Blake-John/SchoolRobotMatch/ComputerVision/Modules/Aim/0.jpg

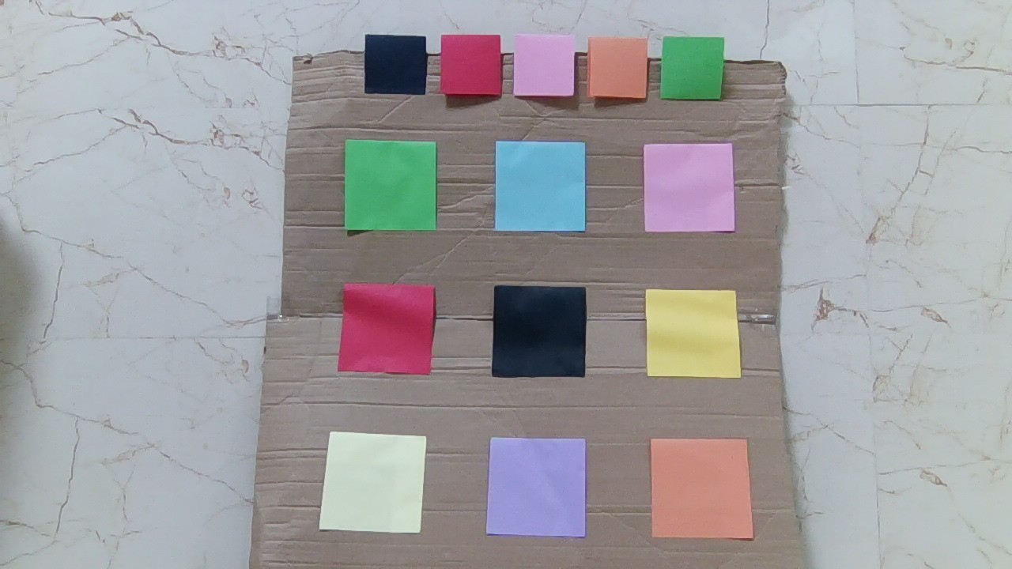
ComputerVision/Modules/Aim/0.jpg
