Blake-John/SchoolRobotMatch/ComputerVision/Modules/Aim/1.jpg

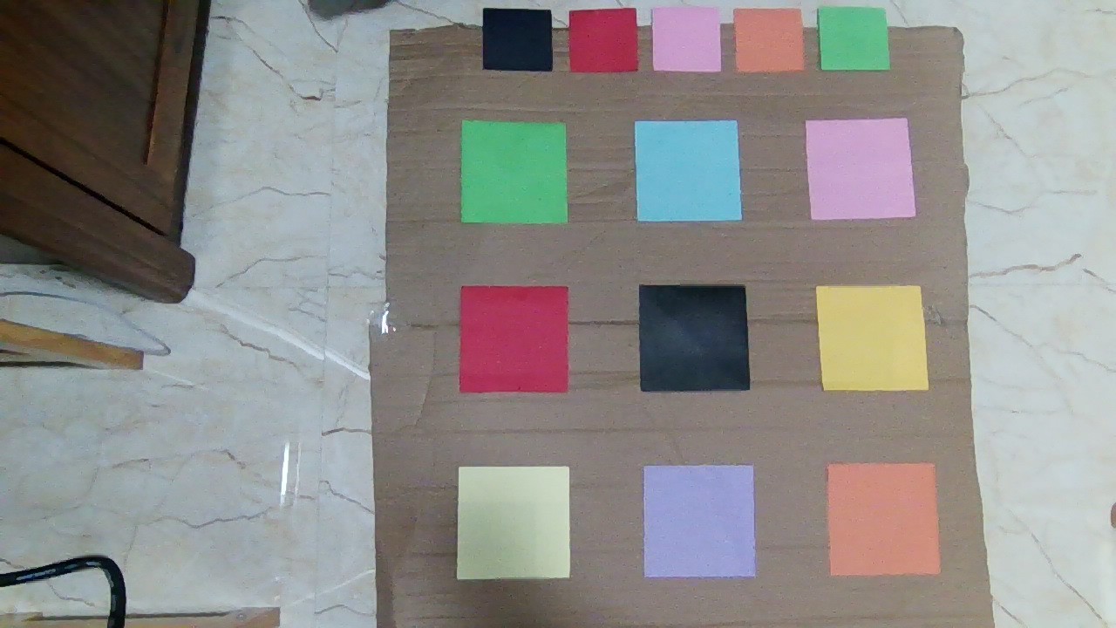
ComputerVision/Modules/Aim/1.jpg
