Blake-John/SchoolRobotMatch/ComputerVision/Modules/AutoAimming/imgs/1-2.png

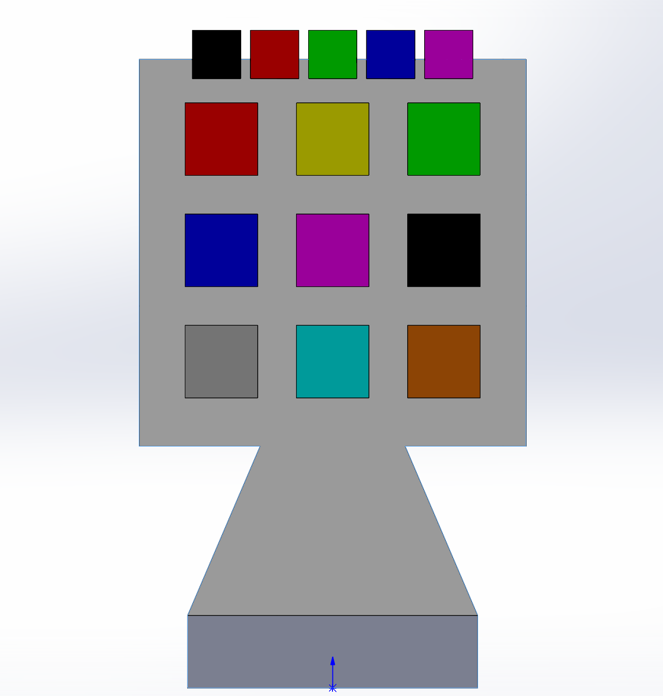
ComputerVision/Modules/AutoAimming/imgs/1-2.png
