Blake-John/SchoolRobotMatch/ComputerVision/Modules/ColorPicker/target.jpg

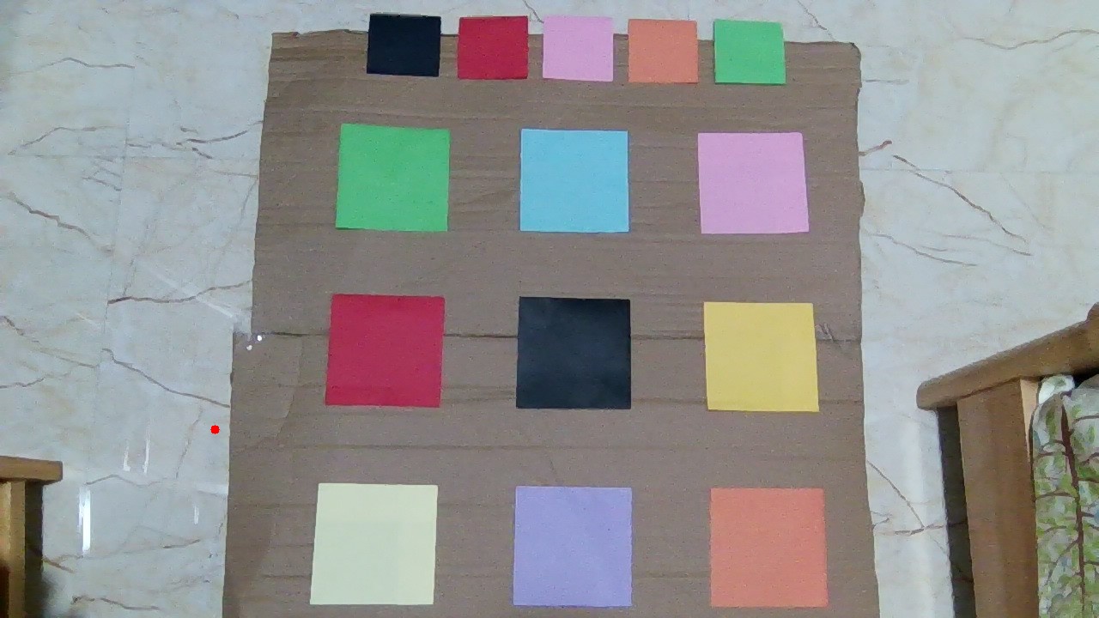
ComputerVision/Modules/ColorPicker/target.jpg
