Blake-John/SchoolRobotMatch/ComputerVision/Modules/GetAngle/4.jpg

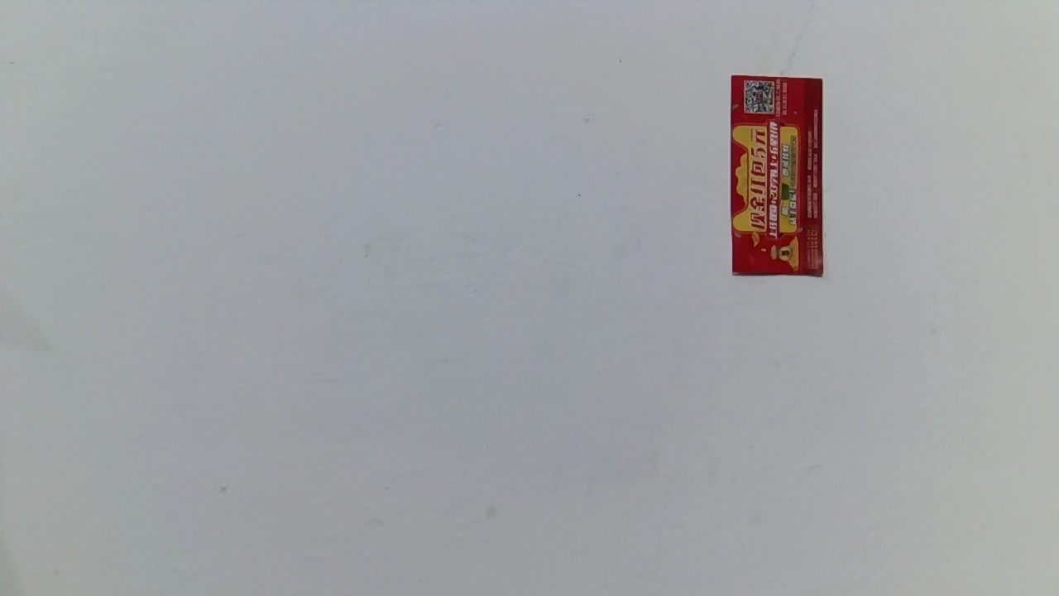
ComputerVision/Modules/GetAngle/4.jpg
