Blake-John/SchoolRobotMatch/ComputerVision/Modules/GetDistance/1.jpg

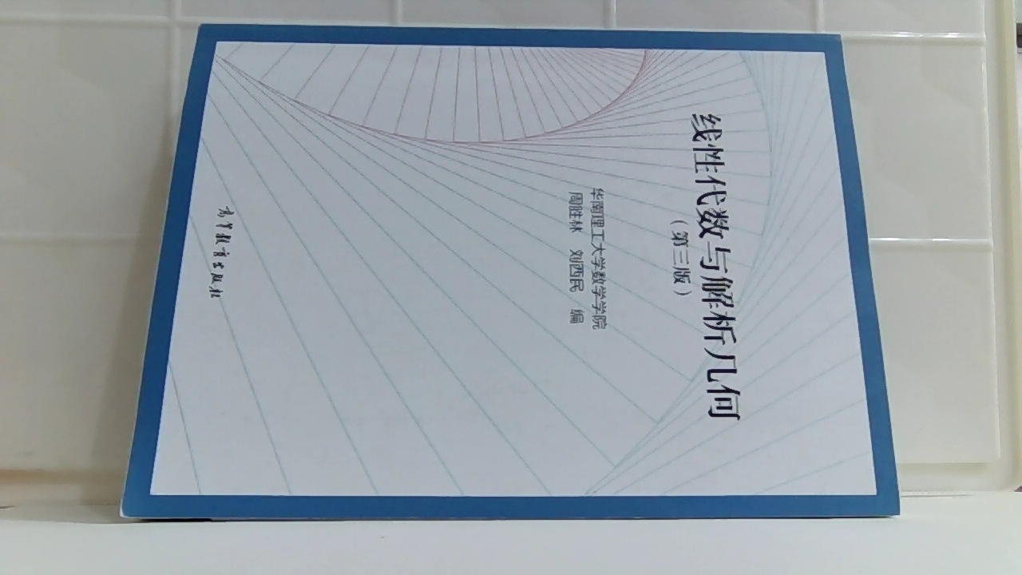
ComputerVision/Modules/GetDistance/1.jpg
