Blake-John/SchoolRobotMatch/ComputerVision/Modules/GetDistance/2.jpg

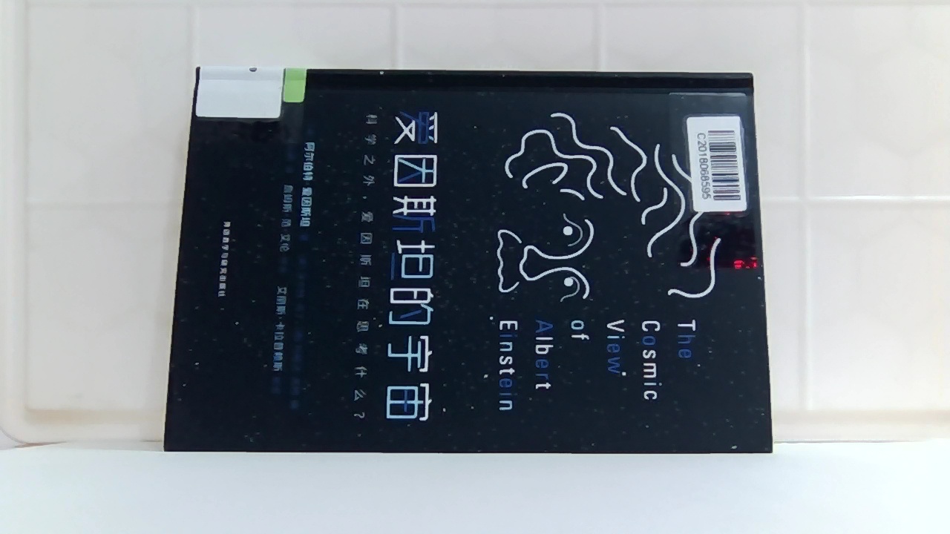
ComputerVision/Modules/GetDistance/2.jpg
