Blake-John/SchoolRobotMatch/ComputerVision/Modules/GetDistance/3.jpg

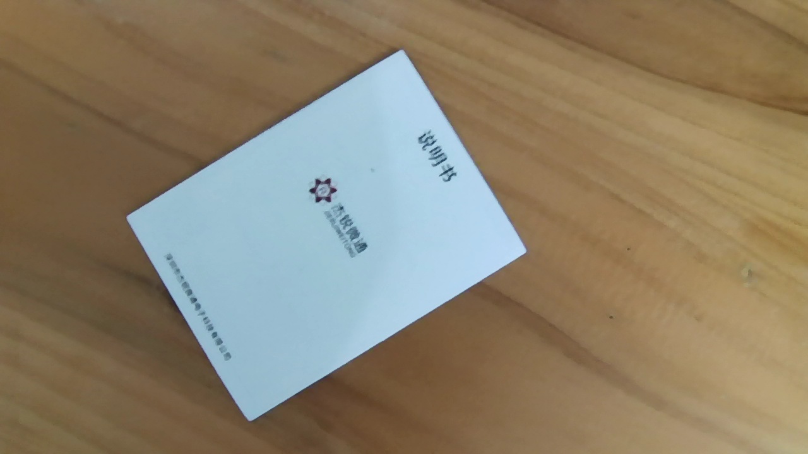
ComputerVision/Modules/GetDistance/3.jpg
