Blake-John/SchoolRobotMatch/ComputerVision/Modules/imgs/106.jpg

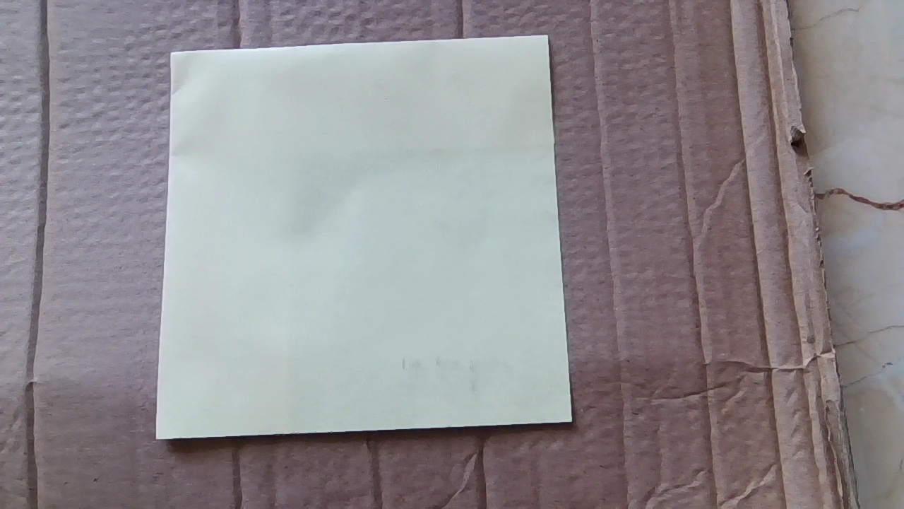
ComputerVision/Modules/imgs/106.jpg
