Blake-John/SchoolRobotMatch/ComputerVision/Modules/imgs/108.jpg

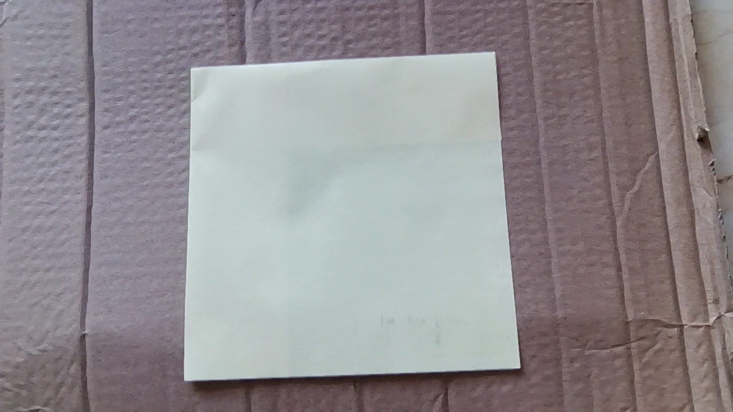
ComputerVision/Modules/imgs/108.jpg
