Blake-John/SchoolRobotMatch/ComputerVision/Modules/imgs/109.jpg

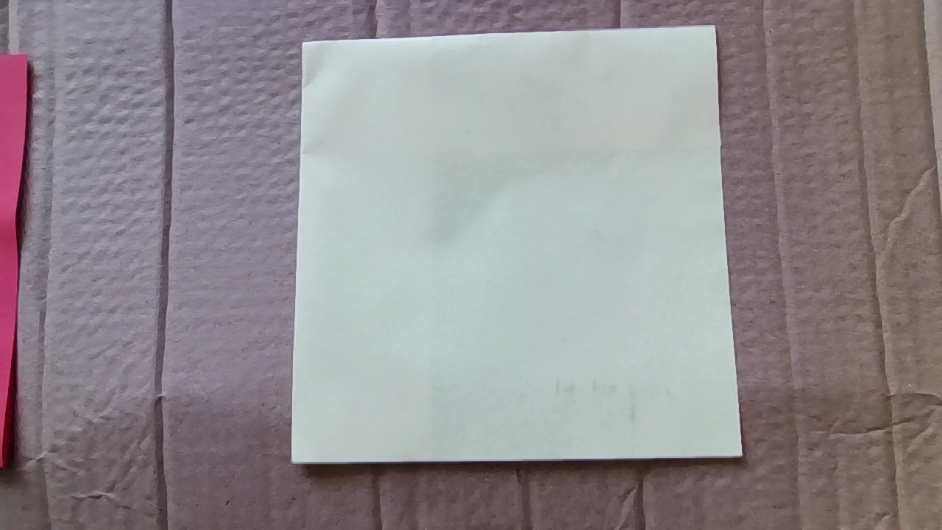
ComputerVision/Modules/imgs/109.jpg
