Blake-John/SchoolRobotMatch/ComputerVision/Modules/imgs/110.jpg

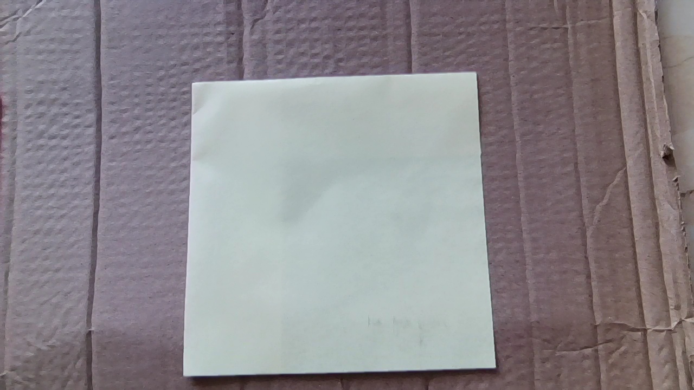
ComputerVision/Modules/imgs/110.jpg
