Blake-John/SchoolRobotMatch/ComputerVision/Modules/imgs/111.jpg

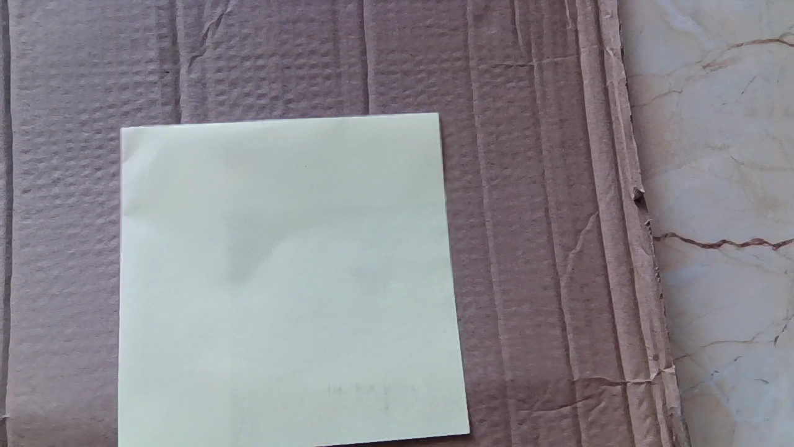
ComputerVision/Modules/imgs/111.jpg
