Blake-John/SchoolRobotMatch/ComputerVision/Modules/imgs/113.jpg

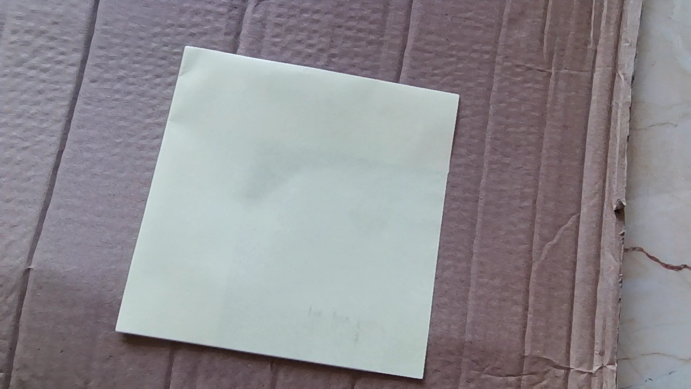
ComputerVision/Modules/imgs/113.jpg
