Blake-John/SchoolRobotMatch/ComputerVision/Modules/imgs/114.jpg

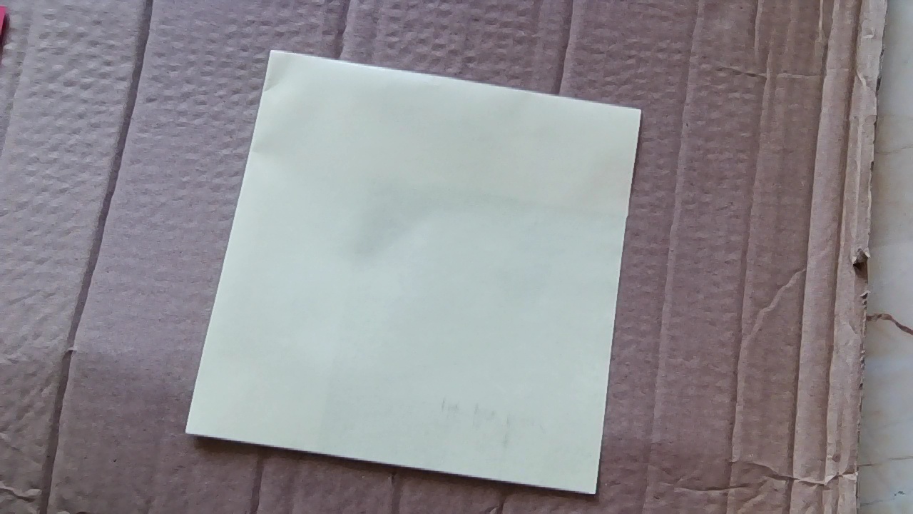
ComputerVision/Modules/imgs/114.jpg
