Blake-John/SchoolRobotMatch/ComputerVision/Modules/imgs/115.jpg

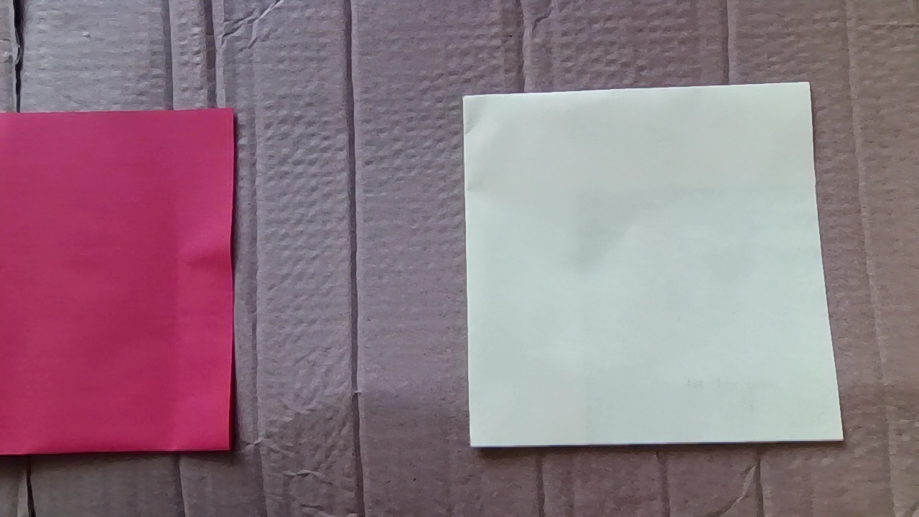
ComputerVision/Modules/imgs/115.jpg
