Blake-John/SchoolRobotMatch/ComputerVision/Modules/imgs/116.jpg

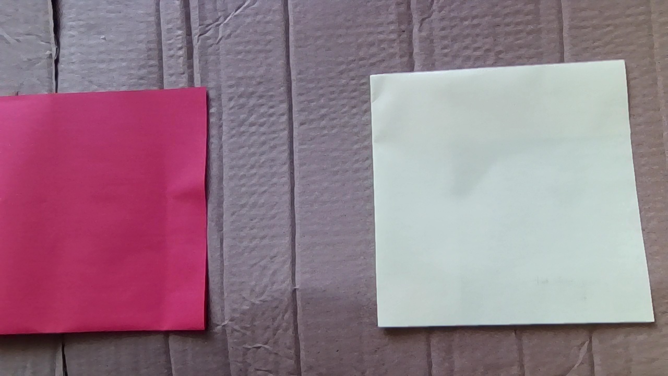
ComputerVision/Modules/imgs/116.jpg
