Blake-John/SchoolRobotMatch/ComputerVision/Modules/imgs/117.jpg

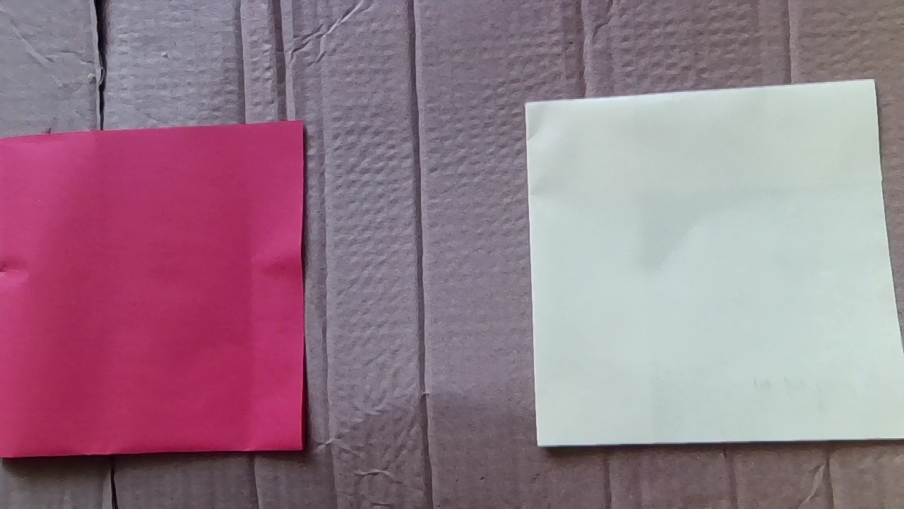
ComputerVision/Modules/imgs/117.jpg
