Blake-John/SchoolRobotMatch/ComputerVision/Modules/imgs/118.jpg

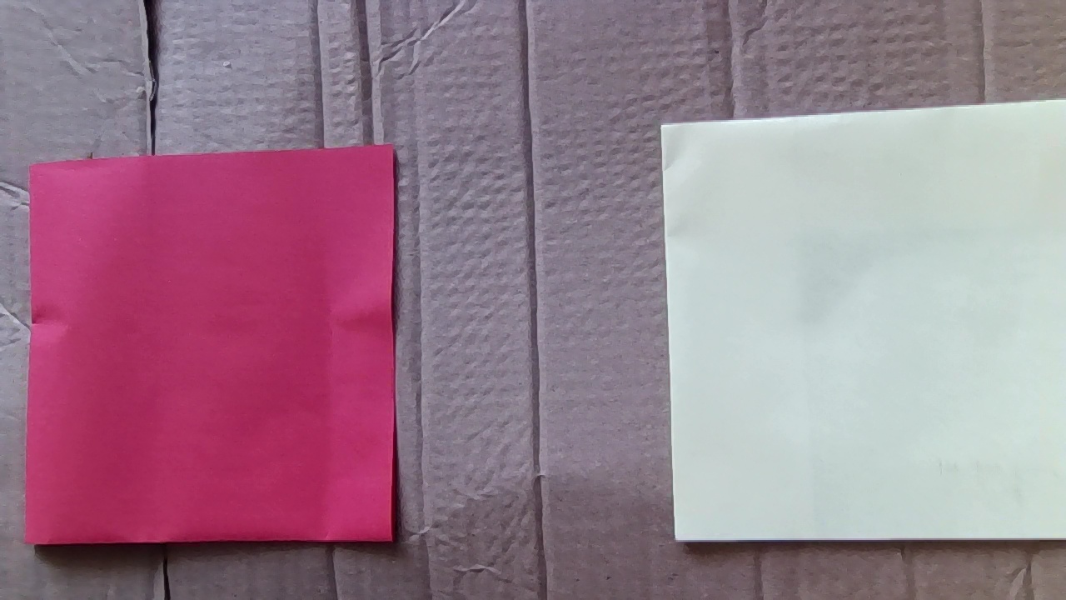
ComputerVision/Modules/imgs/118.jpg
