Blake-John/SchoolRobotMatch/ComputerVision/Modules/imgs/119.jpg

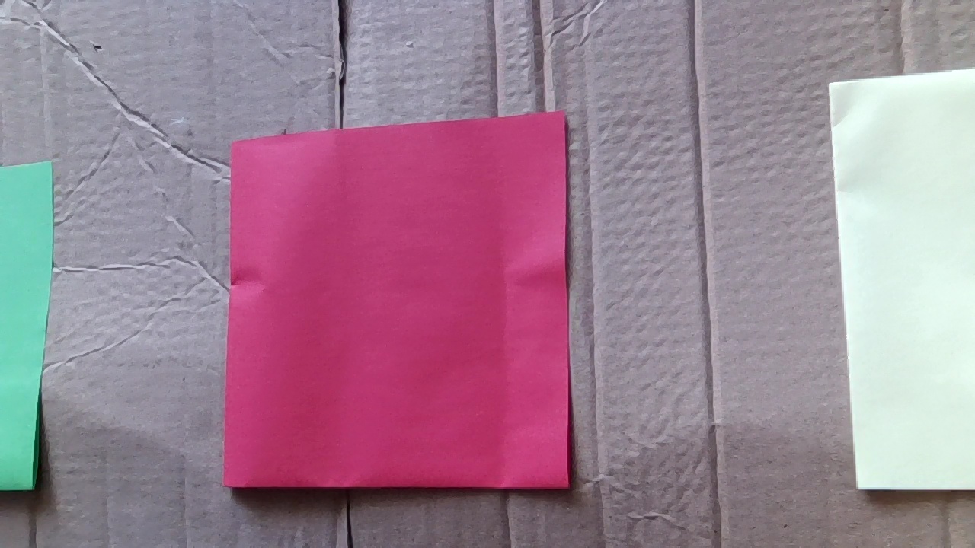
ComputerVision/Modules/imgs/119.jpg
