Blake-John/SchoolRobotMatch/ComputerVision/Modules/imgs/120.jpg

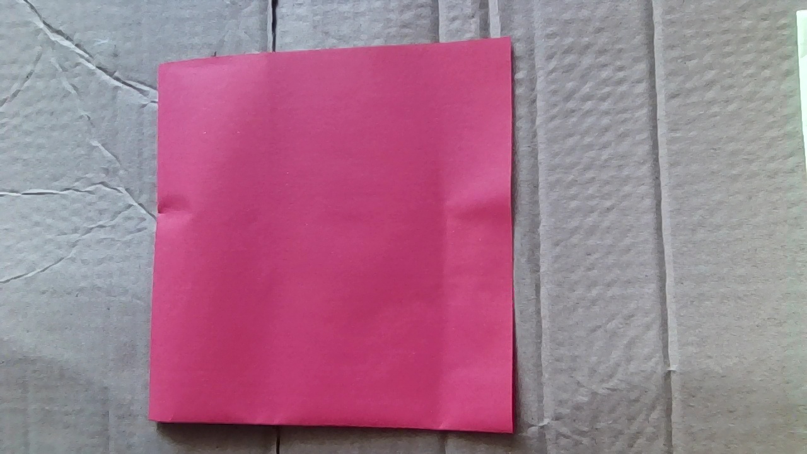
ComputerVision/Modules/imgs/120.jpg
