Blake-John/SchoolRobotMatch/ComputerVision/Modules/imgs/121.jpg

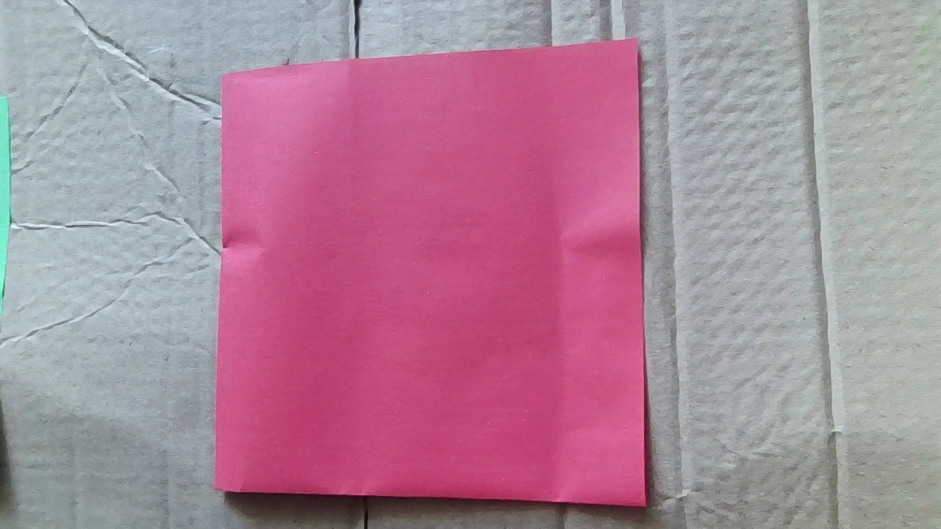
ComputerVision/Modules/imgs/121.jpg
