Blake-John/SchoolRobotMatch/ComputerVision/Modules/imgs/122.jpg

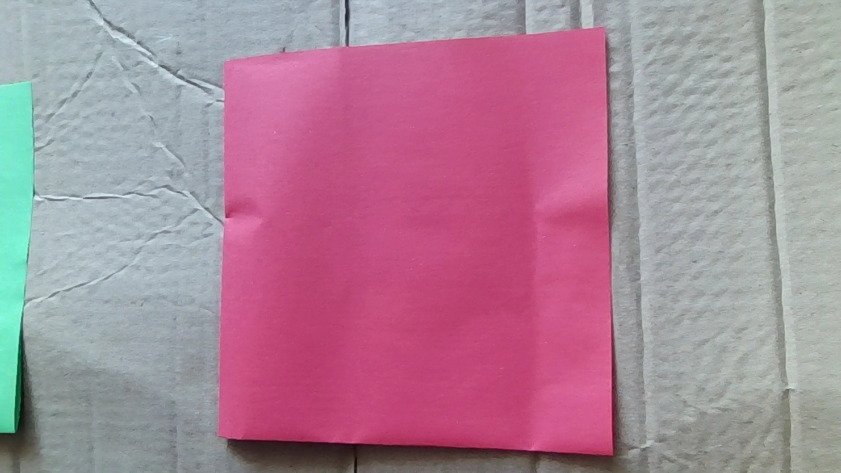
ComputerVision/Modules/imgs/122.jpg
