Blake-John/SchoolRobotMatch/ComputerVision/Modules/imgs/123.jpg

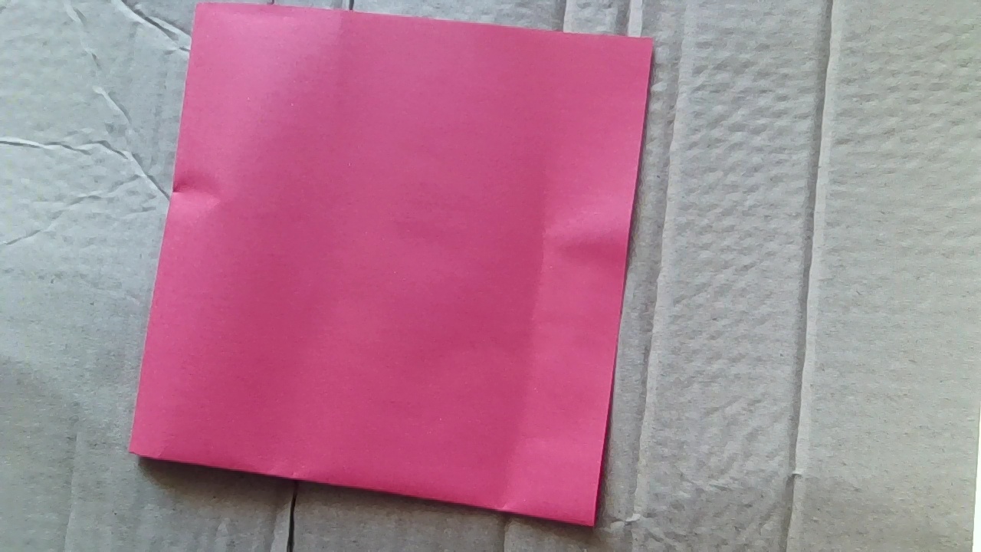
ComputerVision/Modules/imgs/123.jpg
