Blake-John/SchoolRobotMatch/ComputerVision/Modules/imgs/124.jpg

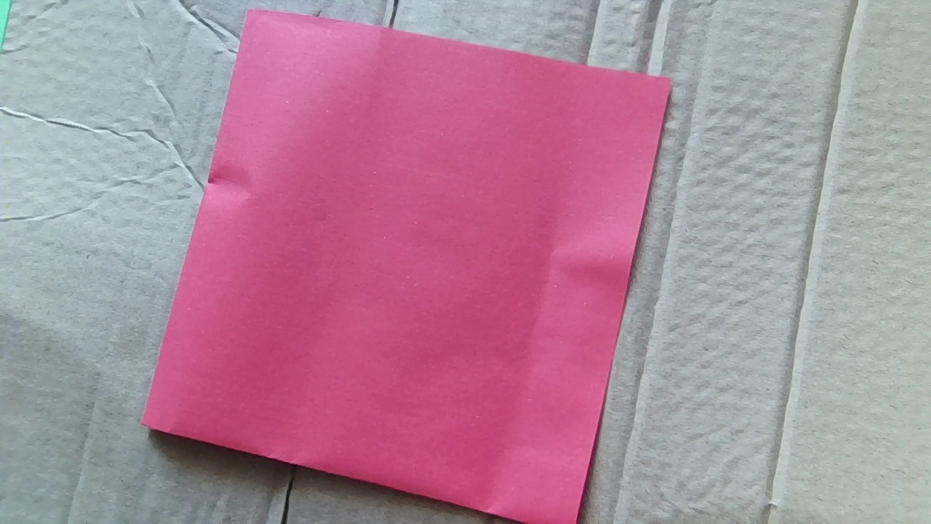
ComputerVision/Modules/imgs/124.jpg
