Blake-John/SchoolRobotMatch/ComputerVision/Modules/imgs/125.jpg

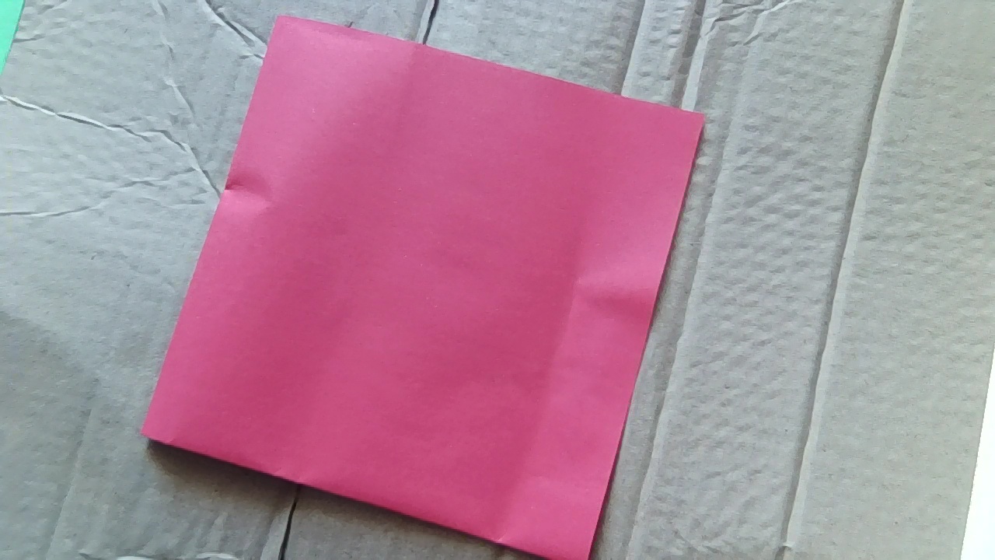
ComputerVision/Modules/imgs/125.jpg
