Blake-John/SchoolRobotMatch/ComputerVision/Modules/imgs/126.jpg

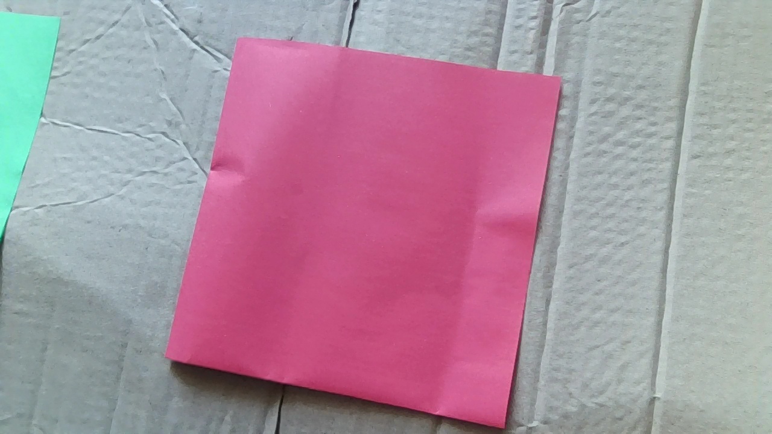
ComputerVision/Modules/imgs/126.jpg
