Blake-John/SchoolRobotMatch/ComputerVision/Modules/imgs/128.jpg

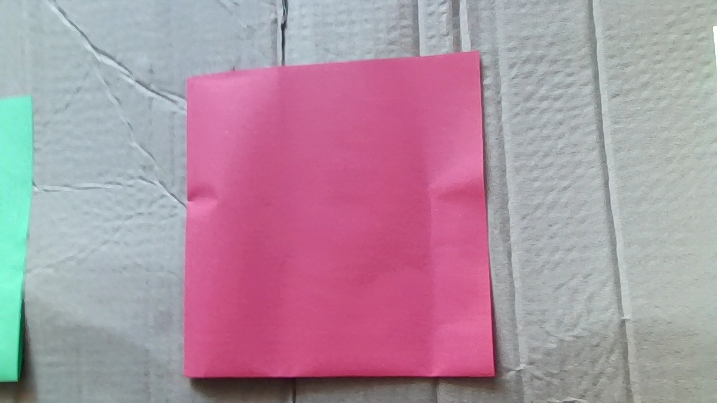
ComputerVision/Modules/imgs/128.jpg
