Blake-John/SchoolRobotMatch/ComputerVision/Modules/imgs/129.jpg

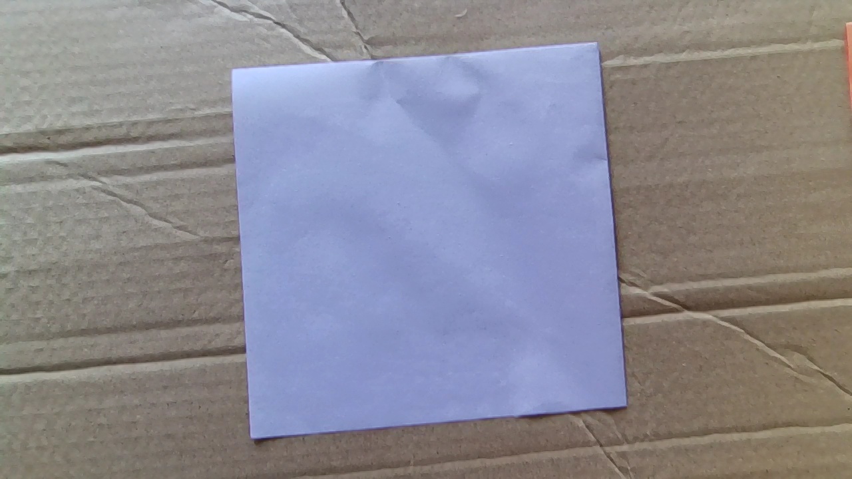
ComputerVision/Modules/imgs/129.jpg
