Blake-John/SchoolRobotMatch/ComputerVision/Modules/imgs/130.jpg

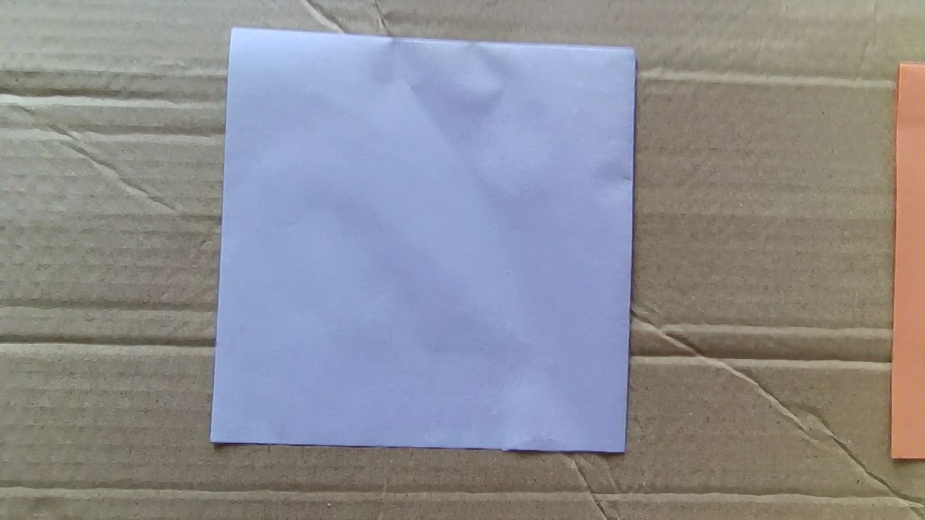
ComputerVision/Modules/imgs/130.jpg
