Blake-John/SchoolRobotMatch/ComputerVision/Modules/imgs/131.jpg

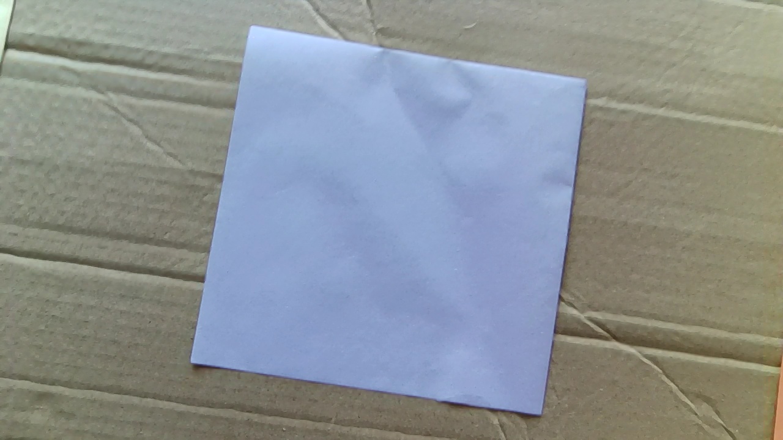
ComputerVision/Modules/imgs/131.jpg
