Blake-John/SchoolRobotMatch/ComputerVision/Modules/imgs/132.jpg

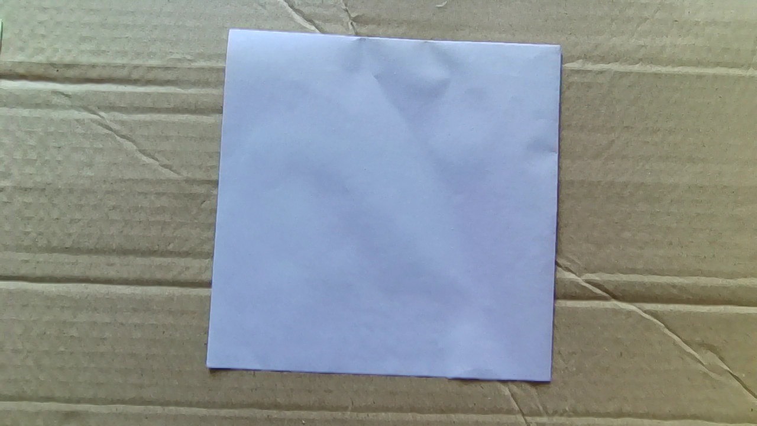
ComputerVision/Modules/imgs/132.jpg
