Blake-John/SchoolRobotMatch/ComputerVision/Modules/imgs/133.jpg

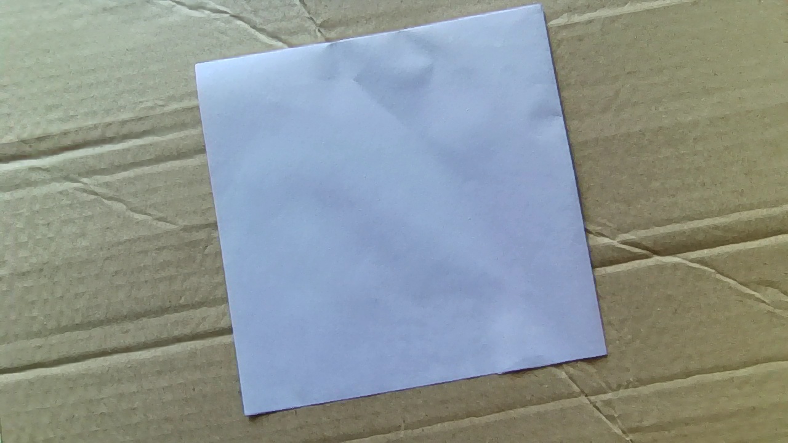
ComputerVision/Modules/imgs/133.jpg
