Blake-John/SchoolRobotMatch/ComputerVision/Modules/imgs/134.jpg

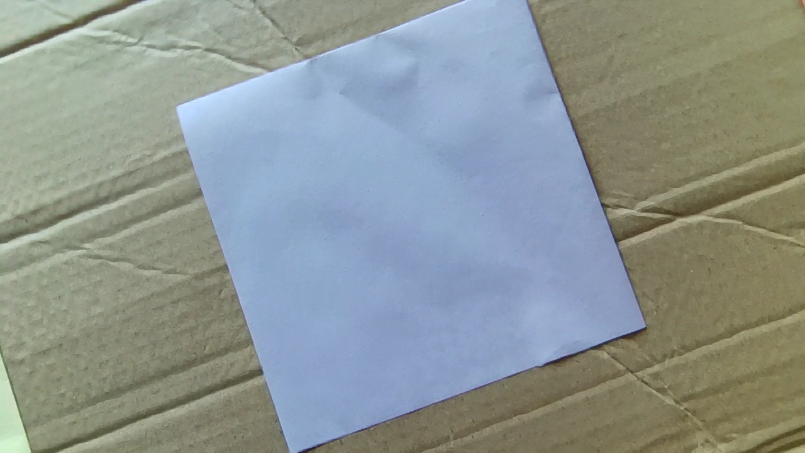
ComputerVision/Modules/imgs/134.jpg
