Blake-John/SchoolRobotMatch/ComputerVision/Modules/imgs/135.jpg

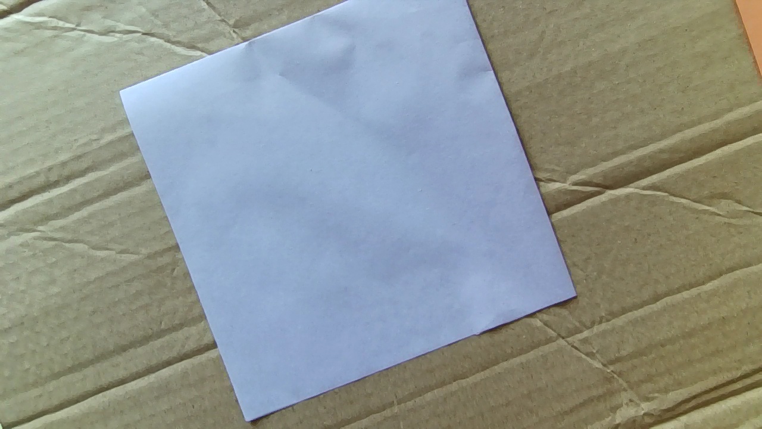
ComputerVision/Modules/imgs/135.jpg
