Blake-John/SchoolRobotMatch/ComputerVision/Modules/imgs/136.jpg

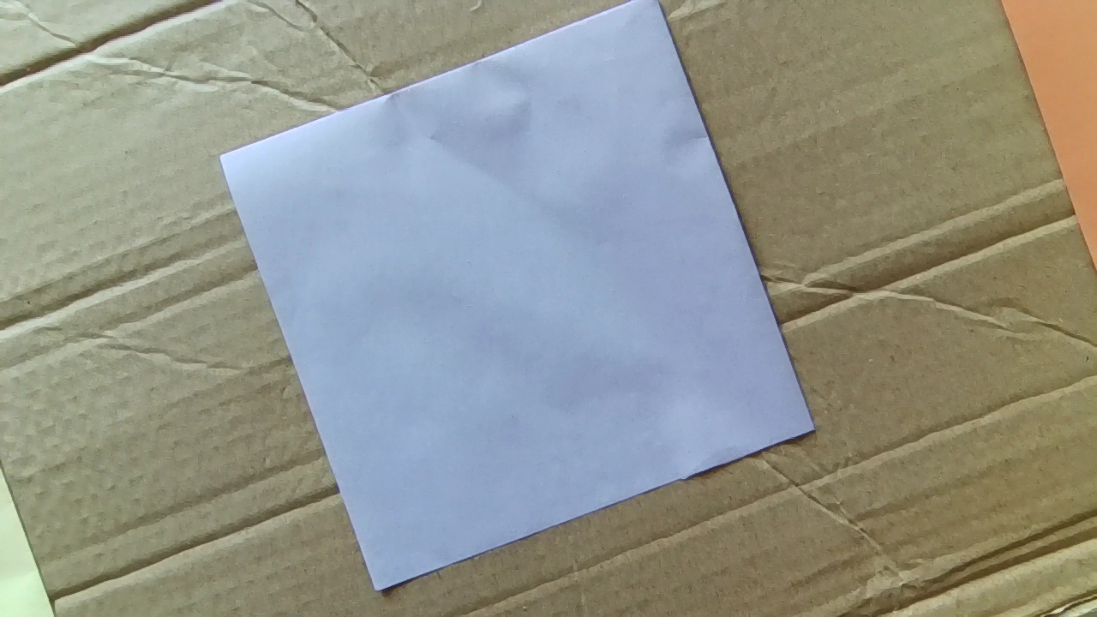
ComputerVision/Modules/imgs/136.jpg
