Blake-John/SchoolRobotMatch/ComputerVision/Modules/imgs/137.jpg

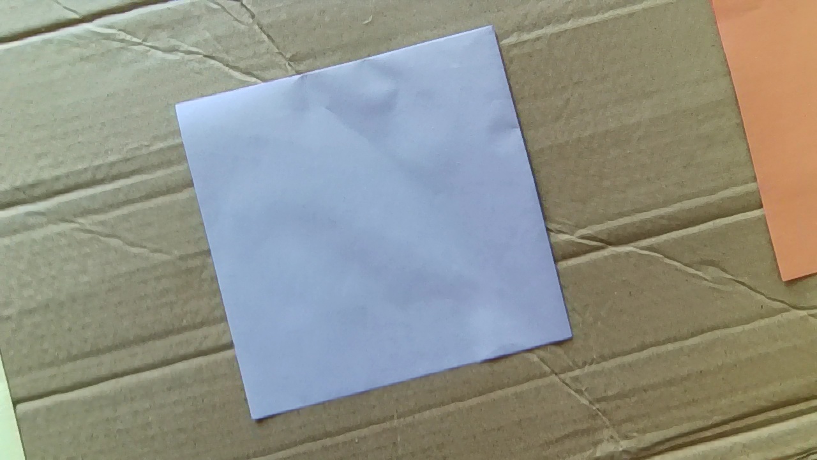
ComputerVision/Modules/imgs/137.jpg
