Blake-John/SchoolRobotMatch/ComputerVision/Modules/imgs/138.jpg

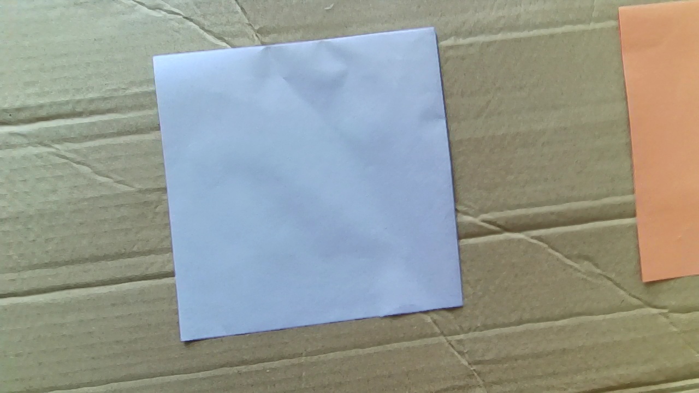
ComputerVision/Modules/imgs/138.jpg
