Blake-John/SchoolRobotMatch/ComputerVision/Modules/imgs/139.jpg

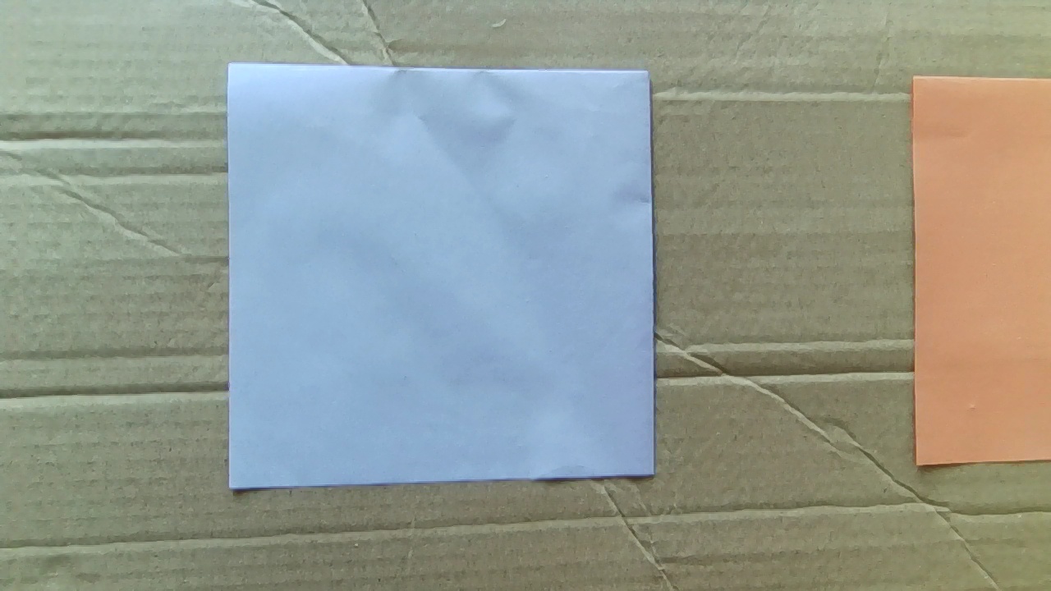
ComputerVision/Modules/imgs/139.jpg
