Blake-John/SchoolRobotMatch/ComputerVision/Modules/imgs/140.jpg

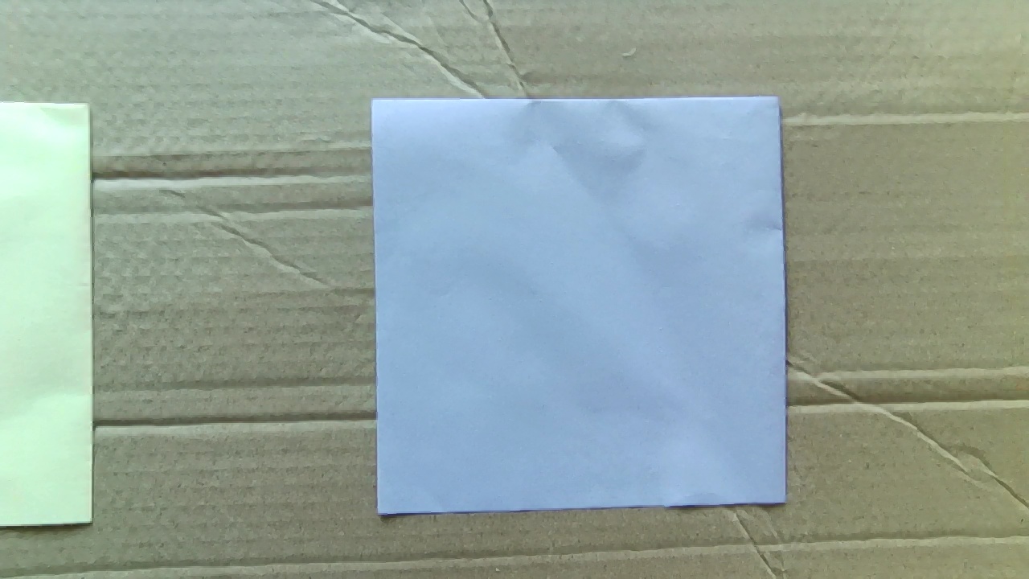
ComputerVision/Modules/imgs/140.jpg
