Blake-John/SchoolRobotMatch/ComputerVision/Modules/imgs/141.jpg

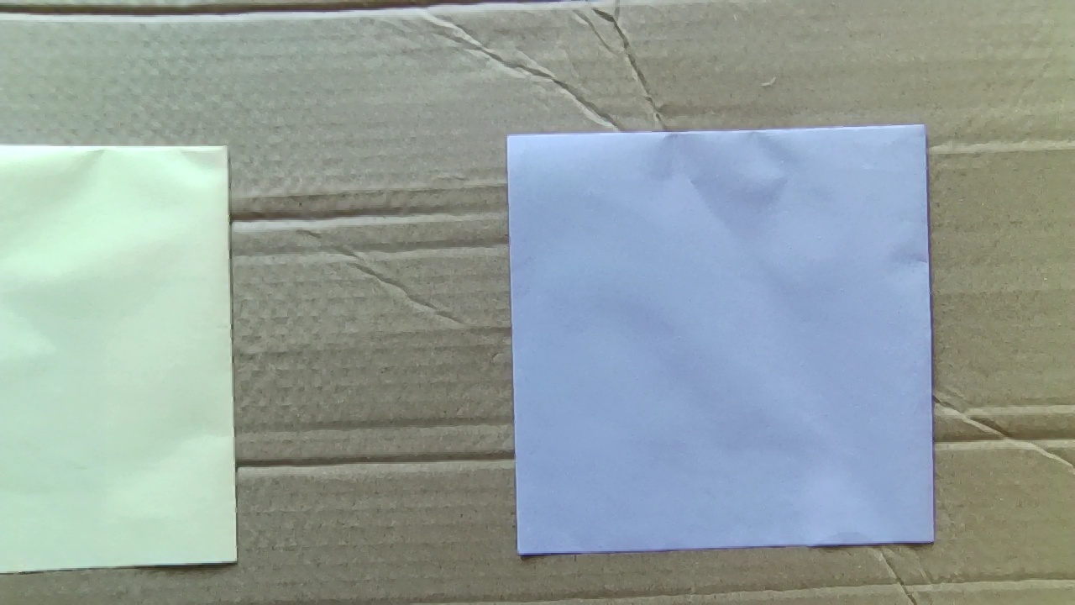
ComputerVision/Modules/imgs/141.jpg
