Blake-John/SchoolRobotMatch/ComputerVision/Modules/imgs/142.jpg

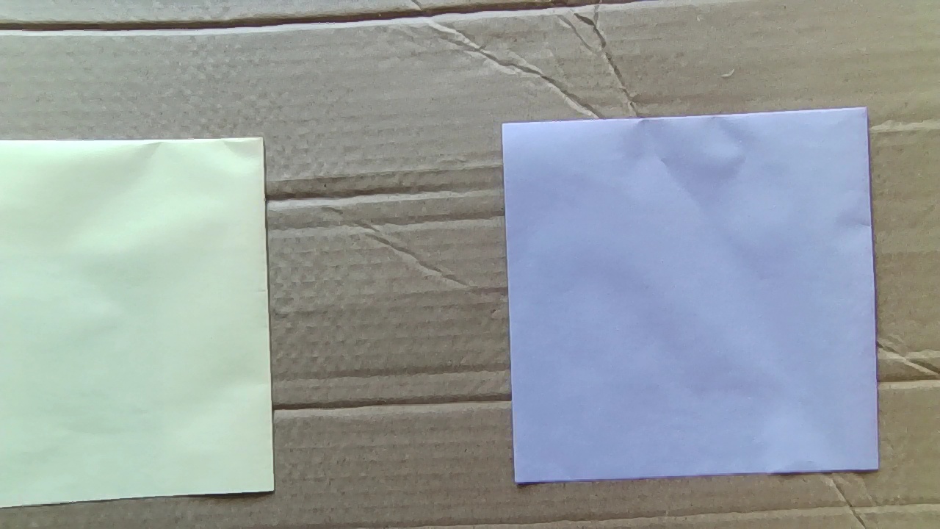
ComputerVision/Modules/imgs/142.jpg
