Blake-John/SchoolRobotMatch/ComputerVision/Modules/imgs/143.jpg

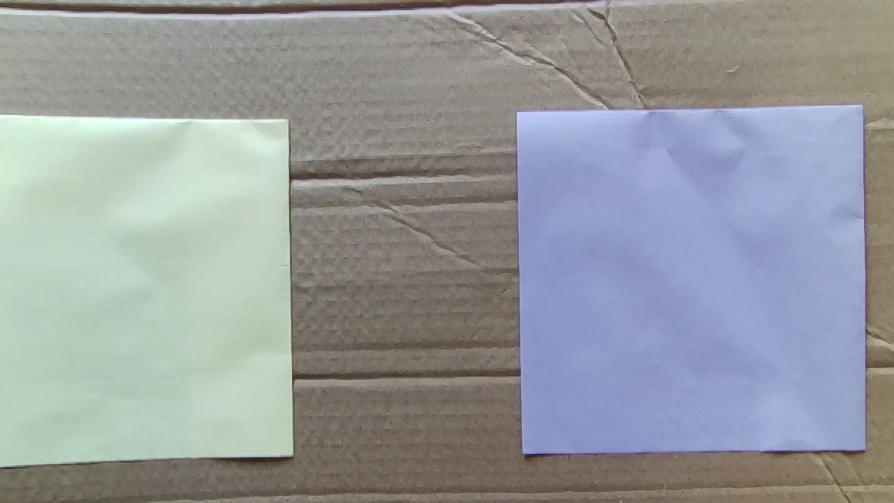
ComputerVision/Modules/imgs/143.jpg
