Blake-John/SchoolRobotMatch/ComputerVision/Modules/imgs/144.jpg

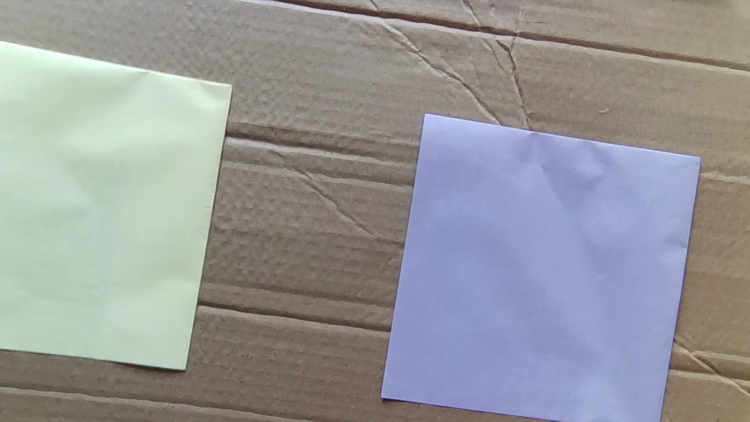
ComputerVision/Modules/imgs/144.jpg
