Blake-John/SchoolRobotMatch/ComputerVision/Modules/imgs/145.jpg

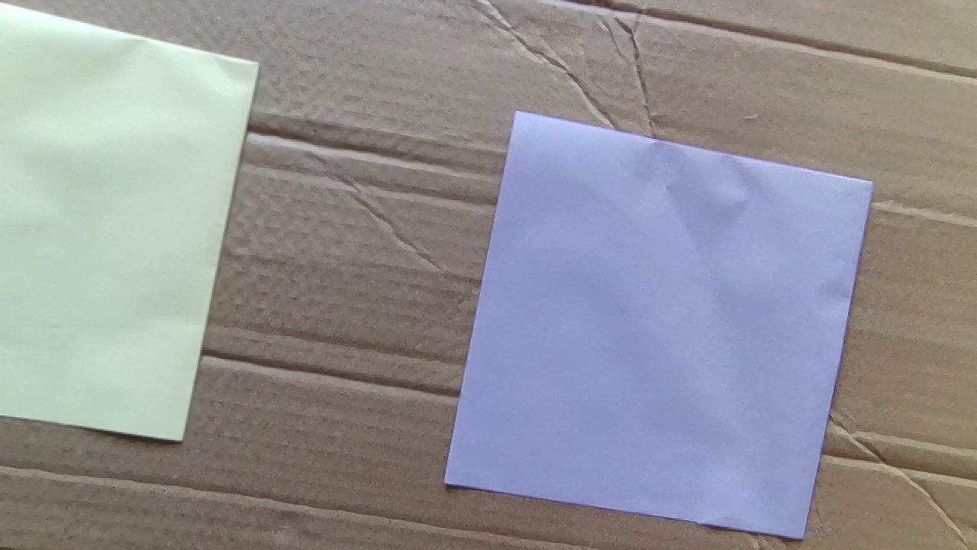
ComputerVision/Modules/imgs/145.jpg
