Blake-John/SchoolRobotMatch/ComputerVision/Modules/imgs/146.jpg

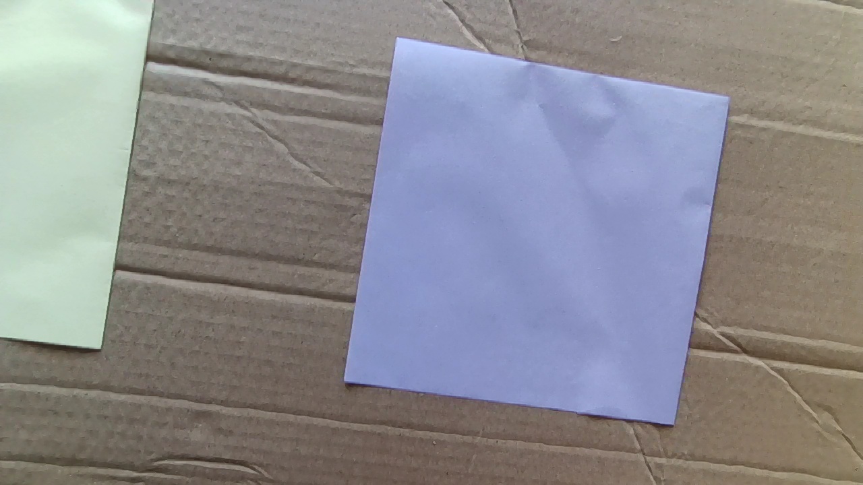
ComputerVision/Modules/imgs/146.jpg
