Blake-John/SchoolRobotMatch/ComputerVision/Modules/imgs/147.jpg

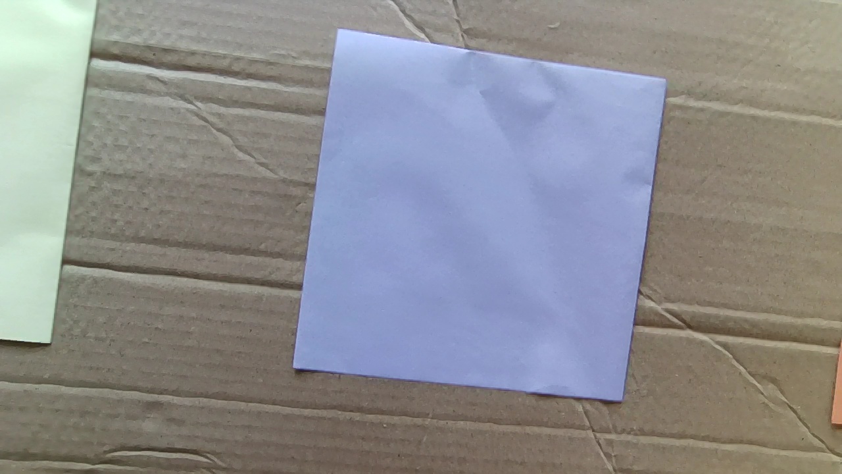
ComputerVision/Modules/imgs/147.jpg
