Blake-John/SchoolRobotMatch/ComputerVision/Modules/imgs/148.jpg

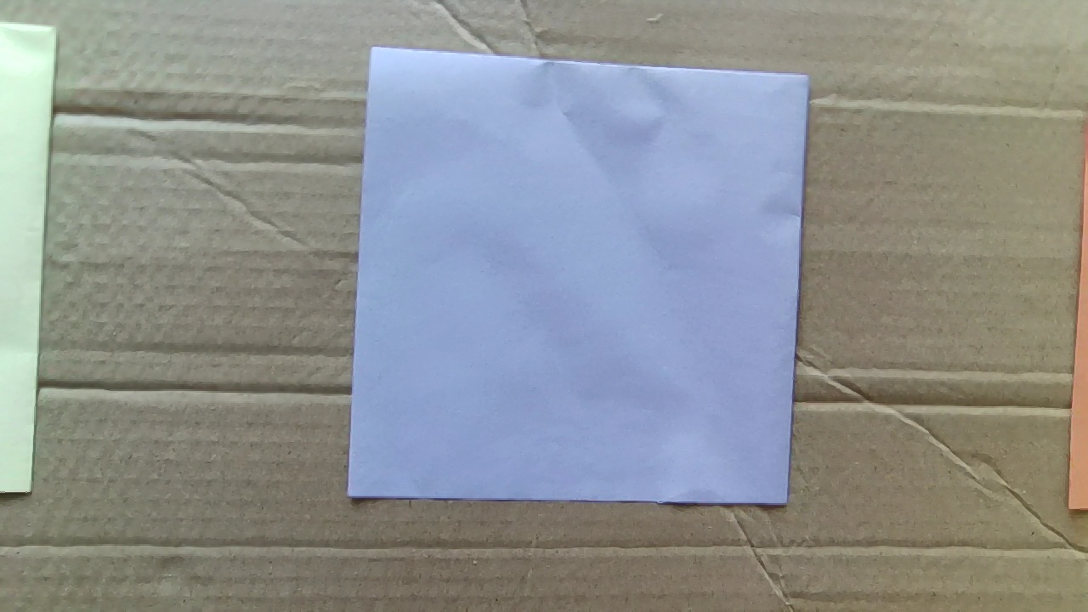
ComputerVision/Modules/imgs/148.jpg
