Blake-John/SchoolRobotMatch/ComputerVision/Modules/imgs/149.jpg

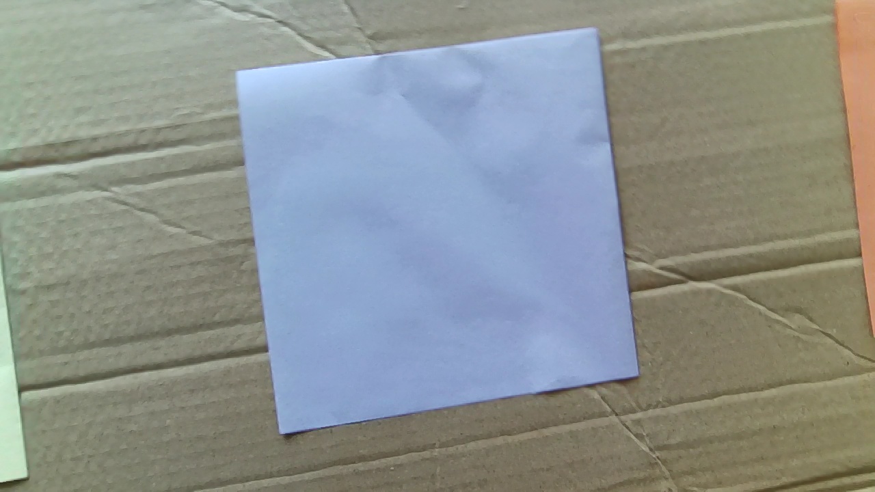
ComputerVision/Modules/imgs/149.jpg
