Blake-John/SchoolRobotMatch/ComputerVision/Modules/imgs/150.jpg

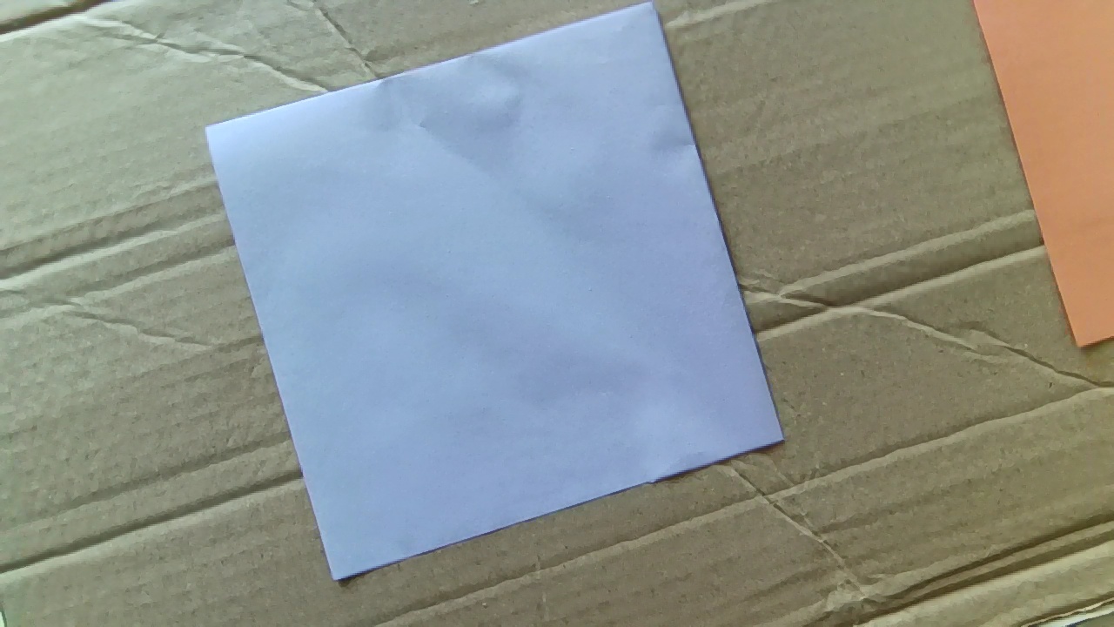
ComputerVision/Modules/imgs/150.jpg
