Blake-John/SchoolRobotMatch/ComputerVision/Modules/imgs/151.jpg

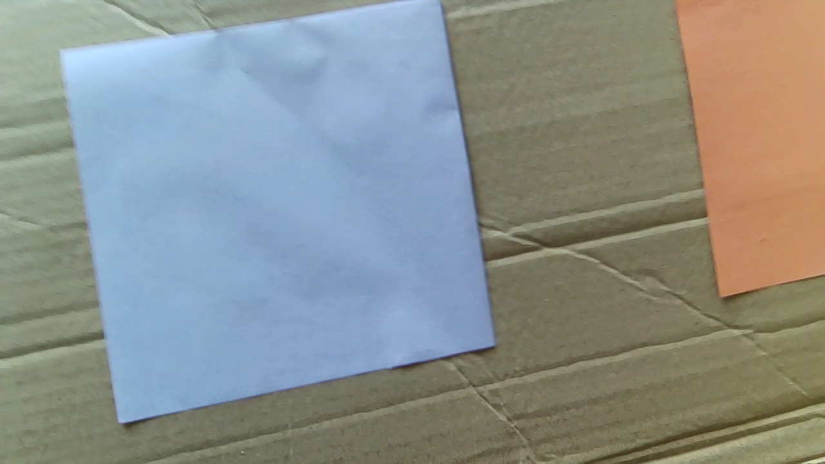
ComputerVision/Modules/imgs/151.jpg
