Blake-John/SchoolRobotMatch/ComputerVision/Modules/imgs/152.jpg

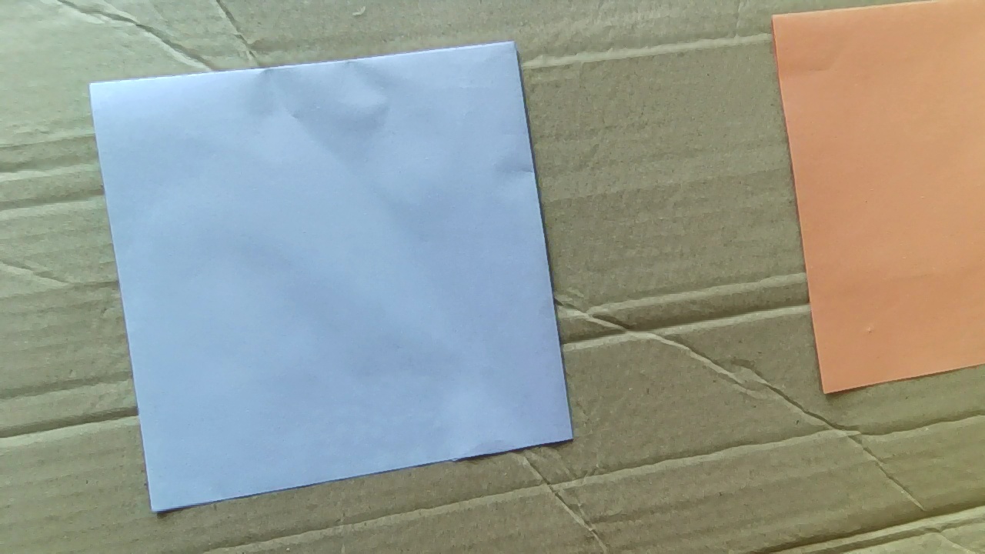
ComputerVision/Modules/imgs/152.jpg
