Blake-John/SchoolRobotMatch/ComputerVision/Modules/imgs/153.jpg

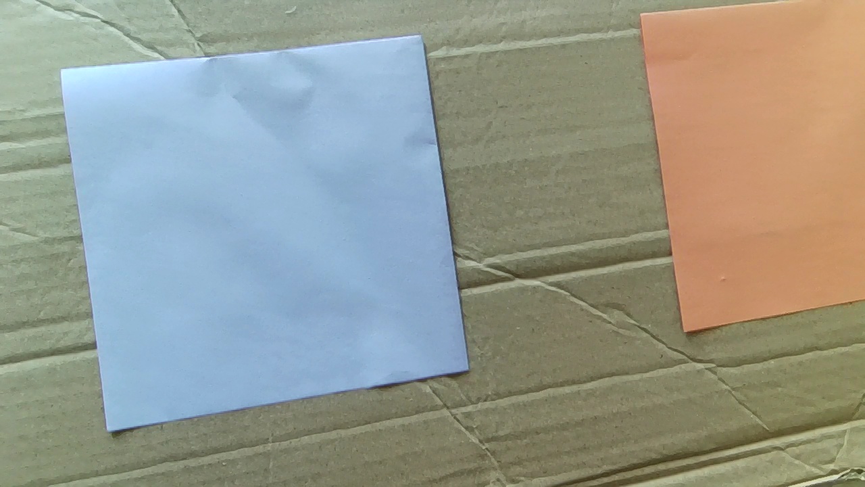
ComputerVision/Modules/imgs/153.jpg
