Blake-John/SchoolRobotMatch/ComputerVision/Modules/imgs/154.jpg

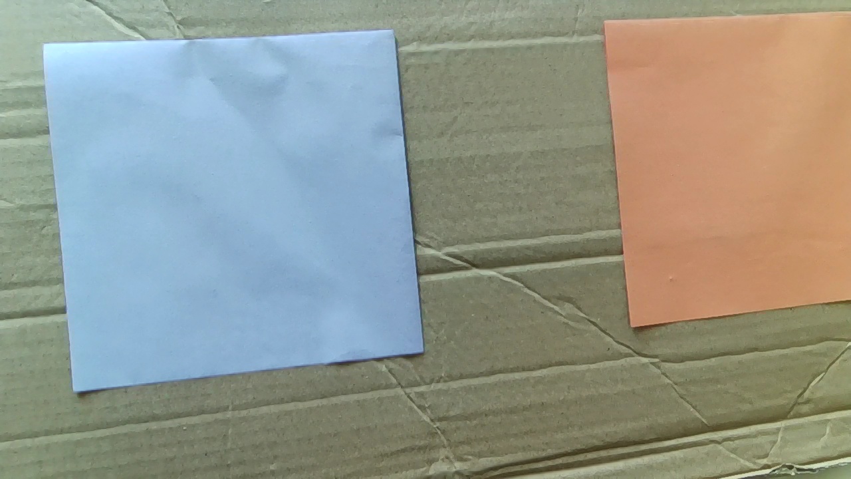
ComputerVision/Modules/imgs/154.jpg
