Blake-John/SchoolRobotMatch/ComputerVision/Modules/imgs/155.jpg

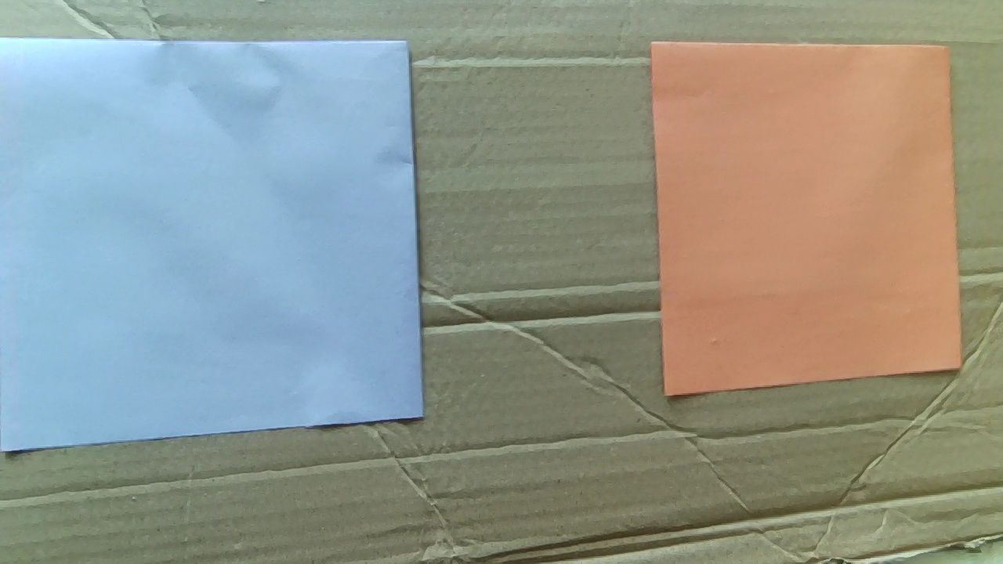
ComputerVision/Modules/imgs/155.jpg
