Blake-John/SchoolRobotMatch/ComputerVision/Modules/imgs/156.jpg

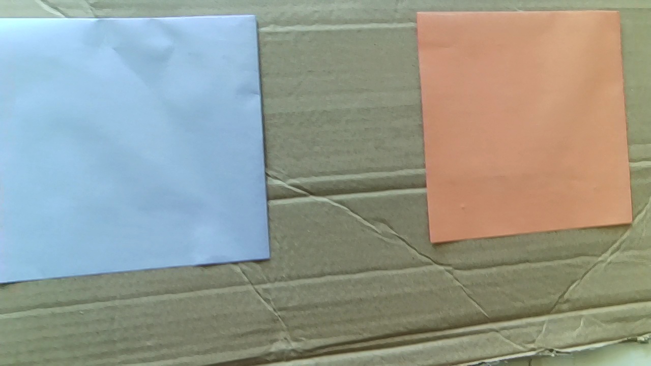
ComputerVision/Modules/imgs/156.jpg
