Blake-John/SchoolRobotMatch/ComputerVision/Modules/imgs/157.jpg

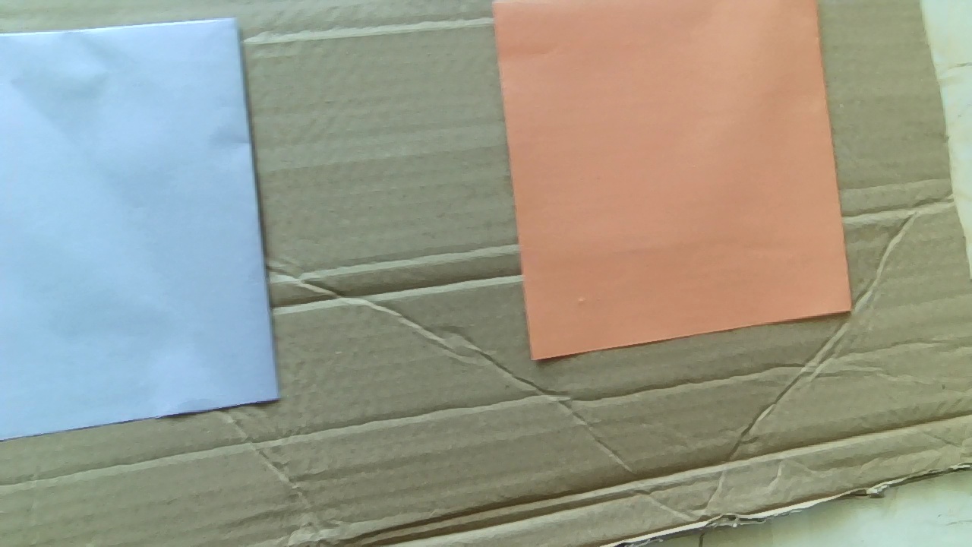
ComputerVision/Modules/imgs/157.jpg
