Blake-John/SchoolRobotMatch/ComputerVision/Modules/imgs/158.jpg

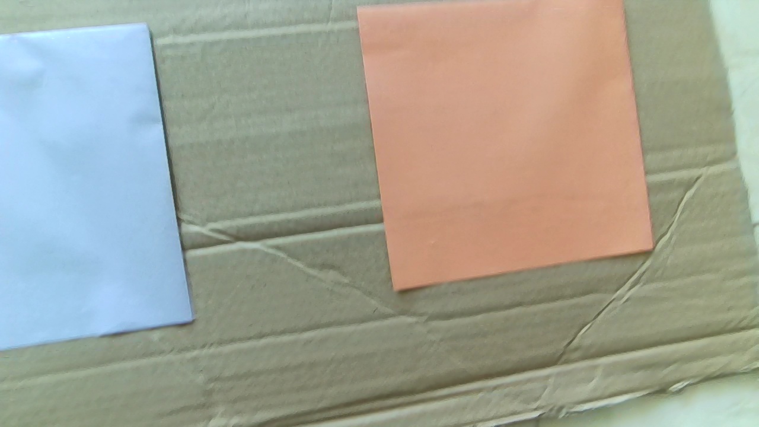
ComputerVision/Modules/imgs/158.jpg
