Blake-John/SchoolRobotMatch/ComputerVision/Modules/imgs/159.jpg

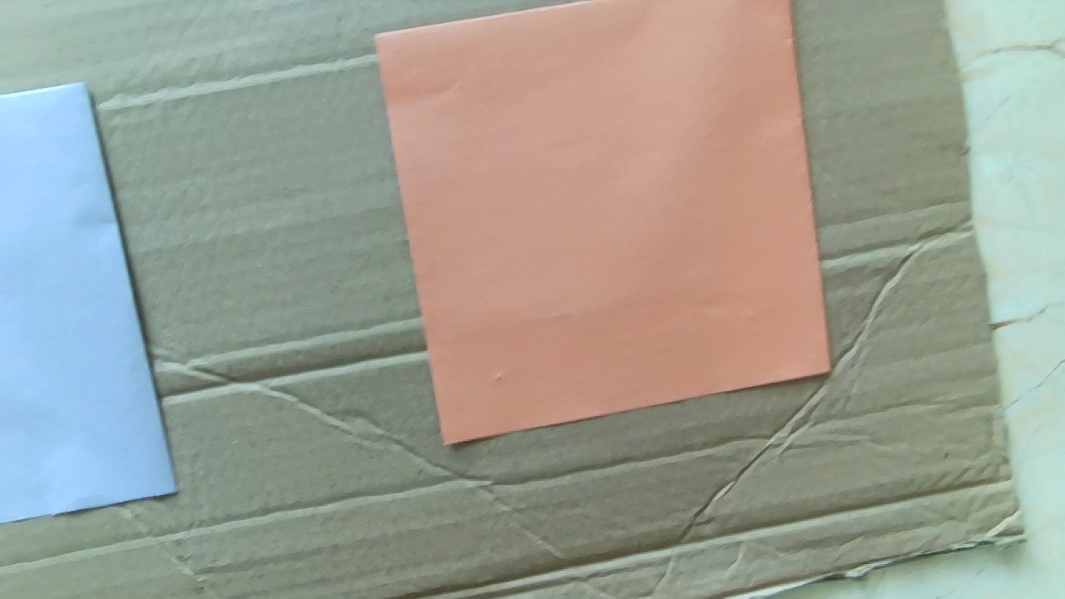
ComputerVision/Modules/imgs/159.jpg
