Blake-John/SchoolRobotMatch/ComputerVision/Modules/imgs/160.jpg

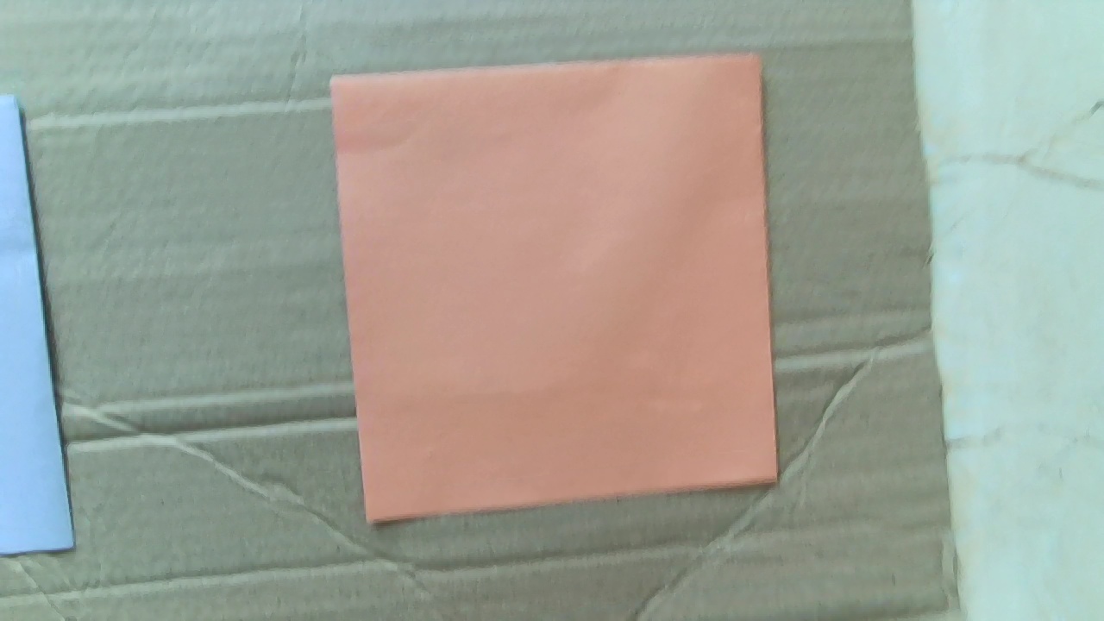
ComputerVision/Modules/imgs/160.jpg
