Blake-John/SchoolRobotMatch/ComputerVision/Modules/imgs/161.jpg

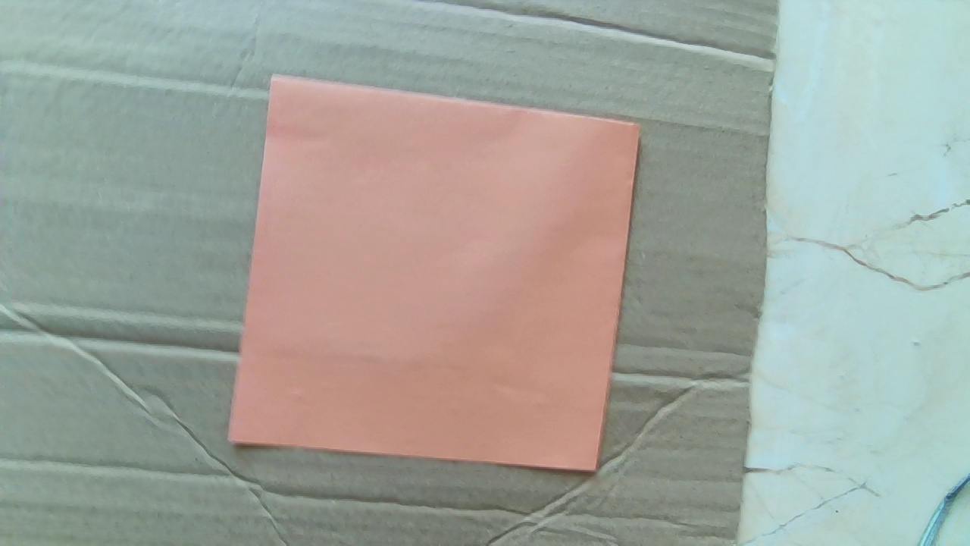
ComputerVision/Modules/imgs/161.jpg
