Blake-John/SchoolRobotMatch/ComputerVision/Modules/imgs/162.jpg

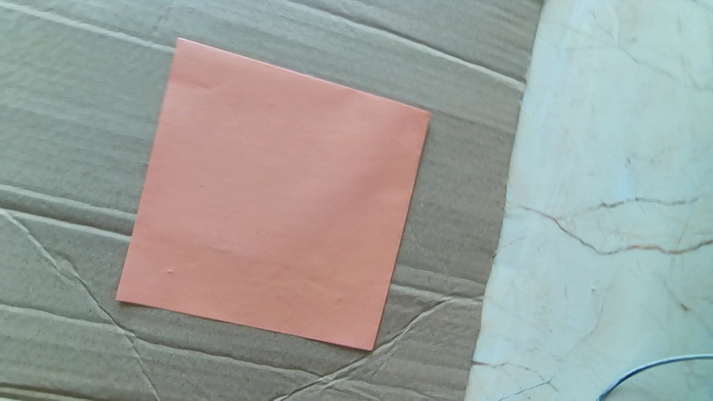
ComputerVision/Modules/imgs/162.jpg
