Blake-John/SchoolRobotMatch/ComputerVision/Modules/imgs/163.jpg

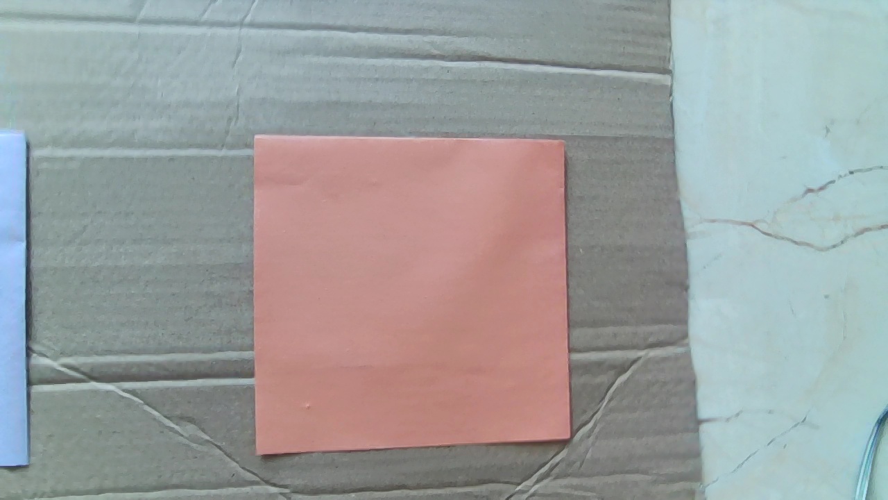
ComputerVision/Modules/imgs/163.jpg
