Blake-John/SchoolRobotMatch/ComputerVision/Modules/imgs/164.jpg

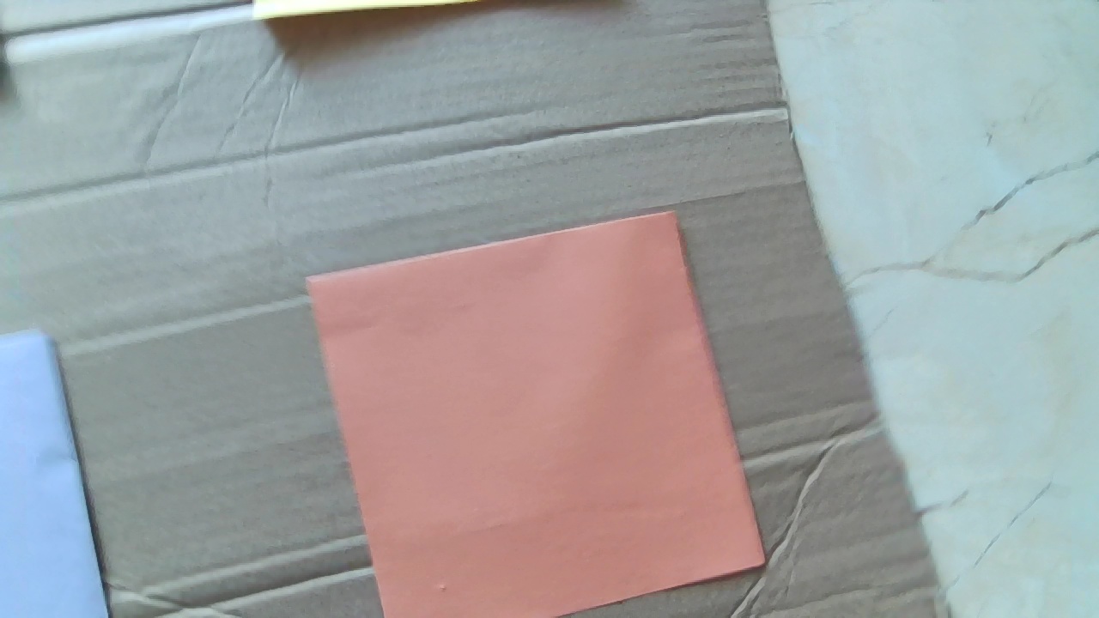
ComputerVision/Modules/imgs/164.jpg
