Blake-John/SchoolRobotMatch/ComputerVision/Modules/imgs/165.jpg

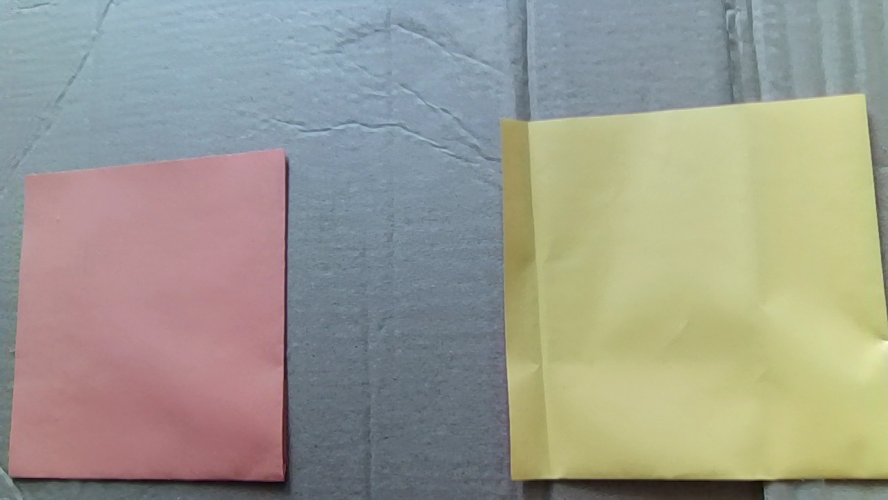
ComputerVision/Modules/imgs/165.jpg
