Blake-John/SchoolRobotMatch/ComputerVision/Modules/imgs/166.jpg

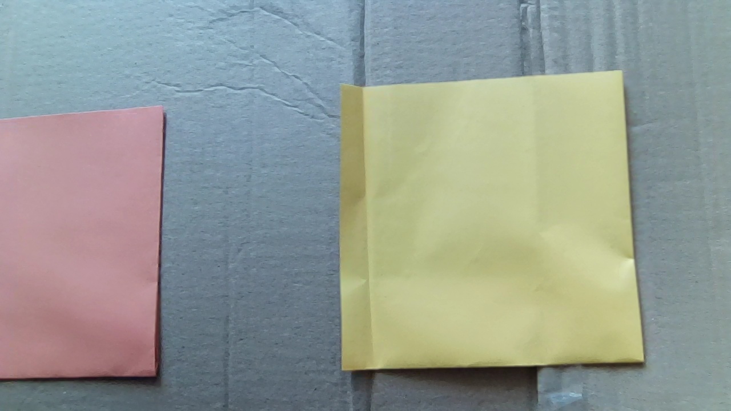
ComputerVision/Modules/imgs/166.jpg
