Blake-John/SchoolRobotMatch/ComputerVision/Modules/imgs/167.jpg

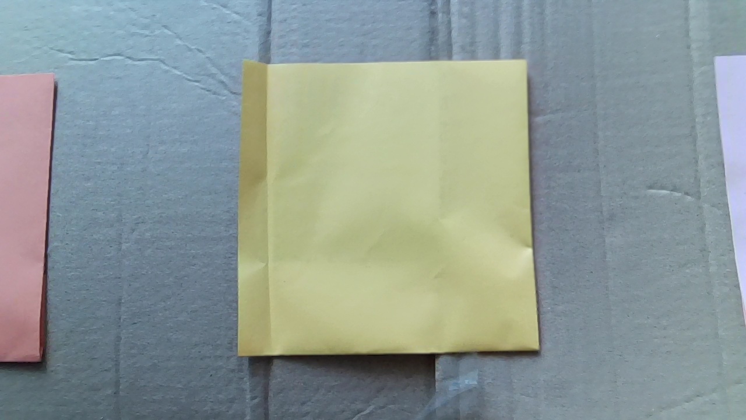
ComputerVision/Modules/imgs/167.jpg
