Blake-John/SchoolRobotMatch/ComputerVision/Modules/imgs/168.jpg

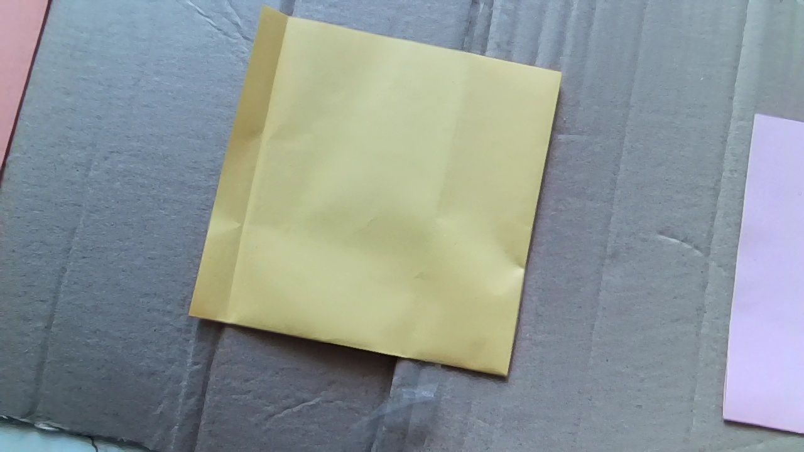
ComputerVision/Modules/imgs/168.jpg
