Blake-John/SchoolRobotMatch/ComputerVision/Modules/imgs/169.jpg

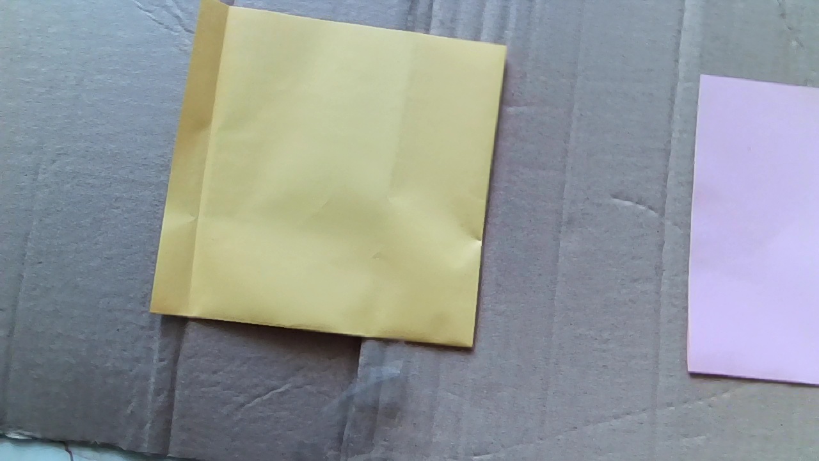
ComputerVision/Modules/imgs/169.jpg
