Blake-John/SchoolRobotMatch/ComputerVision/Modules/imgs/170.jpg

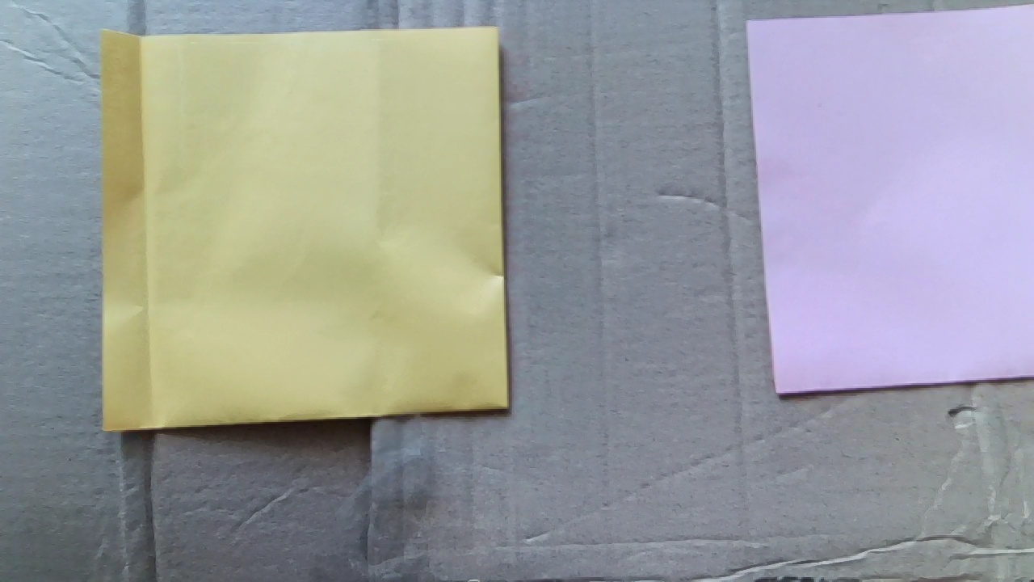
ComputerVision/Modules/imgs/170.jpg
