Blake-John/SchoolRobotMatch/ComputerVision/Modules/imgs/171.jpg

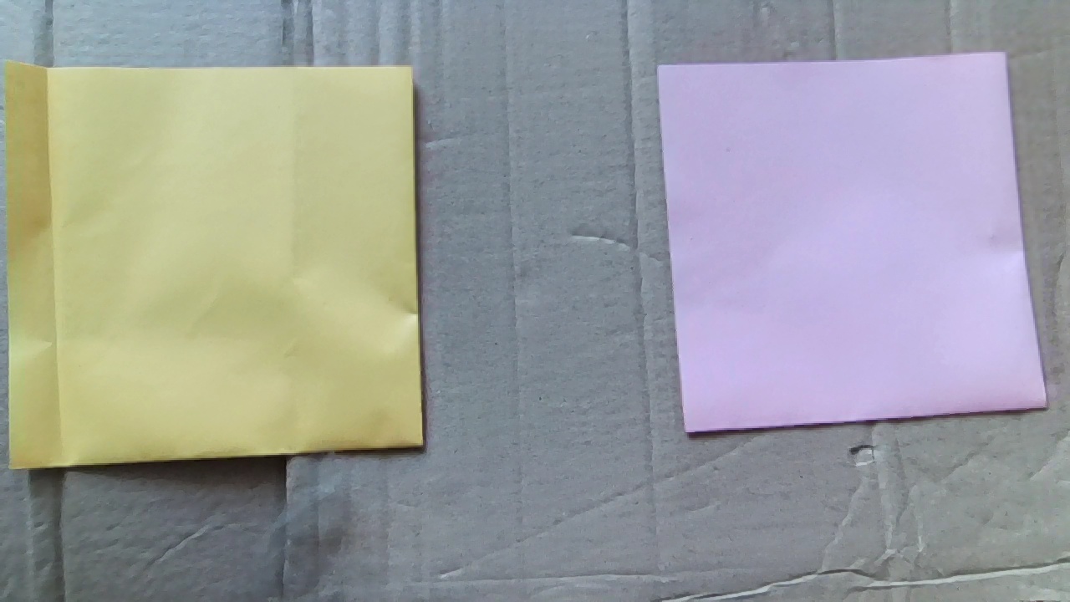
ComputerVision/Modules/imgs/171.jpg
