Blake-John/SchoolRobotMatch/ComputerVision/Modules/imgs/172.jpg

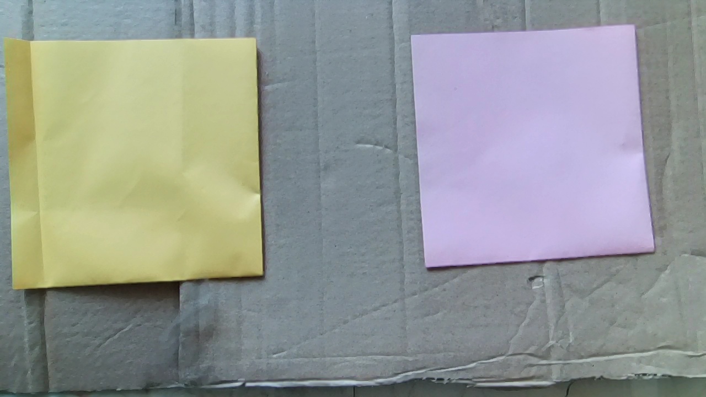
ComputerVision/Modules/imgs/172.jpg
