Blake-John/SchoolRobotMatch/ComputerVision/Modules/imgs/173.jpg

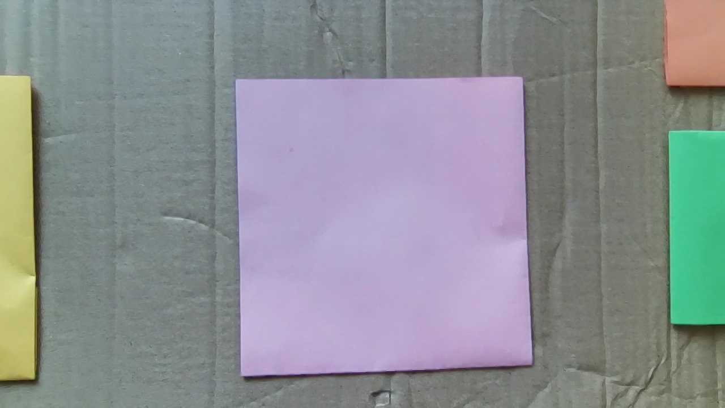
ComputerVision/Modules/imgs/173.jpg
