Blake-John/SchoolRobotMatch/ComputerVision/Modules/imgs/174.jpg

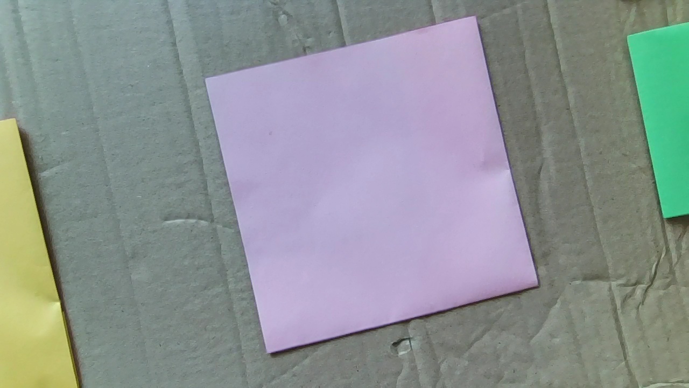
ComputerVision/Modules/imgs/174.jpg
