Blake-John/SchoolRobotMatch/ComputerVision/Modules/imgs/175.jpg

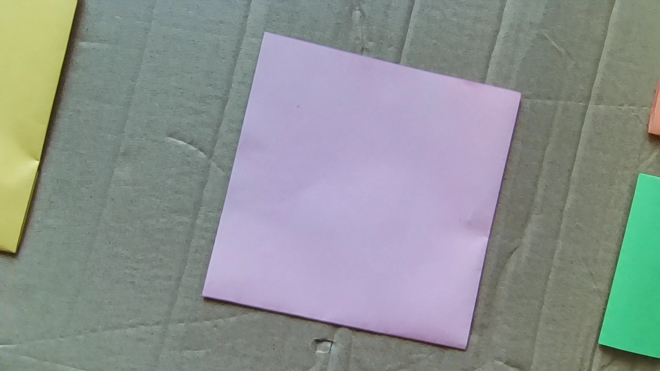
ComputerVision/Modules/imgs/175.jpg
