Blake-John/SchoolRobotMatch/ComputerVision/Modules/imgs/176.jpg

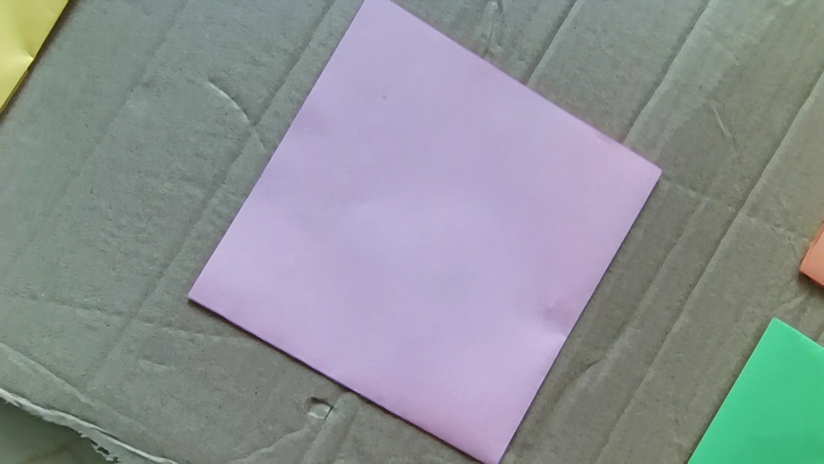
ComputerVision/Modules/imgs/176.jpg
