Blake-John/SchoolRobotMatch/ComputerVision/Modules/imgs/177.jpg

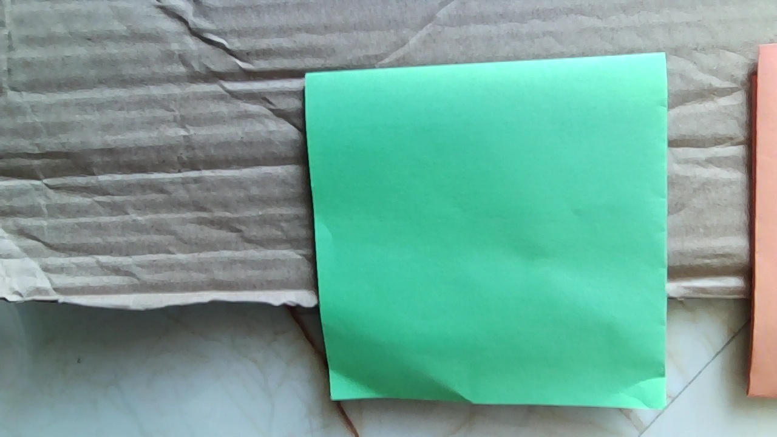
ComputerVision/Modules/imgs/177.jpg
