Blake-John/SchoolRobotMatch/ComputerVision/Modules/imgs/178.jpg

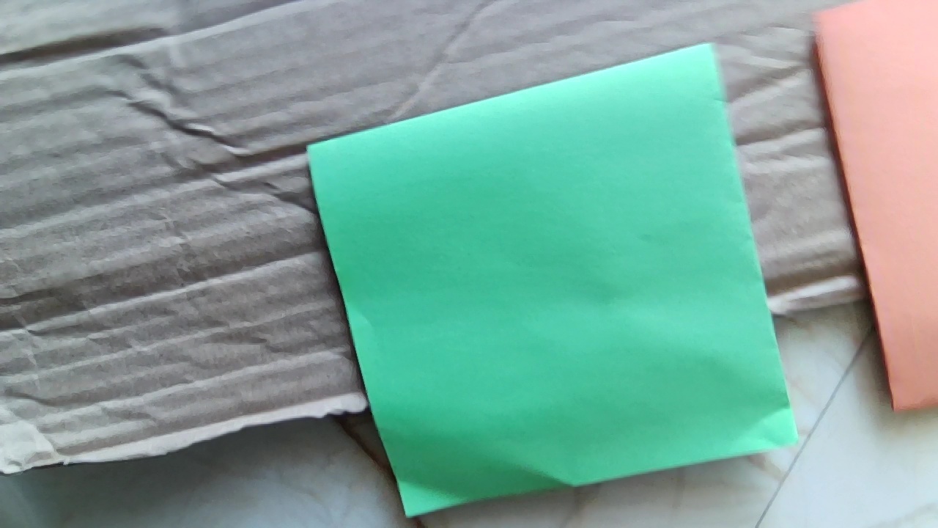
ComputerVision/Modules/imgs/178.jpg
