Blake-John/SchoolRobotMatch/ComputerVision/Modules/imgs/179.jpg

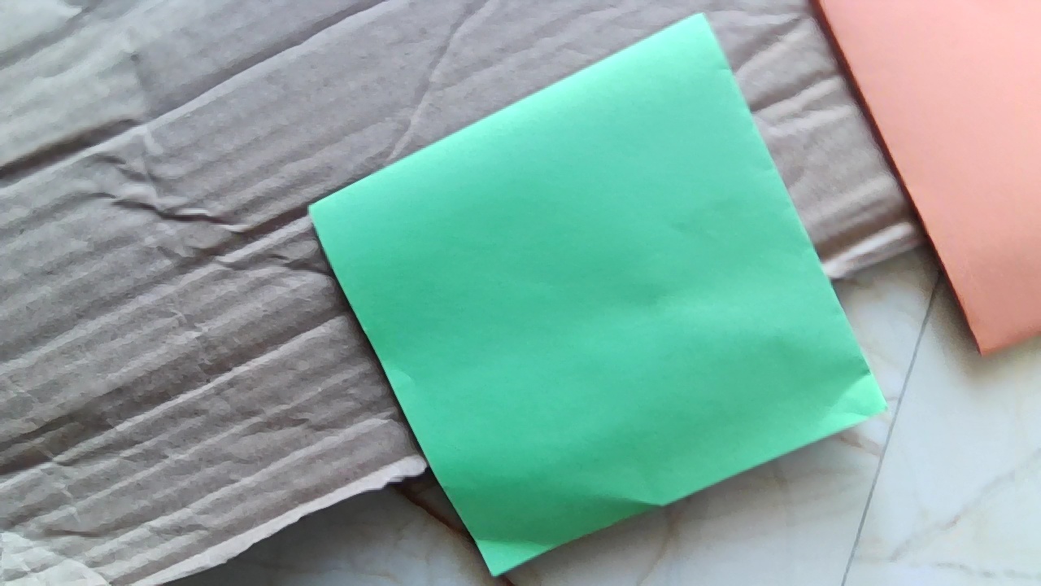
ComputerVision/Modules/imgs/179.jpg
