Blake-John/SchoolRobotMatch/ComputerVision/Modules/imgs/180.jpg

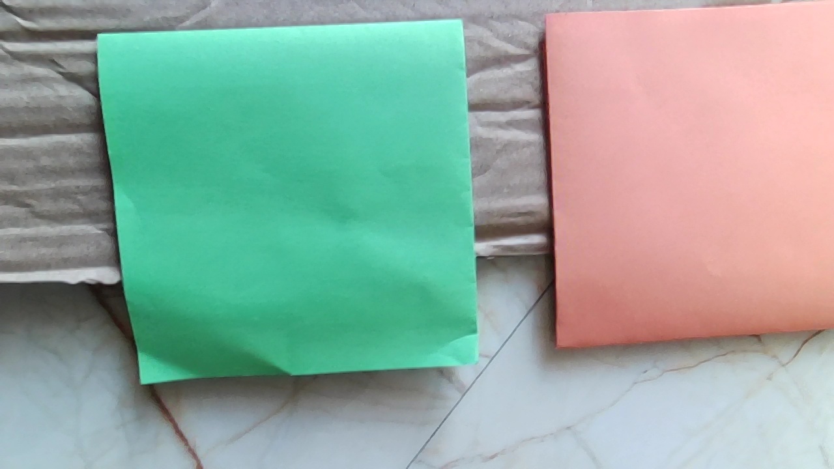
ComputerVision/Modules/imgs/180.jpg
