Blake-John/SchoolRobotMatch/ComputerVision/Modules/imgs/181.jpg

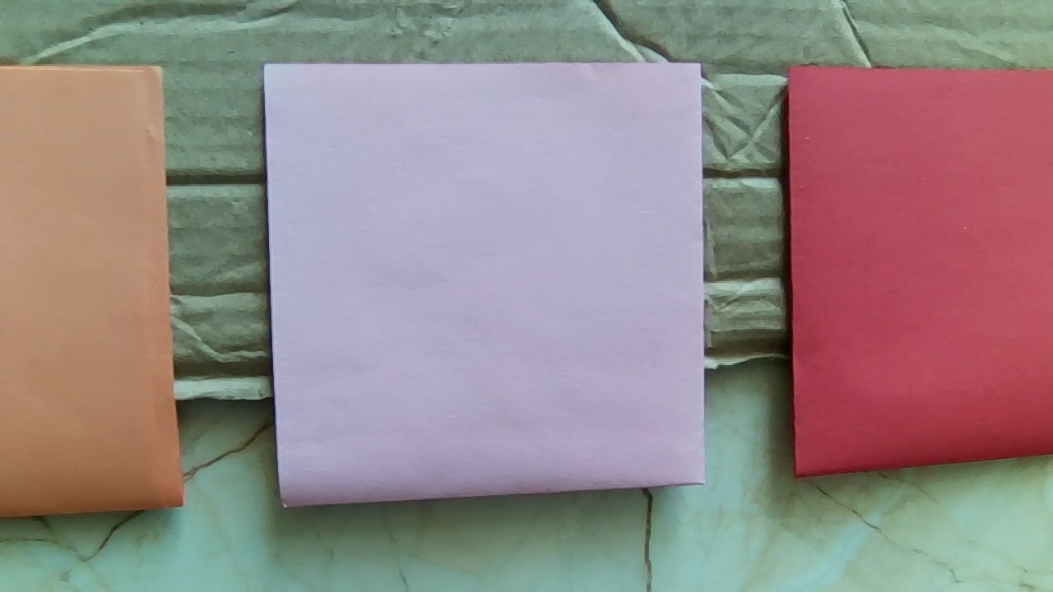
ComputerVision/Modules/imgs/181.jpg
