Blake-John/SchoolRobotMatch/ComputerVision/Modules/imgs/182.jpg

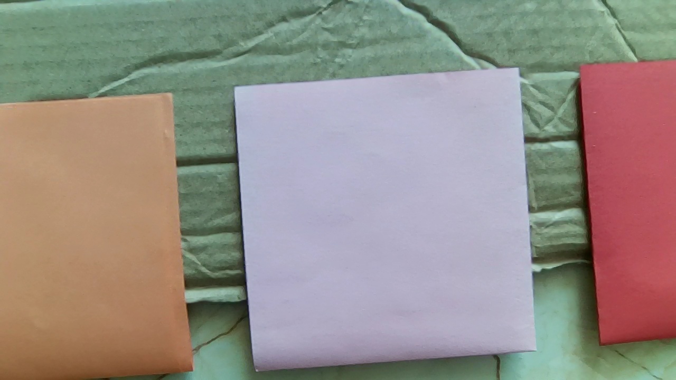
ComputerVision/Modules/imgs/182.jpg
