Blake-John/SchoolRobotMatch/ComputerVision/Modules/imgs/183.jpg

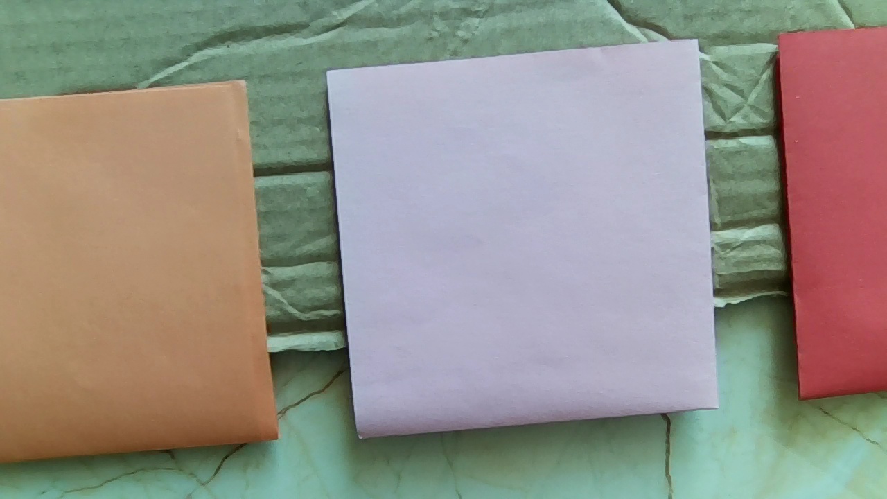
ComputerVision/Modules/imgs/183.jpg
