Blake-John/SchoolRobotMatch/ComputerVision/Modules/imgs/184.jpg

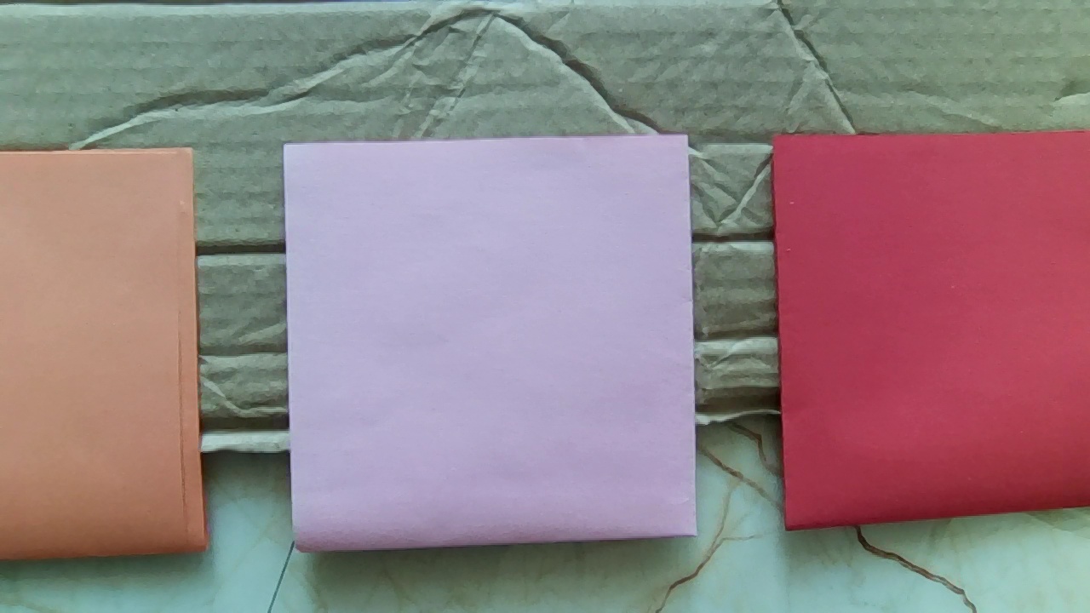
ComputerVision/Modules/imgs/184.jpg
