Blake-John/SchoolRobotMatch/ComputerVision/Modules/imgs/185.jpg

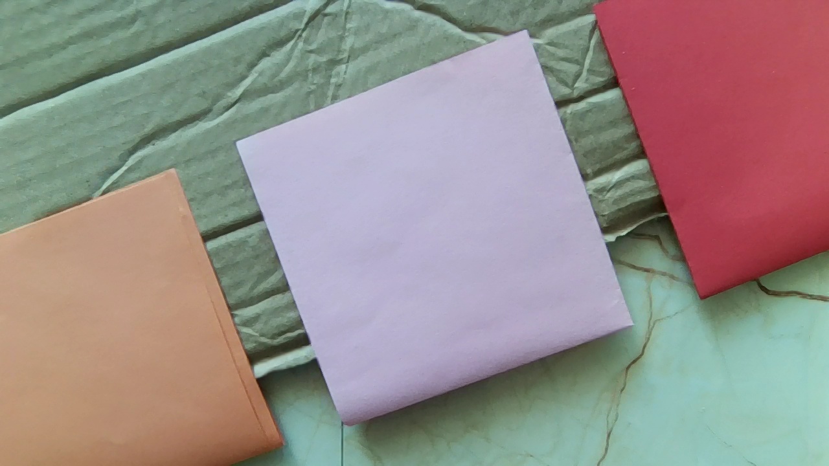
ComputerVision/Modules/imgs/185.jpg
