Blake-John/SchoolRobotMatch/ComputerVision/Modules/imgs/186.jpg

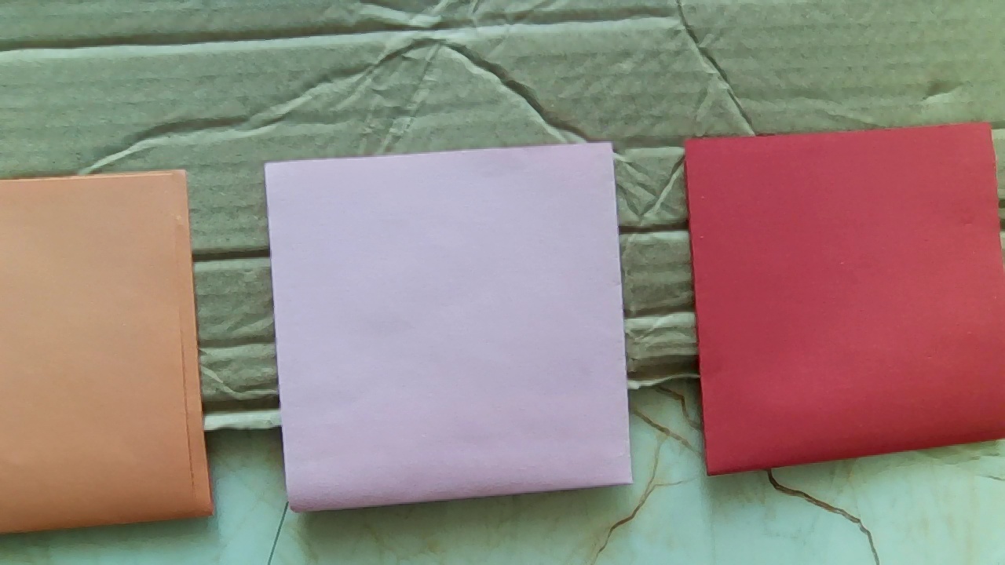
ComputerVision/Modules/imgs/186.jpg
