Blake-John/SchoolRobotMatch/ComputerVision/Modules/imgs/187.jpg

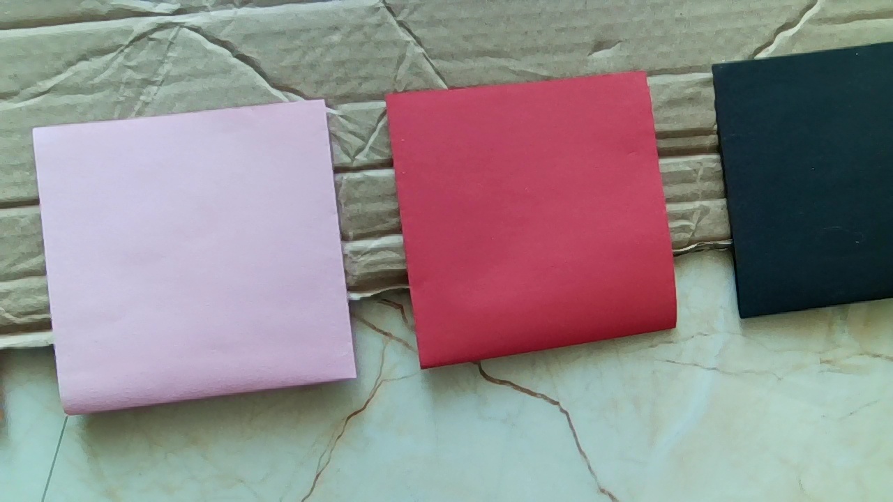
ComputerVision/Modules/imgs/187.jpg
