Blake-John/SchoolRobotMatch/ComputerVision/Modules/imgs/188.jpg

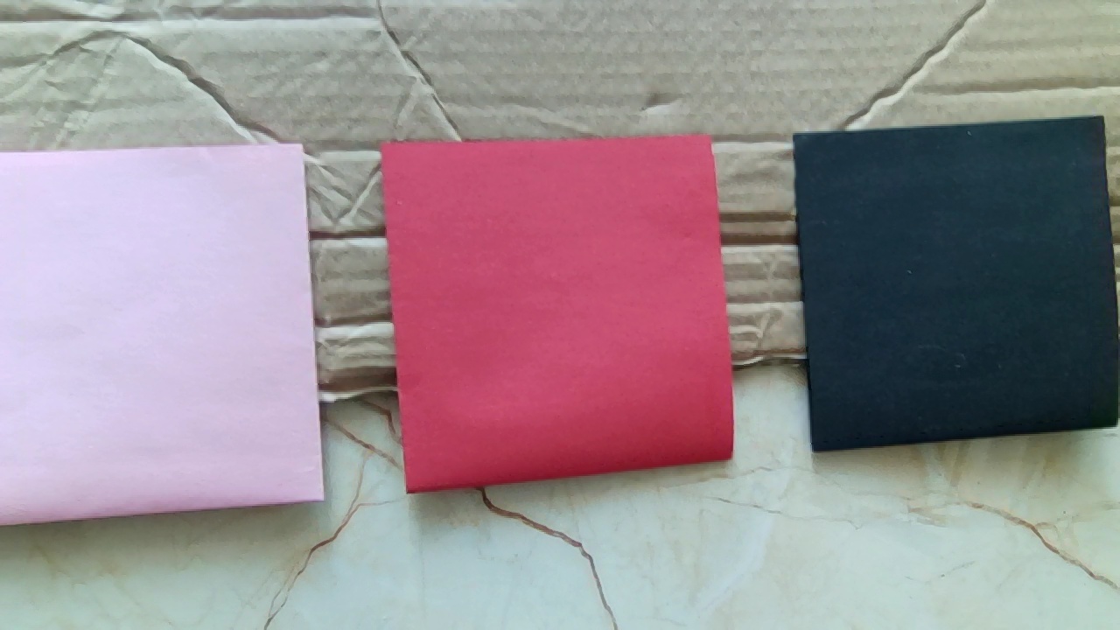
ComputerVision/Modules/imgs/188.jpg
