Blake-John/SchoolRobotMatch/ComputerVision/Modules/imgs/189.jpg

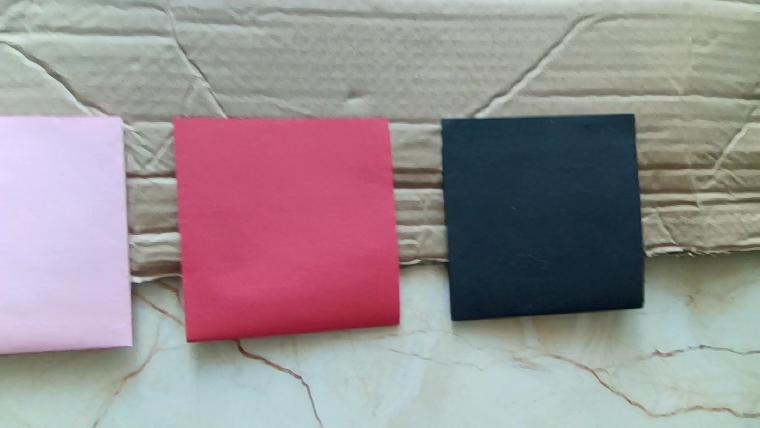
ComputerVision/Modules/imgs/189.jpg
