Blake-John/SchoolRobotMatch/ComputerVision/Modules/imgs/190.jpg

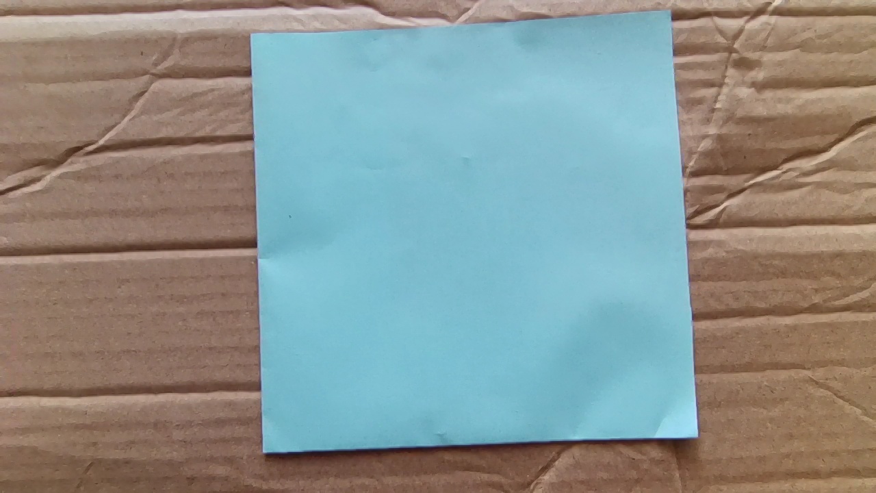
ComputerVision/Modules/imgs/190.jpg
