Blake-John/SchoolRobotMatch/ComputerVision/Modules/imgs/191.jpg

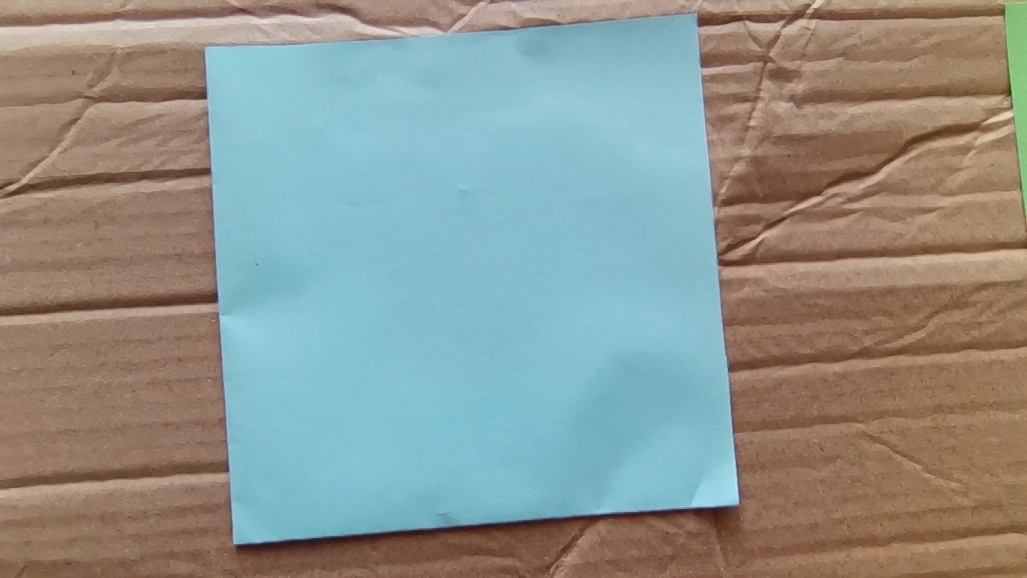
ComputerVision/Modules/imgs/191.jpg
