Blake-John/SchoolRobotMatch/ComputerVision/Modules/imgs/192.jpg

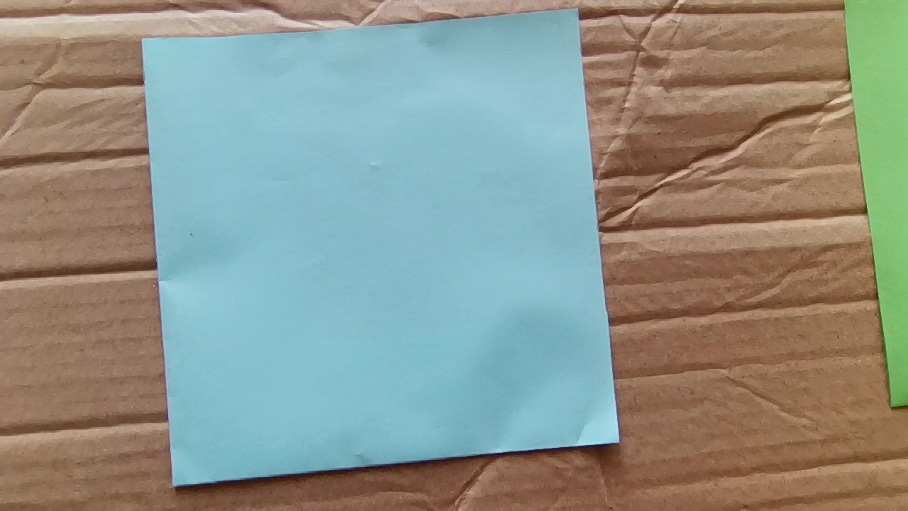
ComputerVision/Modules/imgs/192.jpg
