Blake-John/SchoolRobotMatch/ComputerVision/Modules/imgs/193.jpg

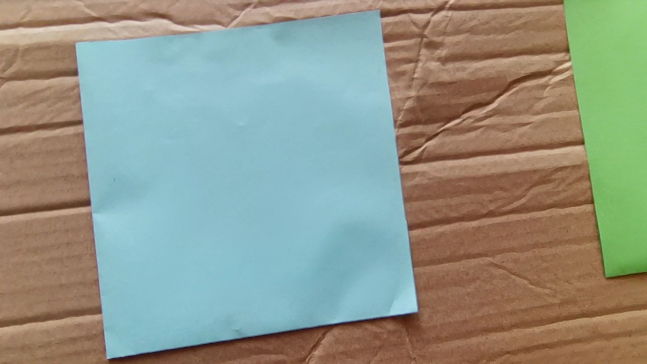
ComputerVision/Modules/imgs/193.jpg
