Blake-John/SchoolRobotMatch/ComputerVision/Modules/imgs/194.jpg

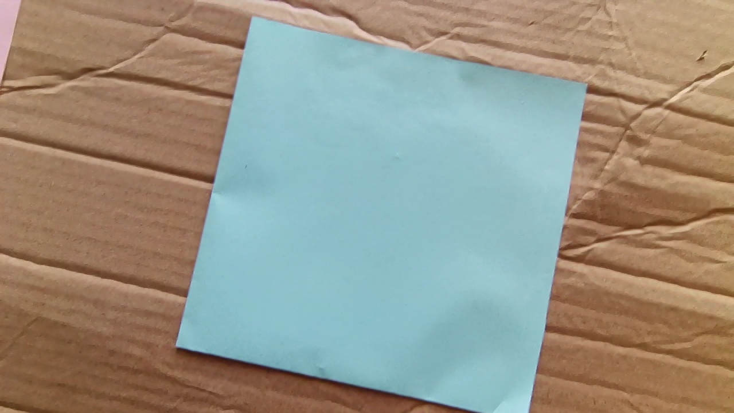
ComputerVision/Modules/imgs/194.jpg
