Blake-John/SchoolRobotMatch/ComputerVision/Modules/imgs/195.jpg

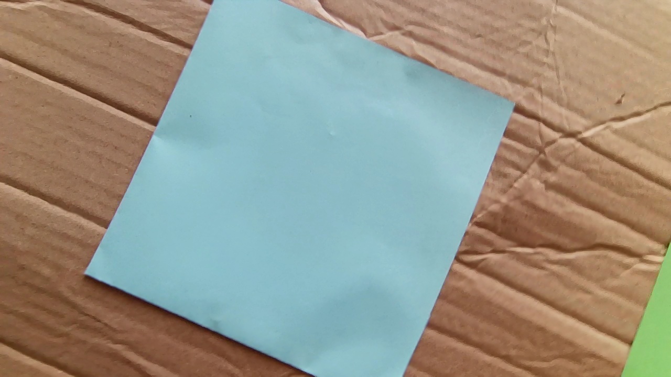
ComputerVision/Modules/imgs/195.jpg
