Blake-John/SchoolRobotMatch/ComputerVision/Modules/imgs/196.jpg

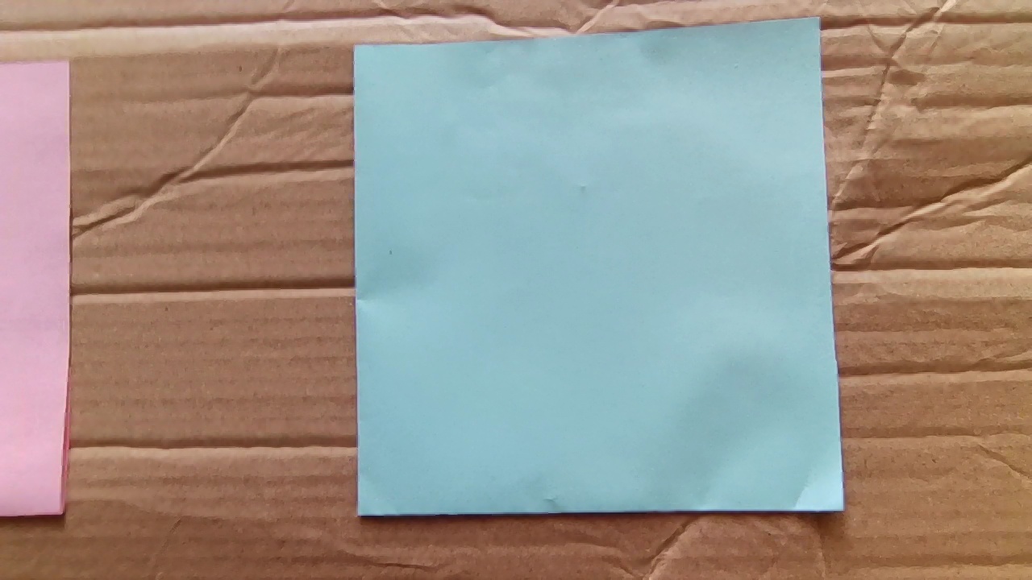
ComputerVision/Modules/imgs/196.jpg
