Blake-John/SchoolRobotMatch/ComputerVision/Modules/imgs/197.jpg

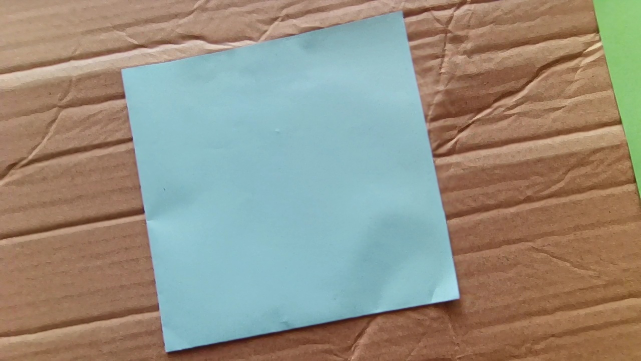
ComputerVision/Modules/imgs/197.jpg
