Blake-John/SchoolRobotMatch/ComputerVision/Modules/imgs/198.jpg

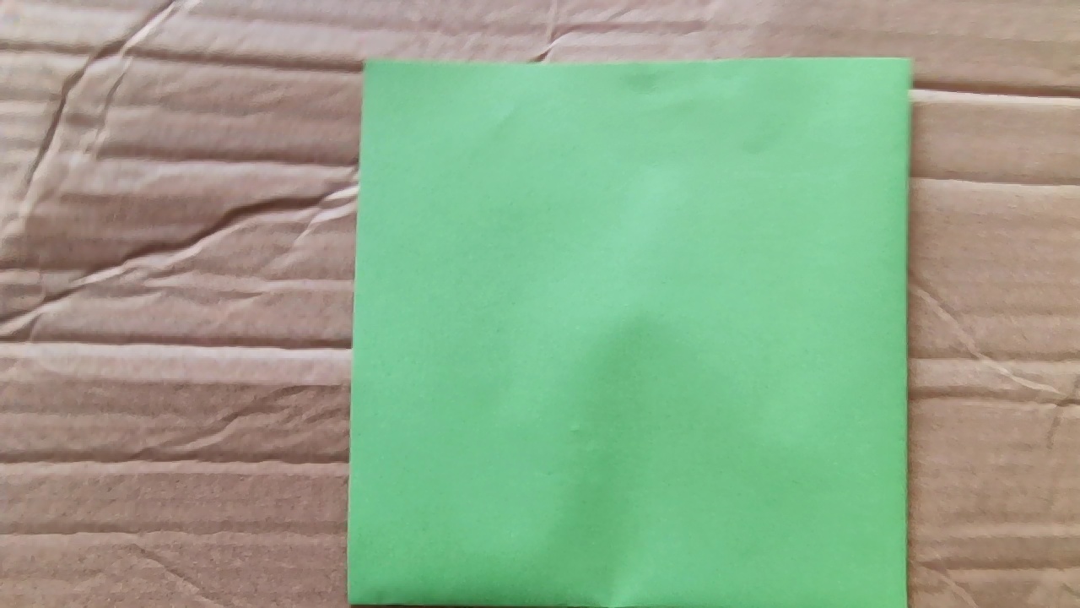
ComputerVision/Modules/imgs/198.jpg
