Blake-John/SchoolRobotMatch/ComputerVision/Modules/imgs/199.jpg

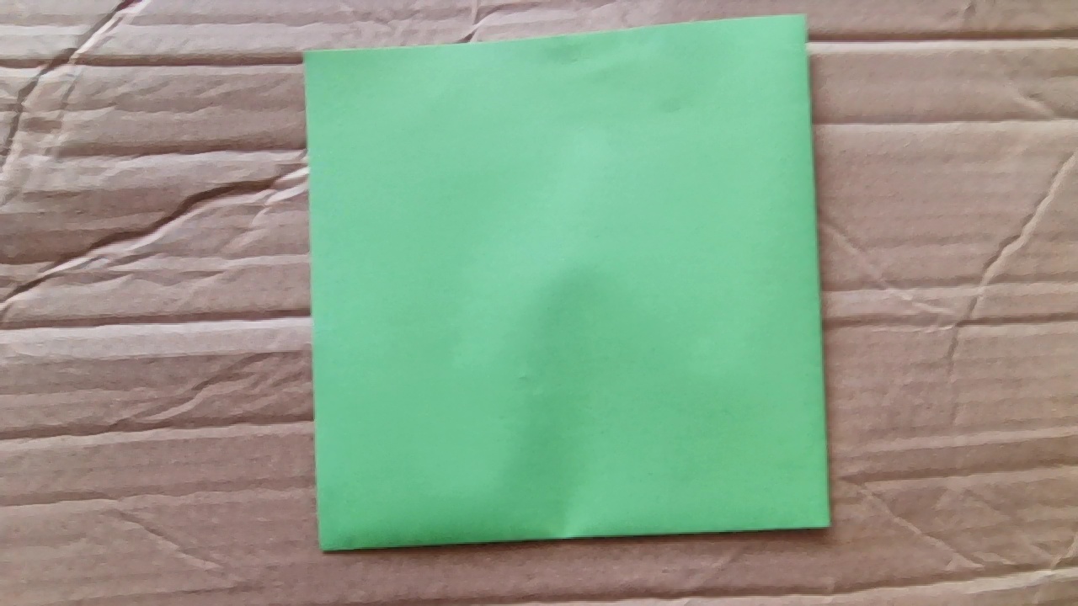
ComputerVision/Modules/imgs/199.jpg
