Blake-John/SchoolRobotMatch/ComputerVision/Modules/imgs/200.jpg

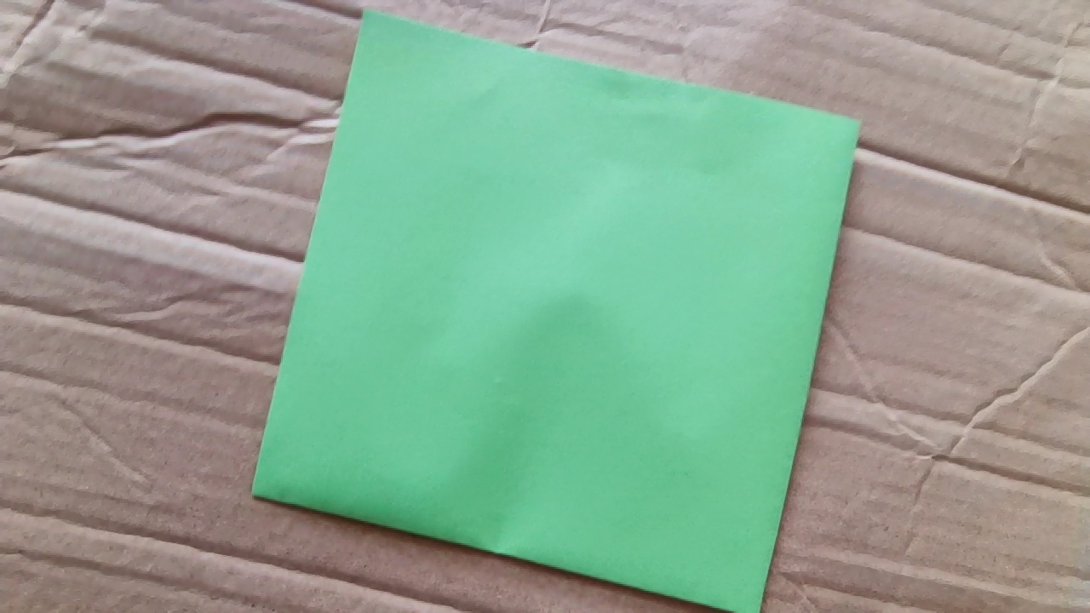
ComputerVision/Modules/imgs/200.jpg
