Blake-John/SchoolRobotMatch/ComputerVision/Modules/imgs/201.jpg

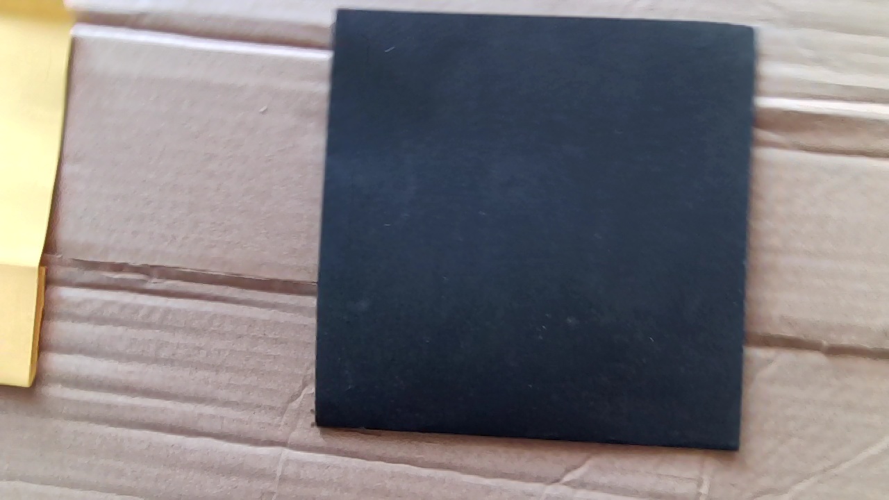
ComputerVision/Modules/imgs/201.jpg
