Blake-John/SchoolRobotMatch/ComputerVision/Modules/imgs/202.jpg

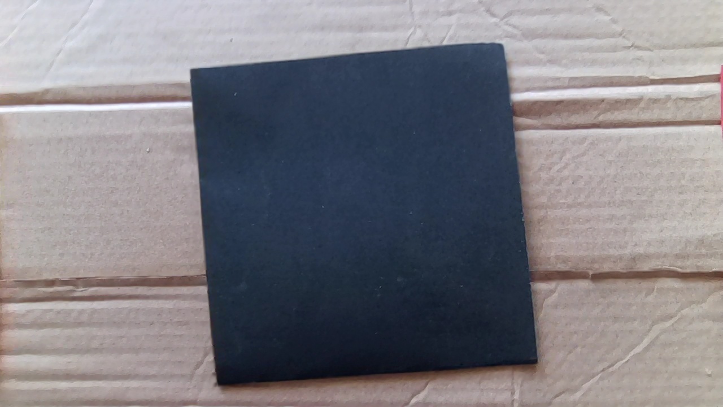
ComputerVision/Modules/imgs/202.jpg
