Blake-John/SchoolRobotMatch/ComputerVision/Modules/imgs/203.jpg

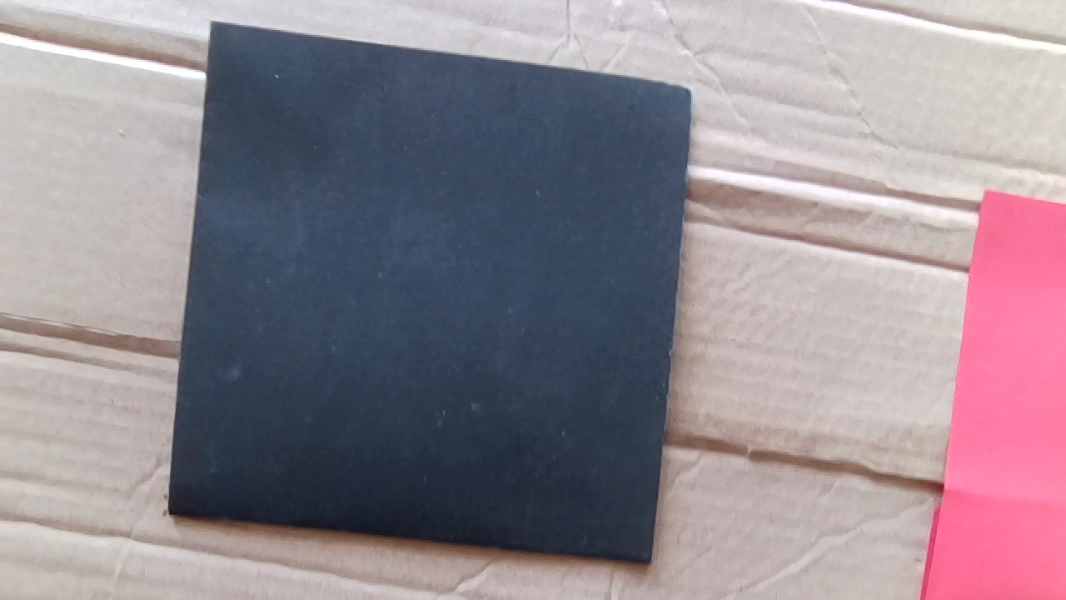
ComputerVision/Modules/imgs/203.jpg
