Blake-John/SchoolRobotMatch/ComputerVision/Modules/imgs/204.jpg

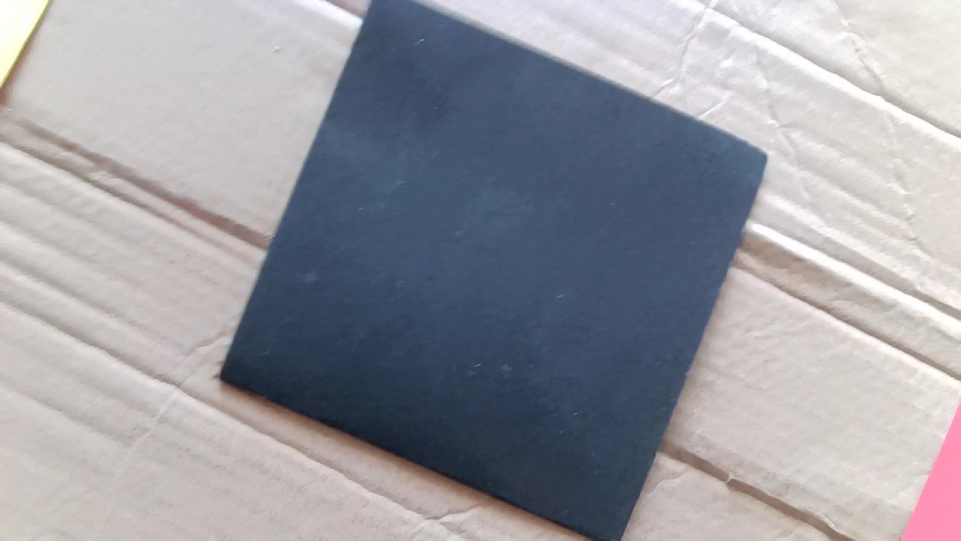
ComputerVision/Modules/imgs/204.jpg
