Blake-John/SchoolRobotMatch/ComputerVision/Modules/imgs/205.jpg

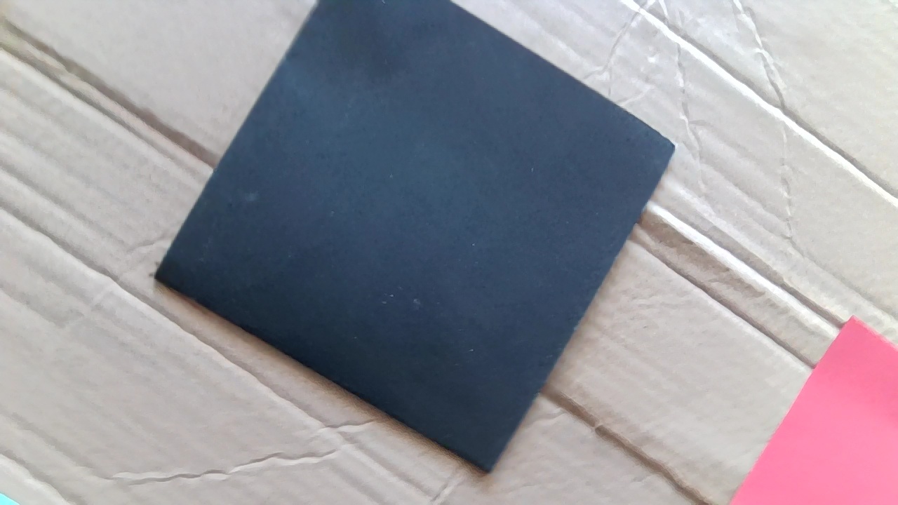
ComputerVision/Modules/imgs/205.jpg
