Blake-John/SchoolRobotMatch/ComputerVision/Modules/imgs/206.jpg

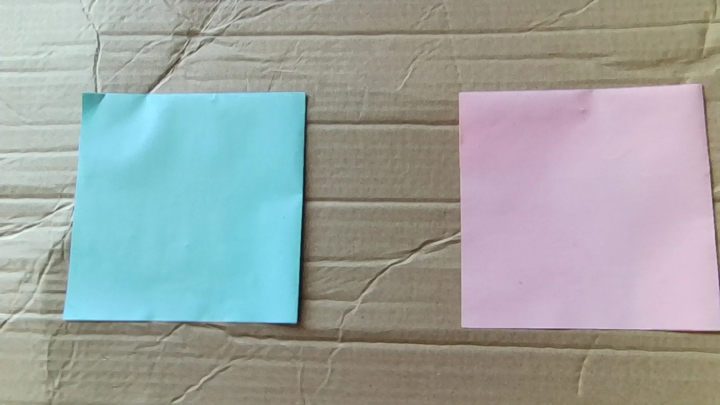
ComputerVision/Modules/imgs/206.jpg
