Blake-John/SchoolRobotMatch/ComputerVision/Modules/imgs/207.jpg

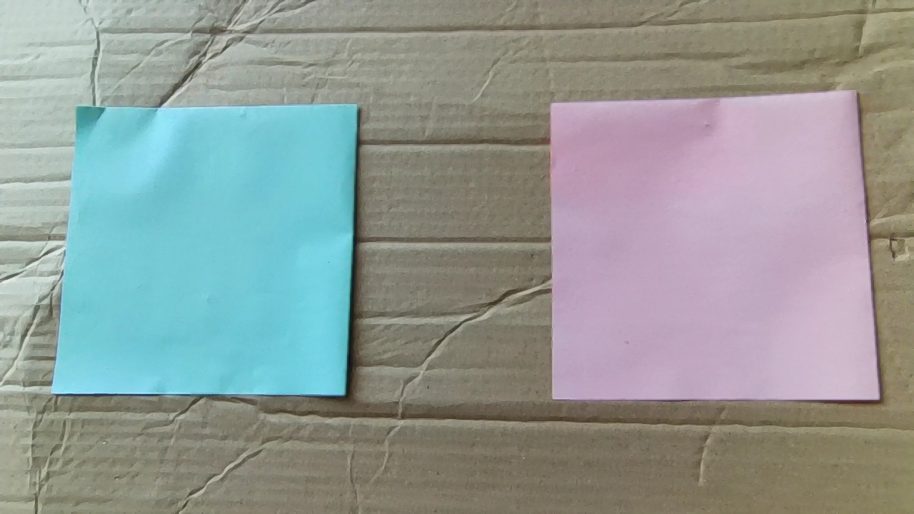
ComputerVision/Modules/imgs/207.jpg
