Blake-John/SchoolRobotMatch/ComputerVision/Modules/imgs/208.jpg

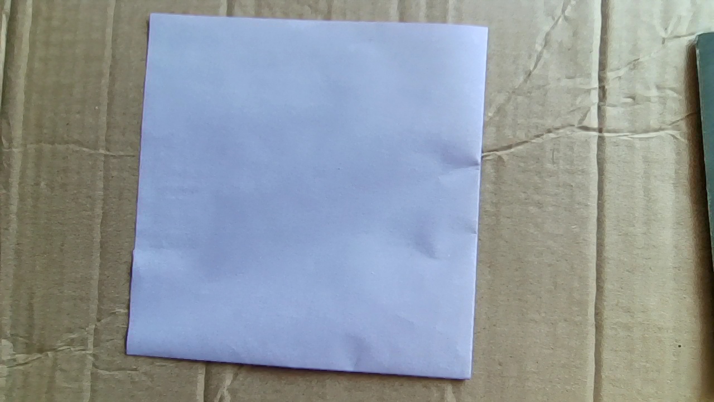
ComputerVision/Modules/imgs/208.jpg
