Blake-John/SchoolRobotMatch/ComputerVision/Modules/imgs/209.jpg

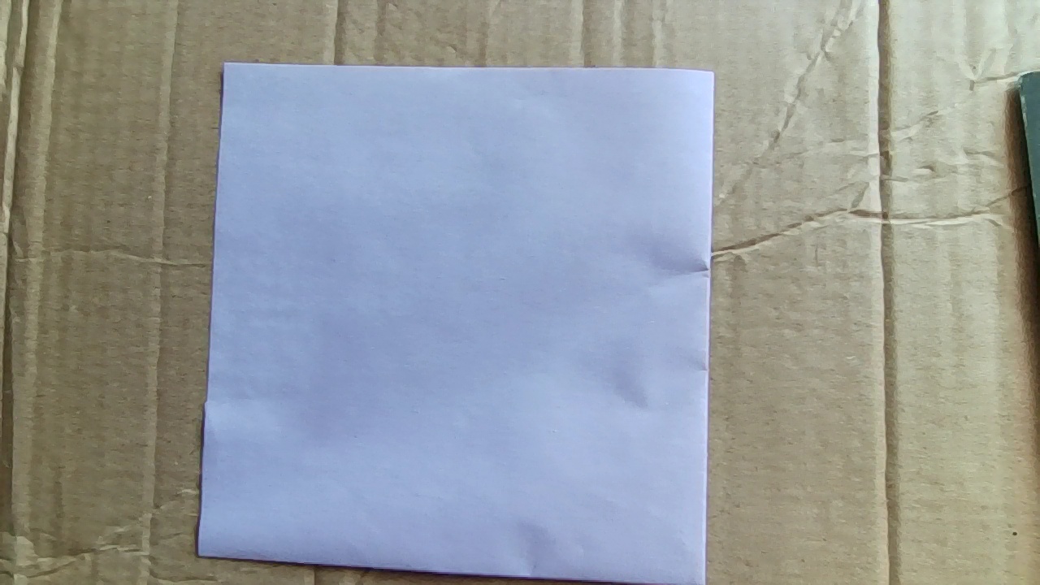
ComputerVision/Modules/imgs/209.jpg
