Blake-John/SchoolRobotMatch/ComputerVision/Modules/misc/V3/imgs/1.jpg

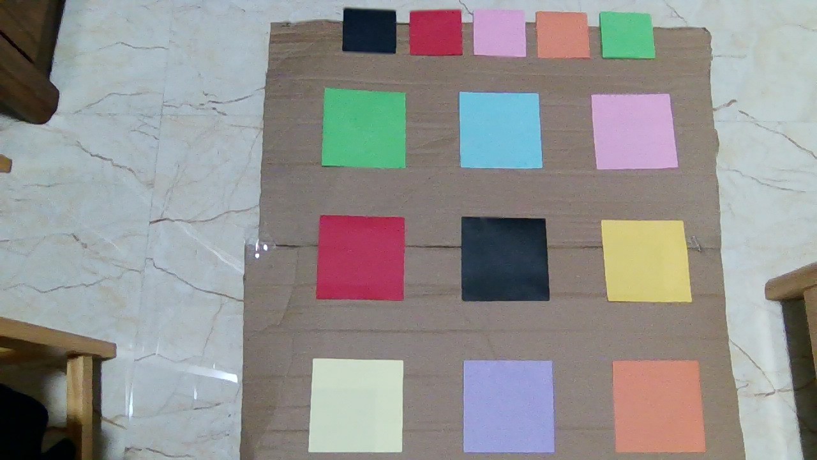
ComputerVision/Modules/misc/V3/imgs/1.jpg
