Blake-John/SchoolRobotMatch/ComputerVision/Modules/misc/V3/imgs/3.jpg

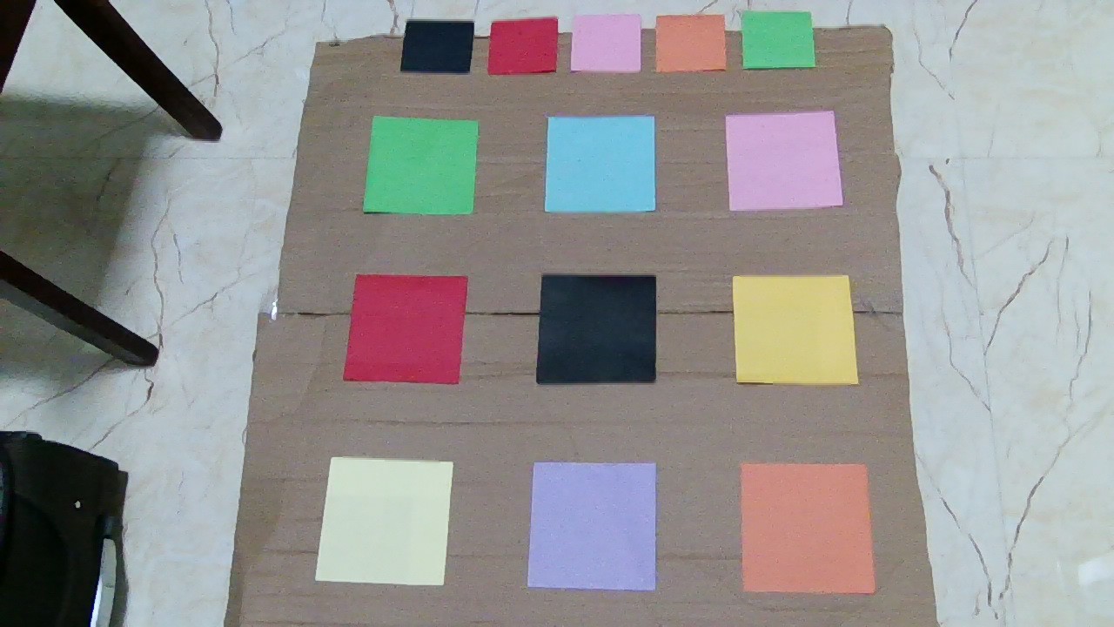
ComputerVision/Modules/misc/V3/imgs/3.jpg
