Blake-John/SchoolRobotMatch/ComputerVision/Modules/misc/V3/imgs/4.jpg

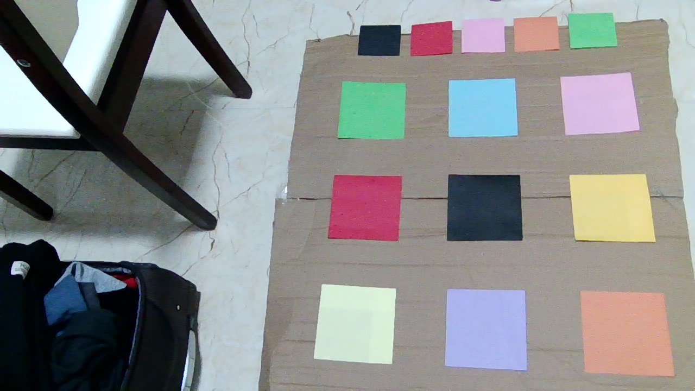
ComputerVision/Modules/misc/V3/imgs/4.jpg
