Blake-John/SchoolRobotMatch/ComputerVision/Modules/misc/V3/imgs/5.jpg

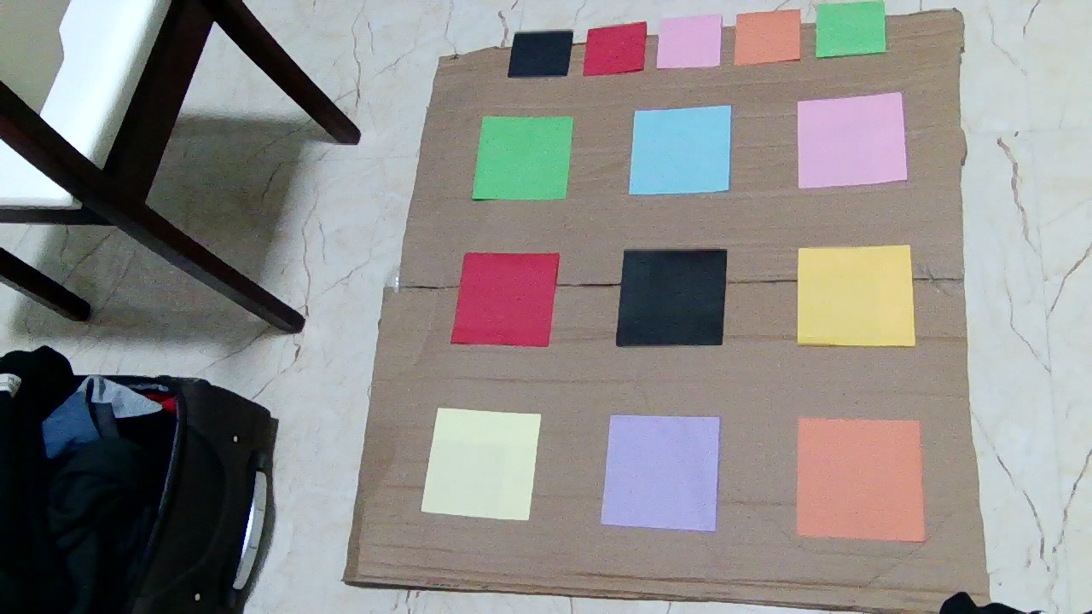
ComputerVision/Modules/misc/V3/imgs/5.jpg
