Blake-John/SchoolRobotMatch/ComputerVision/Modules/misc/V3/imgs/6.jpg

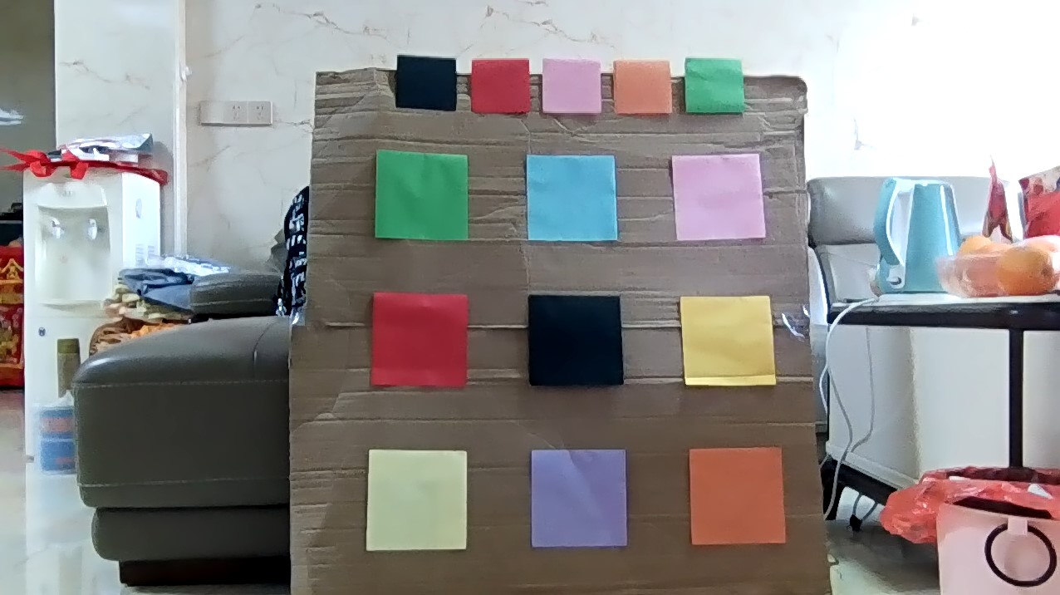
ComputerVision/Modules/misc/V3/imgs/6.jpg
