Blake-John/SchoolRobotMatch/ComputerVision/Modules/misc/V3/imgs/7.jpg

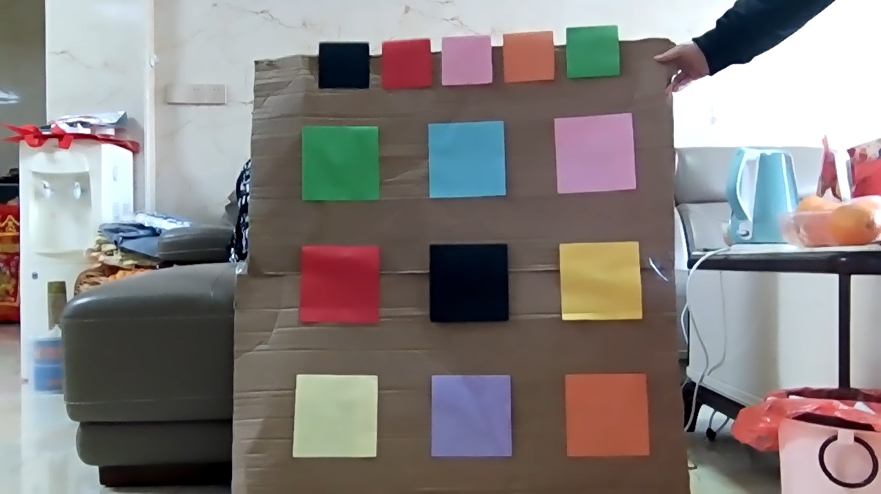
ComputerVision/Modules/misc/V3/imgs/7.jpg
