Blake-John/SchoolRobotMatch/ComputerVision/VisionSolutions/Solution1/medias/0.jpg

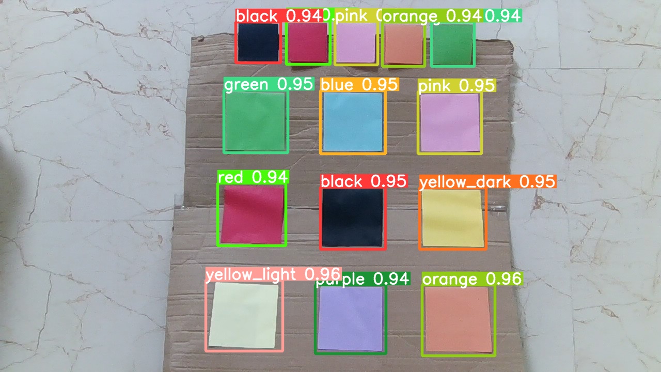
ComputerVision/VisionSolutions/Solution1/medias/0.jpg
