Blake-John/SchoolRobotMatch/ComputerVision/VisionSolutions/Solution2/imgs/3.jpg

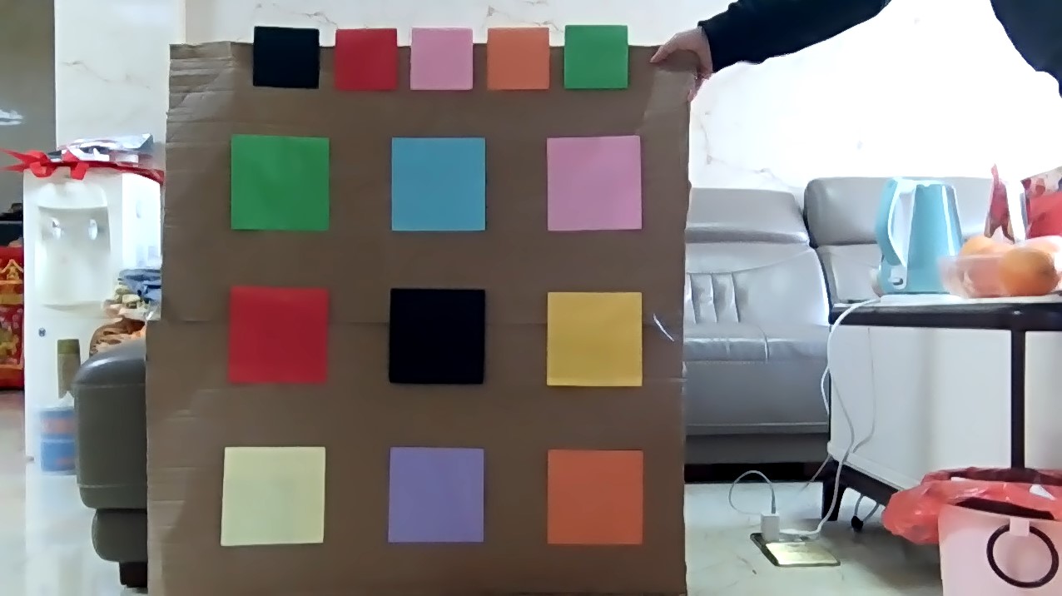
ComputerVision/VisionSolutions/Solution2/imgs/3.jpg
