Blake-John/SchoolRobotMatch/MechanicalStructure/装配体/整车装配.SLDASM

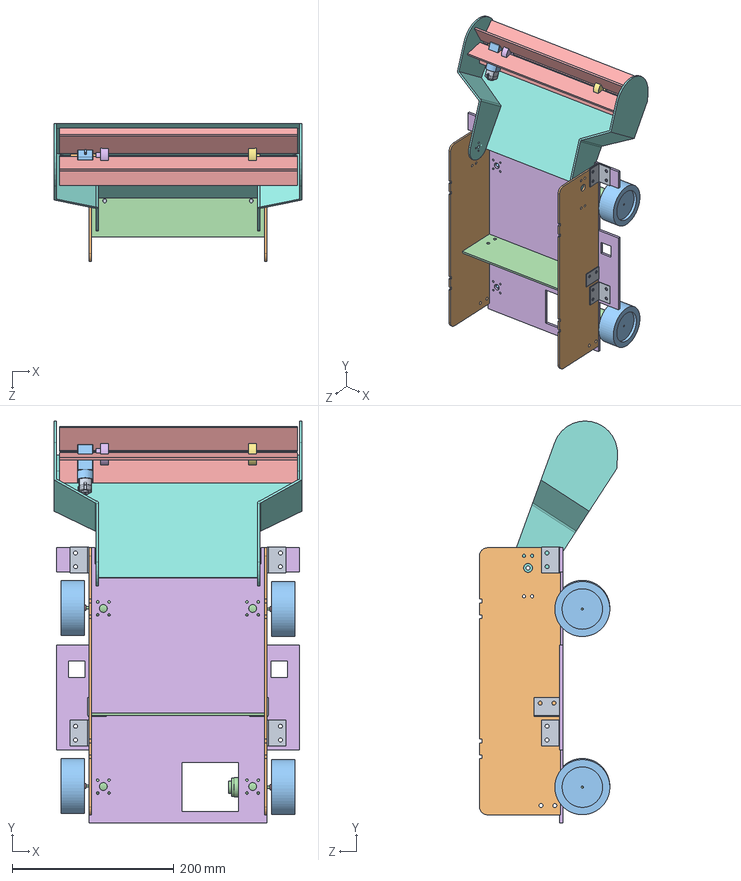
[picture p125: CAD file, 2024-02-24]
MechanicalStructure/装配体/整车装配.SLDASM
306.0 x 496.5 x 170.5 mm
底盘(未完善）
六角联轴器 x 4
编码电机 x 4
麦轮 x 4
侧板 x 2
角码 x 6
扫球轨道
（从）轴承_木板固定盘
（主）tt_木板固定盘
扫球木板 x 5
背板
Gearbox
output shaft
motor
