Blake-John/SchoolRobotMatch/MechanicalStructure/小车结构/cth/传送带.SLDASM

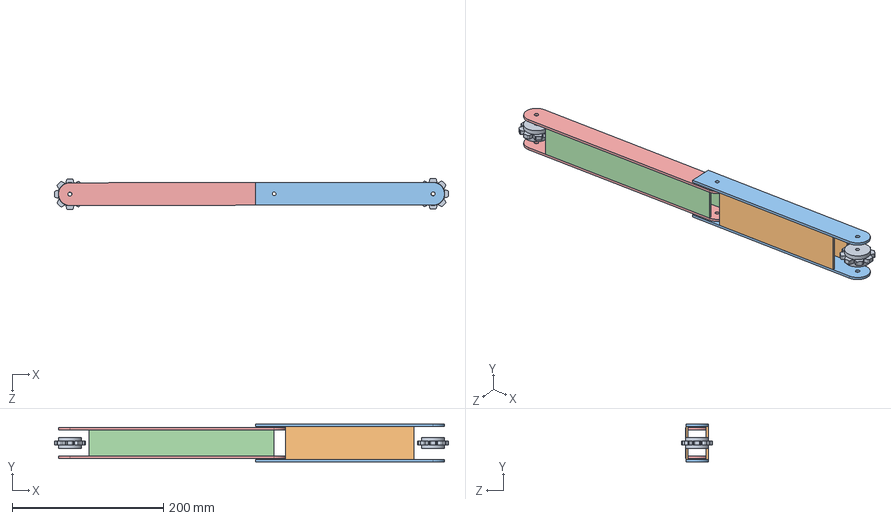
[picture p127: CAD file, 2024-04-27]
MechanicalStructure/小车结构/cth/传送带.SLDASM
520.7 x 50.0 x 41.1 mm
传送带1 x 2
传送带2 x 2
传送带3 x 2
传送带4 x 2
主动轮 x 2
