Blake-John/SchoolRobotMatch/MechanicalStructure/小车结构/整车装配2.SLDASM

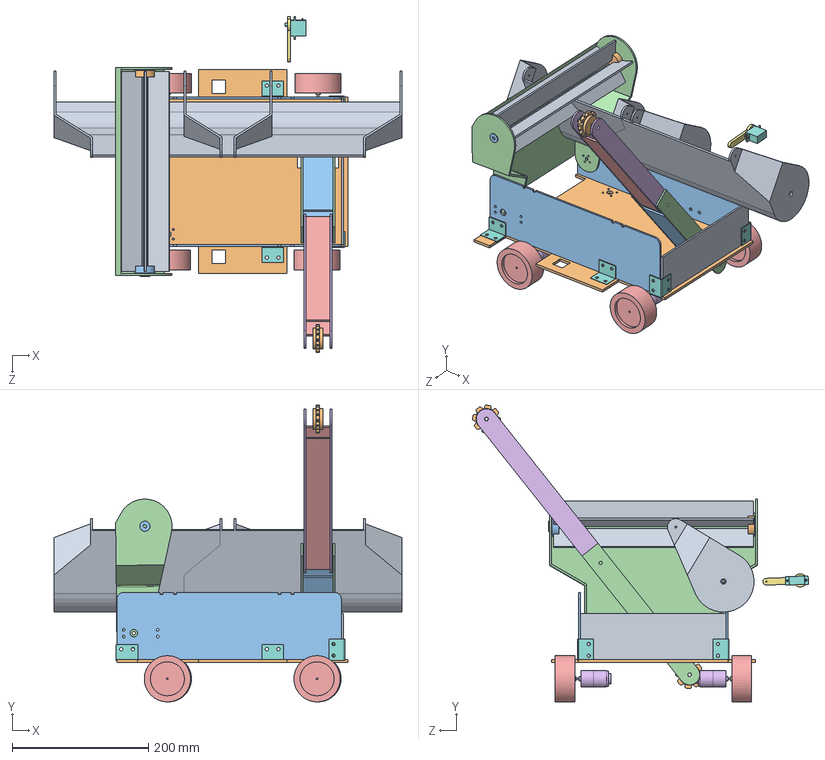
[picture p128: CAD file, 2024-04-27]
MechanicalStructure/小车结构/整车装配2.SLDASM
511.0 x 436.3 x 494.0 mm
侧板 x 2
底盘(未完善）
背板
角码 x 6
六角联轴器 x 4
编码电机 x 4
麦轮 x 4
扫球轨道
（主）tt_木板固定盘
（从）轴承_木板固定盘
扫球木板 x 5
舵机-SG90
活动杆
传送带1 x 2
传送带2 x 2
传送带3 x 2
传送带4 x 2
主动轮 x 2
导轨 x 2
