Blake-John/SchoolRobotMatch/MechanicalStructure/小车结构/996R舵机支架.step.SLDPRT

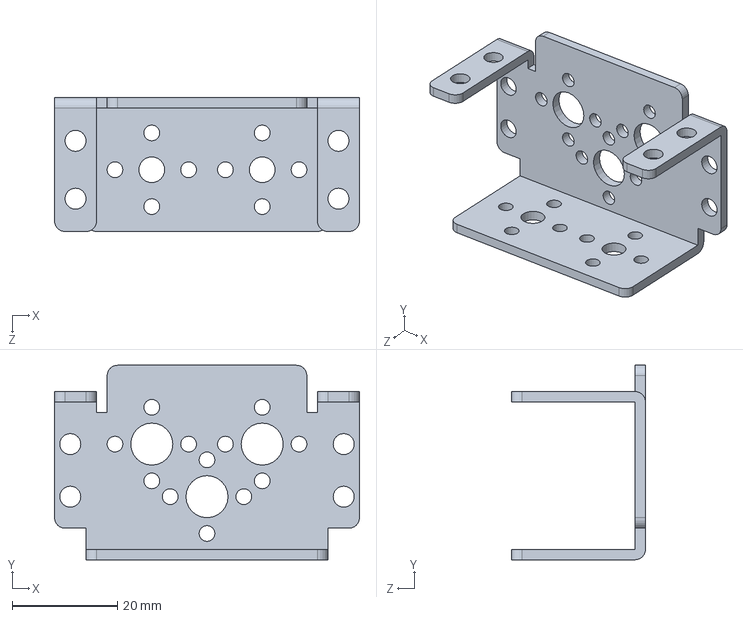
[picture p141: CAD file, 2024-04-27]
MechanicalStructure/小车结构/996R舵机支架.step.SLDPRT
58.0 x 37.0 x 25.5 mm
