Blake-John/SchoolRobotMatch/MechanicalStructure/小车结构/cth/主动轮.SLDPRT

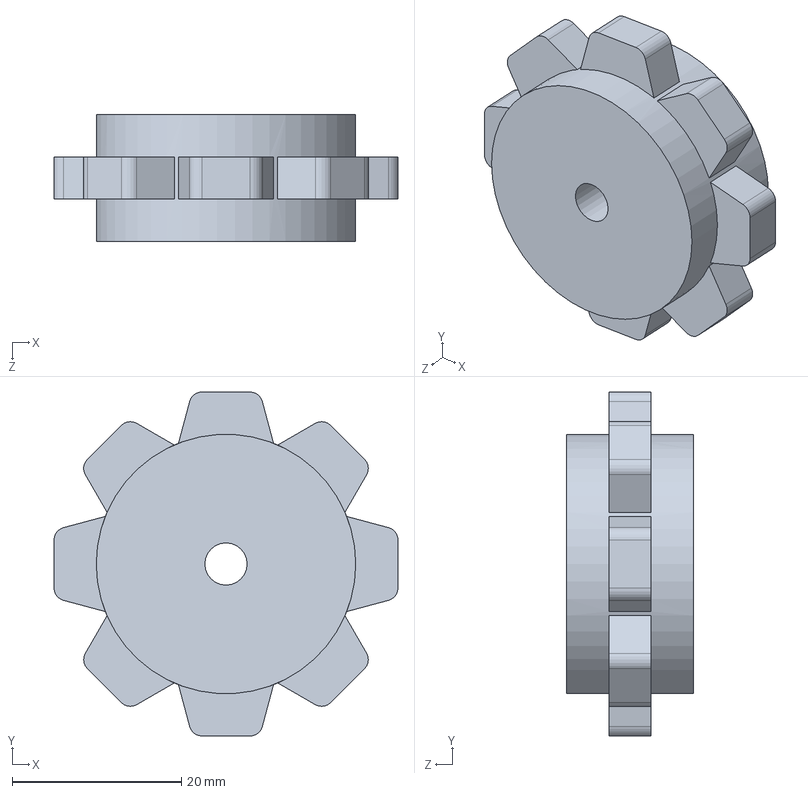
[picture p142: CAD file, 2024-04-27]
MechanicalStructure/小车结构/cth/主动轮.SLDPRT
40.7 x 40.7 x 15.0 mm
