Blake-John/SchoolRobotMatch/MechanicalStructure/小车结构/Mearm/右臂基部关节.SLDPRT

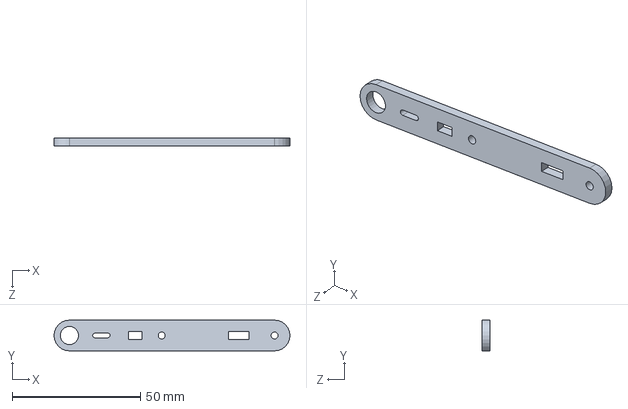
[picture p143: CAD file, 2024-04-27]
MechanicalStructure/小车结构/Mearm/右臂基部关节.SLDPRT
92.0 x 12.0 x 3.00 mm
