Blake-John/SchoolRobotMatch/MechanicalStructure/小车结构/tt130电机/Gearbox.SLDPRT

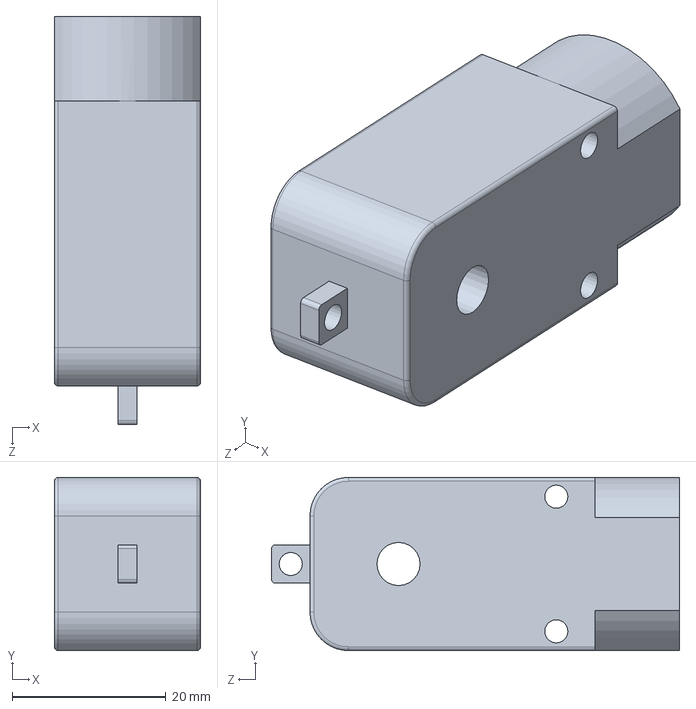
[picture p144: CAD file, 2024-02-24]
MechanicalStructure/小车结构/tt130电机/Gearbox.SLDPRT
19.0 x 22.5 x 53.0 mm
