Blake-John/SchoolRobotMatch/MechanicalStructure/小车结构/扫球装置/扫球轨道.SLDPRT

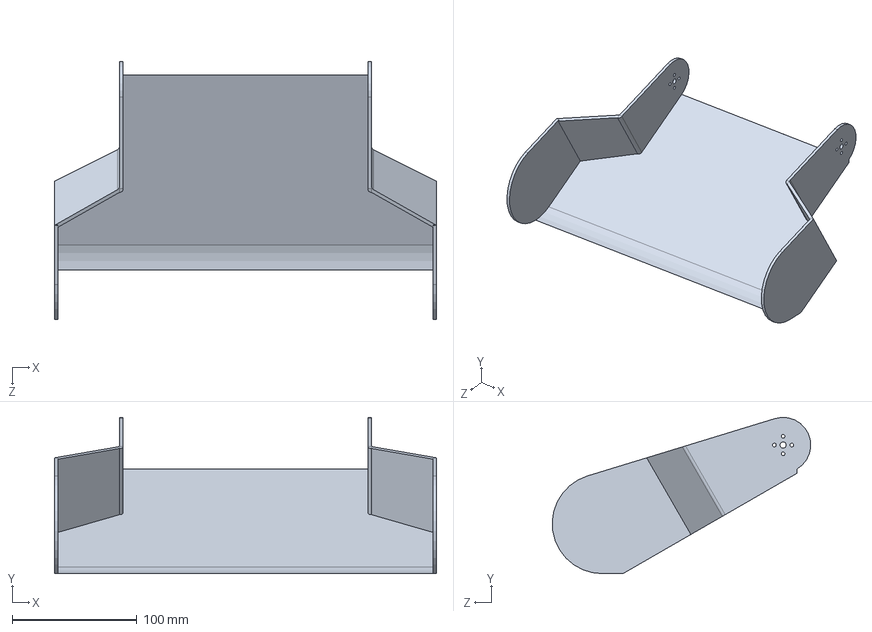
[picture p145: CAD file, 2024-04-27]
MechanicalStructure/小车结构/扫球装置/扫球轨道.SLDPRT
306.0 x 125.1 x 207.0 mm
