Blake-John/SchoolRobotMatch/MechanicalStructure/小车结构/麦轮整体/编码电机.SLDPRT

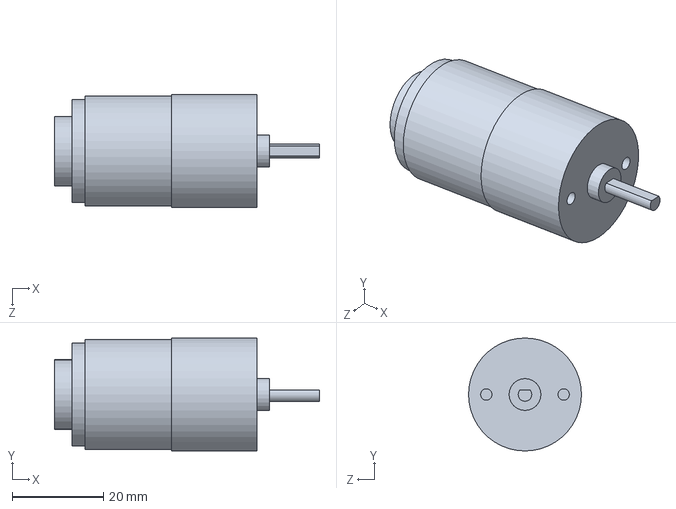
[picture p146: CAD file, 2024-02-24]
MechanicalStructure/小车结构/麦轮整体/编码电机.SLDPRT
58.2 x 24.8 x 24.8 mm
