Blake-John/SchoolRobotMatch/MechanicalStructure/小车结构/Mearm/臂间支撑架-上部.SLDPRT

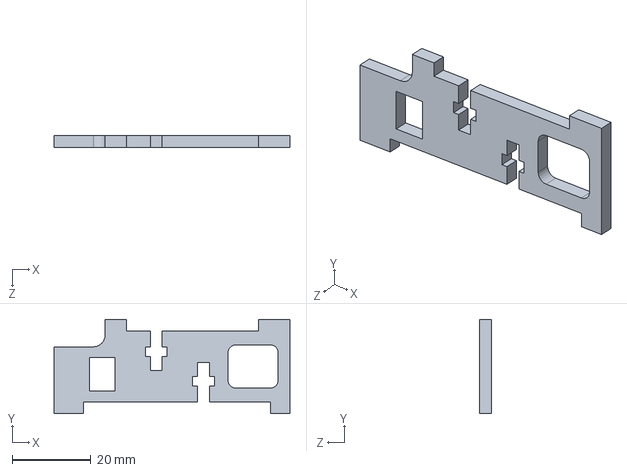
[picture p147: CAD file, 2024-04-27]
MechanicalStructure/小车结构/Mearm/臂间支撑架-上部.SLDPRT
60.0 x 24.0 x 3.00 mm
