Blake-John/SchoolRobotMatch/MechanicalStructure/小车结构/底盘(未完善）.SLDPRT

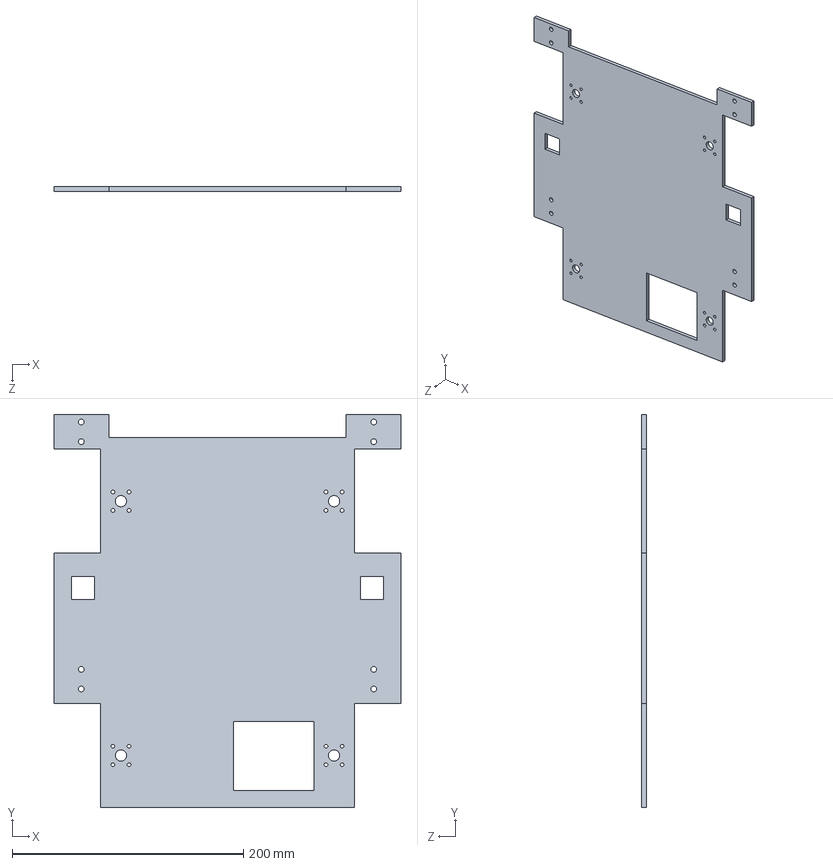
[picture p148: CAD file, 2024-04-27]
MechanicalStructure/小车结构/底盘(未完善）.SLDPRT
300.0 x 340.0 x 4.00 mm
