Blake-John/SchoolRobotMatch/MechanicalStructure/小车结构/扫球装置/导轨.SLDPRT

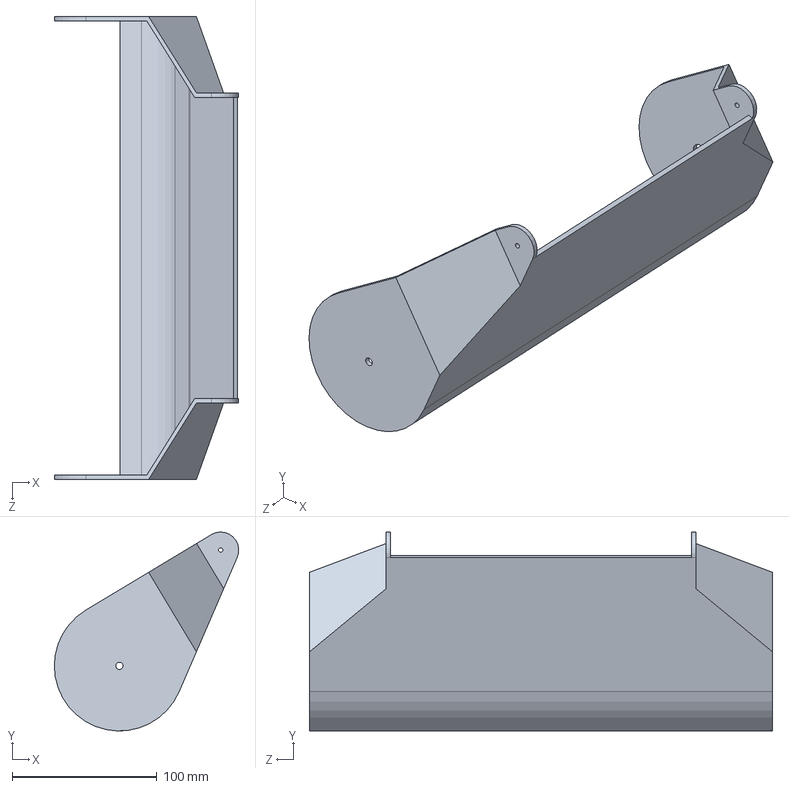
[picture p149: CAD file, 2024-04-27]
MechanicalStructure/小车结构/扫球装置/导轨.SLDPRT
127.4 x 137.5 x 320.0 mm
