Blake-John/SchoolRobotMatch/MechanicalStructure/小车结构/麦轮整体/六角联轴器.SLDPRT

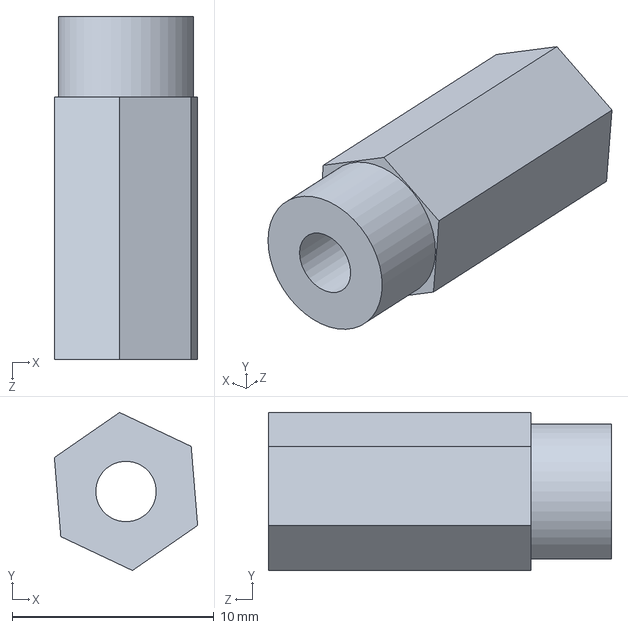
[picture p150: CAD file, 2024-02-06]
MechanicalStructure/小车结构/麦轮整体/六角联轴器.SLDPRT
7.10 x 7.83 x 17.0 mm
