Blake-John/SchoolRobotMatch/MechanicalStructure/小车结构/cth/导轨.SLDPRT

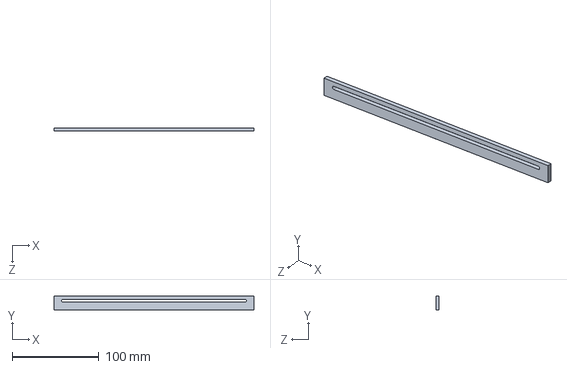
[picture p151: CAD file, 2024-04-27]
MechanicalStructure/小车结构/cth/导轨.SLDPRT
230.0 x 16.0 x 4.00 mm
