Blake-John/SchoolRobotMatch/MechanicalStructure/小车结构/Mearm/右臂舵机夹板.SLDPRT

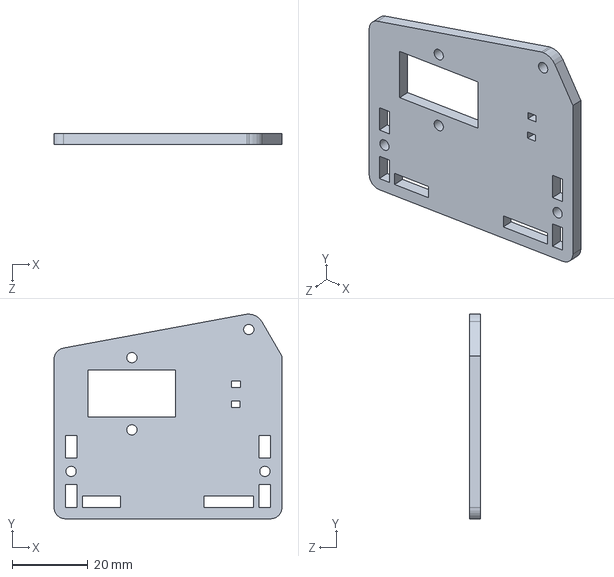
[picture p152: CAD file, 2024-04-27]
MechanicalStructure/小车结构/Mearm/右臂舵机夹板.SLDPRT
60.0 x 53.9 x 3.00 mm
