Blake-John/SchoolRobotMatch/MechanicalStructure/小车结构/Mearm/左臂舵机夹板.SLDPRT

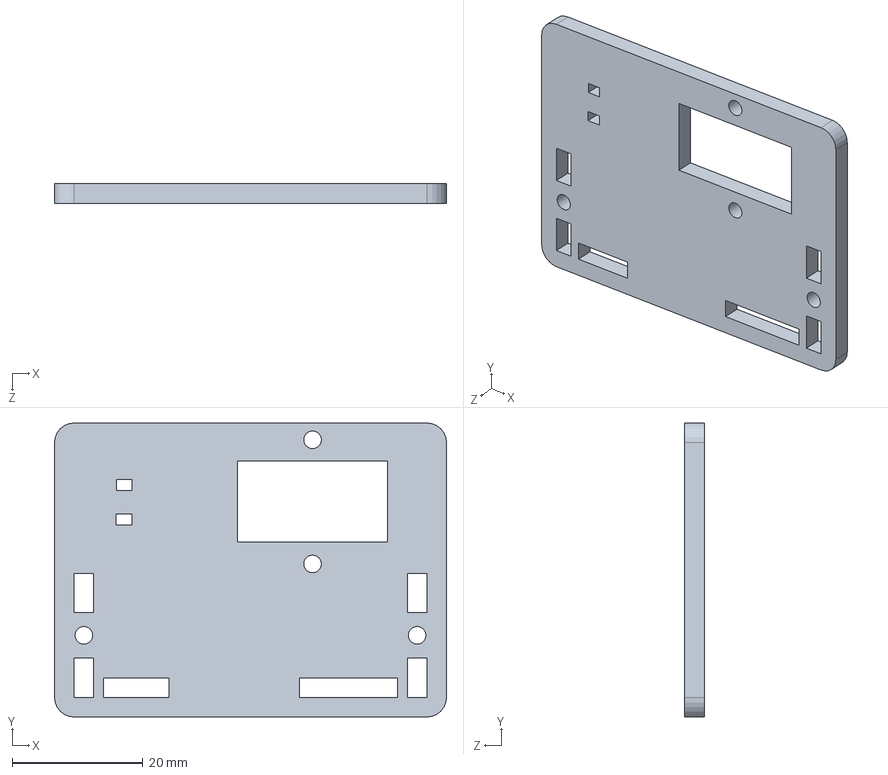
[picture p154: CAD file, 2024-04-27]
MechanicalStructure/小车结构/Mearm/左臂舵机夹板.SLDPRT
60.0 x 45.0 x 3.00 mm
