Blake-John/SchoolRobotMatch/MechanicalStructure/小车结构/扫球装置/（从）轴承_木板固定盘.SLDPRT

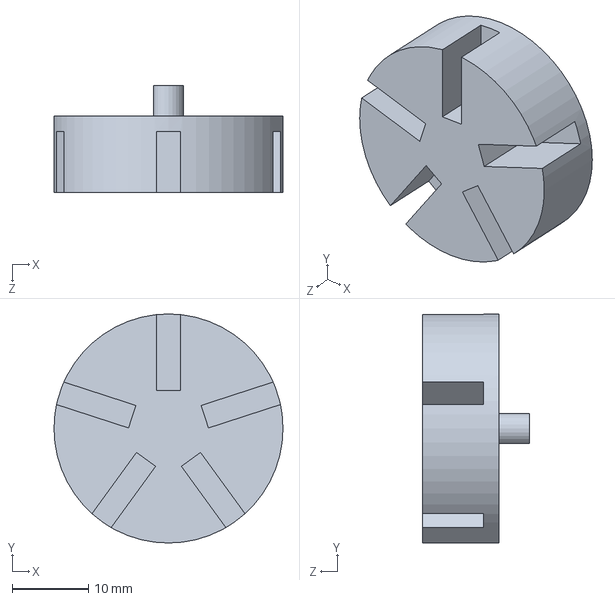
[picture p155: CAD file, 2024-02-24]
MechanicalStructure/小车结构/扫球装置/（从）轴承_木板固定盘.SLDPRT
30.0 x 30.0 x 14.0 mm
