Blake-John/SchoolRobotMatch/MechanicalStructure/小车结构/cth/活动杆.SLDPRT

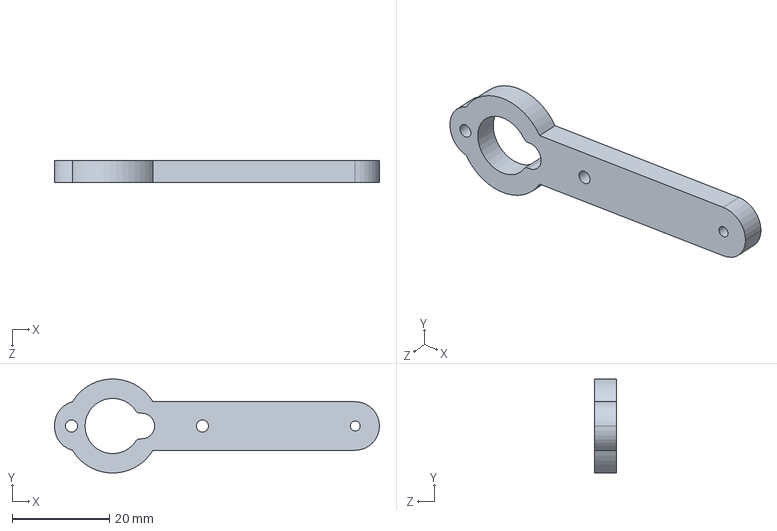
[picture p156: CAD file, 2024-04-27]
MechanicalStructure/小车结构/cth/活动杆.SLDPRT
67.0 x 19.4 x 4.50 mm
