Blake-John/SchoolRobotMatch/MechanicalStructure/小车结构/Mearm/M3×6内六角螺钉.SLDPRT

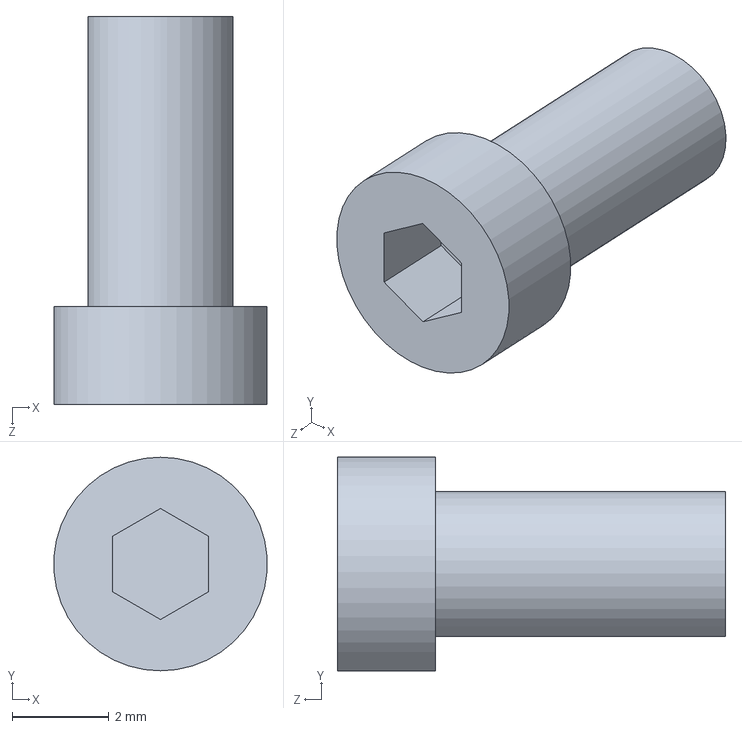
[picture p157: CAD file, 2024-04-27]
MechanicalStructure/小车结构/Mearm/M3×6内六角螺钉.SLDPRT
4.40 x 4.42 x 8.03 mm
