Blake-John/SchoolRobotMatch/MechanicalStructure/小车结构/扫球装置/（主）tt_木板固定盘.SLDPRT

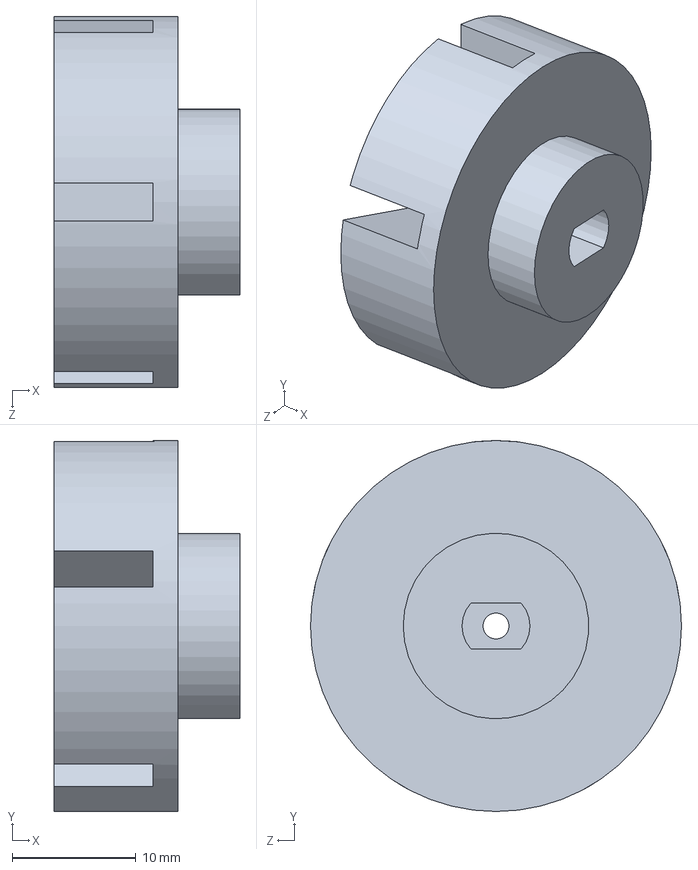
[picture p158: CAD file, 2024-02-24]
MechanicalStructure/小车结构/扫球装置/（主）tt_木板固定盘.SLDPRT
15.0 x 30.0 x 30.0 mm
