Blake-John/SchoolRobotMatch/MechanicalStructure/小车结构/角码.SLDPRT

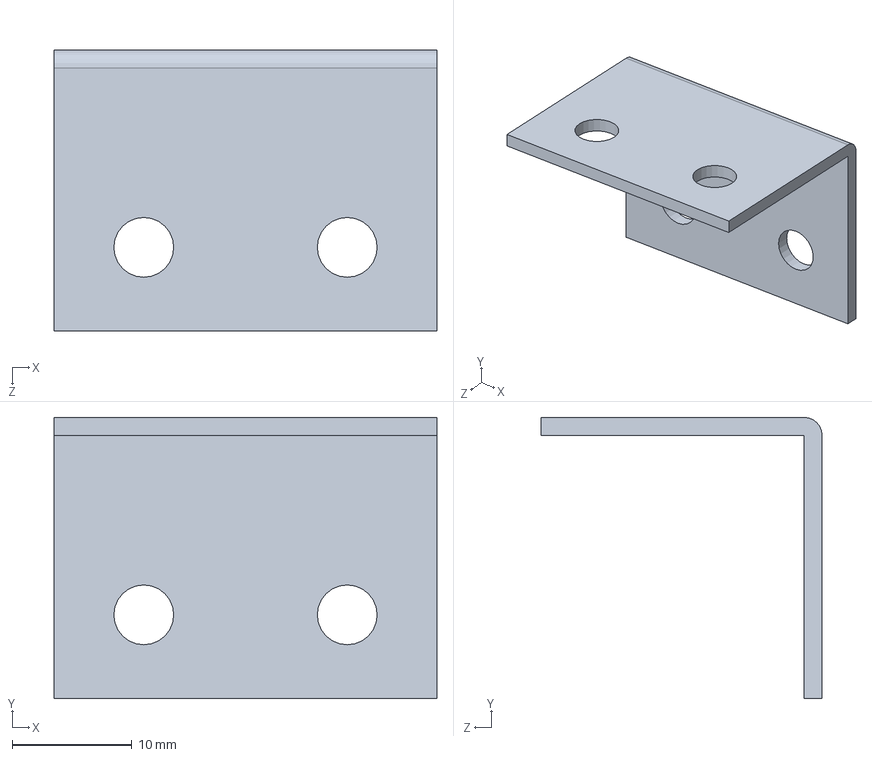
[picture p159: CAD file, 2024-04-27]
MechanicalStructure/小车结构/角码.SLDPRT
32.0 x 23.5 x 23.5 mm
