Blake-John/SchoolRobotMatch/MechanicalStructure/小车结构/cth/舵机-SG90.SLDPRT

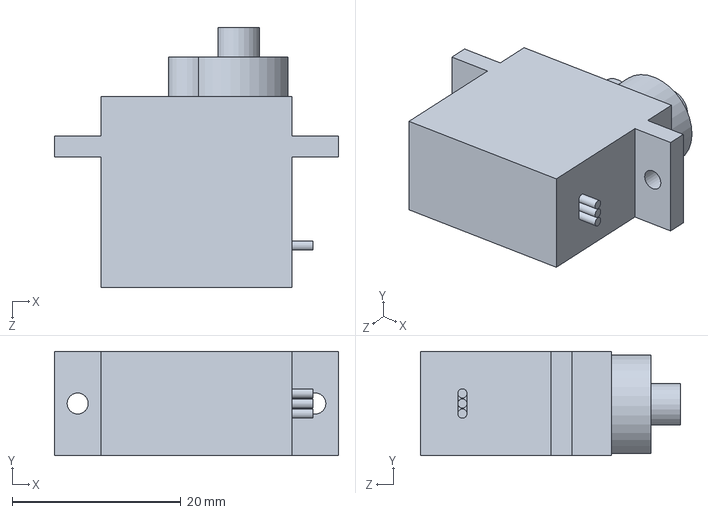
[picture p160: CAD file, 2024-04-27]
MechanicalStructure/小车结构/cth/舵机-SG90.SLDPRT
33.7 x 12.4 x 30.9 mm
