Blake-John/SchoolRobotMatch/MechanicalStructure/小车结构/Mearm/舵机鞍座(上).SLDPRT

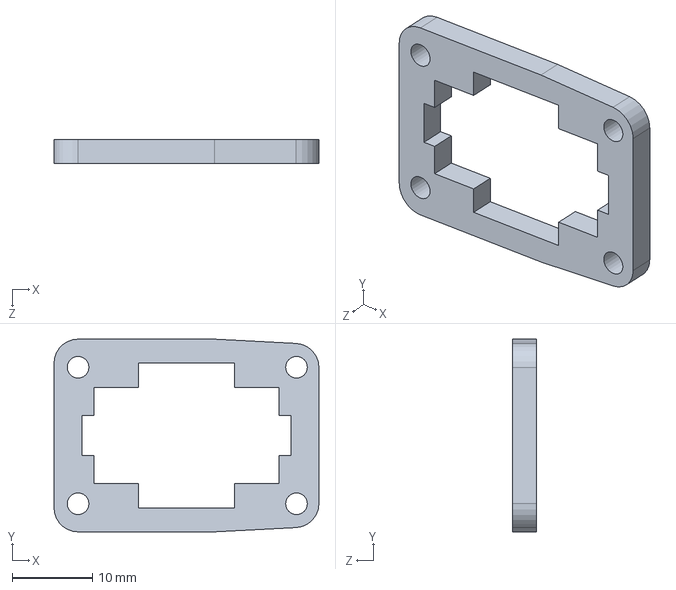
[picture p161: CAD file, 2024-04-27]
MechanicalStructure/小车结构/Mearm/舵机鞍座(上).SLDPRT
33.0 x 24.0 x 3.00 mm
