Blake-John/SchoolRobotMatch/MechanicalStructure/小车结构/舵机.STEP

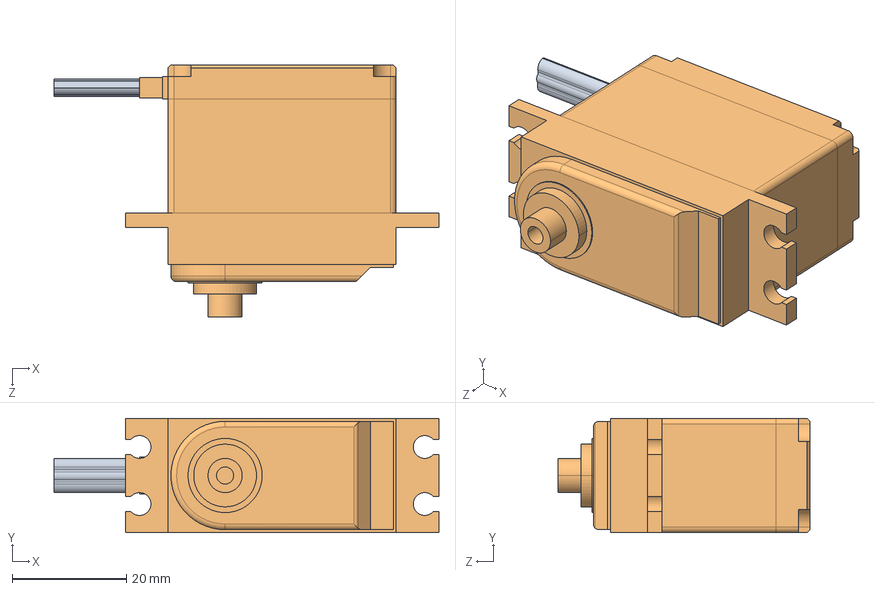
[picture p162: CAD file, 2024-04-27]
MechanicalStructure/小车结构/舵机.STEP
67.5 x 20.0 x 44.2 mm
