Blake-John/SchoolRobotMatch/MechanicalStructure/小车结构/cth/铲斗.SLDPRT

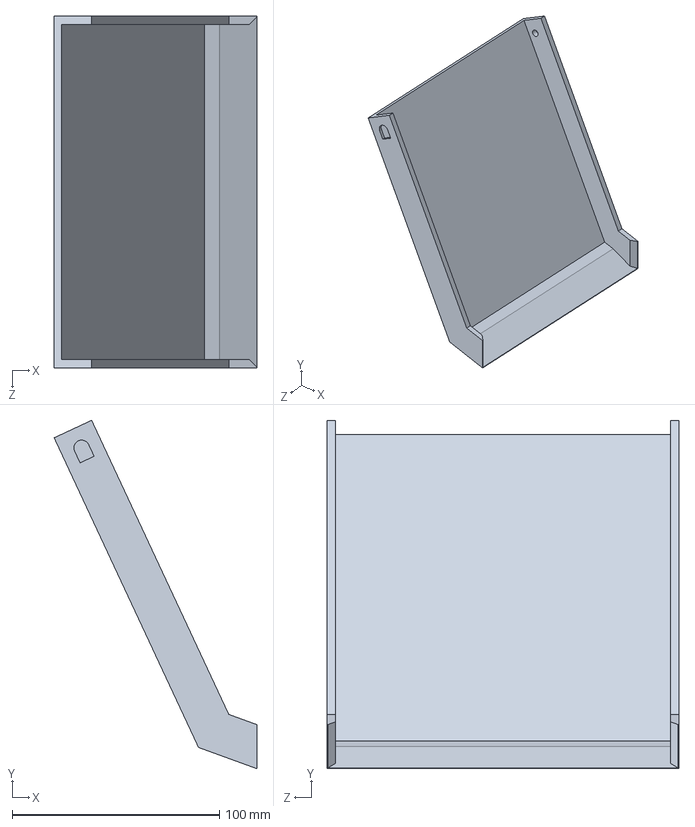
[picture p163: CAD file, 2024-04-27]
MechanicalStructure/小车结构/cth/铲斗.SLDPRT
97.9 x 168.3 x 170.0 mm
