Blake-John/SchoolRobotMatch/MechanicalStructure/小车结构/TT130支架.SLDPRT

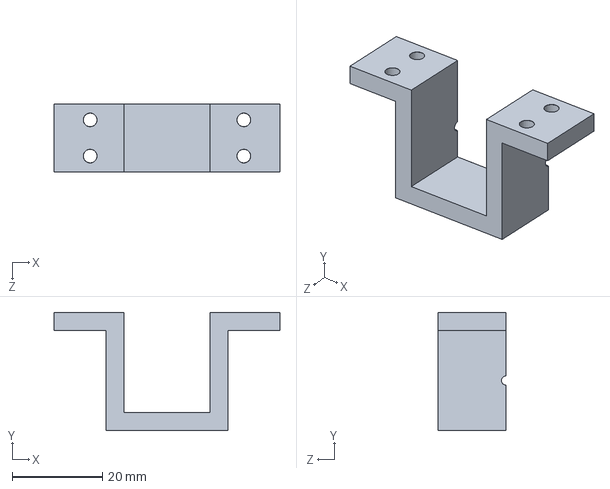
[picture p164: CAD file, 2024-04-27]
MechanicalStructure/小车结构/TT130支架.SLDPRT
50.0 x 26.2 x 15.0 mm
