Blake-John/SchoolRobotMatch/MechanicalStructure/小车结构/cth/传送带2.SLDPRT

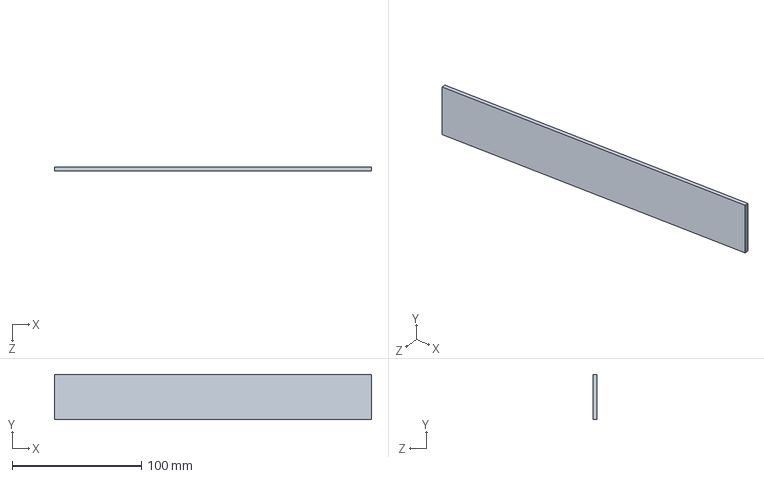
[picture p165: CAD file, 2024-04-27]
MechanicalStructure/小车结构/cth/传送带2.SLDPRT
245.0 x 35.0 x 3.00 mm
