Blake-John/SchoolRobotMatch/MechanicalStructure/小车结构/Mearm/夹爪驱动杆.SLDPRT

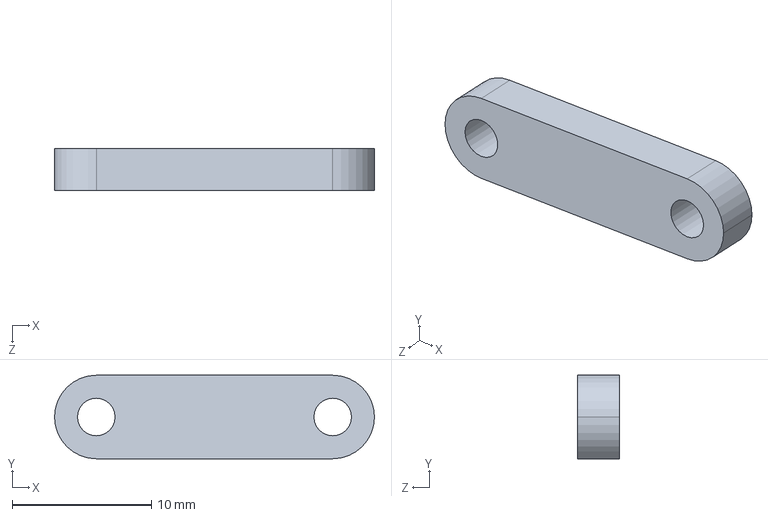
[picture p166: CAD file, 2024-04-27]
MechanicalStructure/小车结构/Mearm/夹爪驱动杆.SLDPRT
23.0 x 6.00 x 3.00 mm
