Blake-John/SchoolRobotMatch/MechanicalStructure/小车结构/背板.SLDPRT

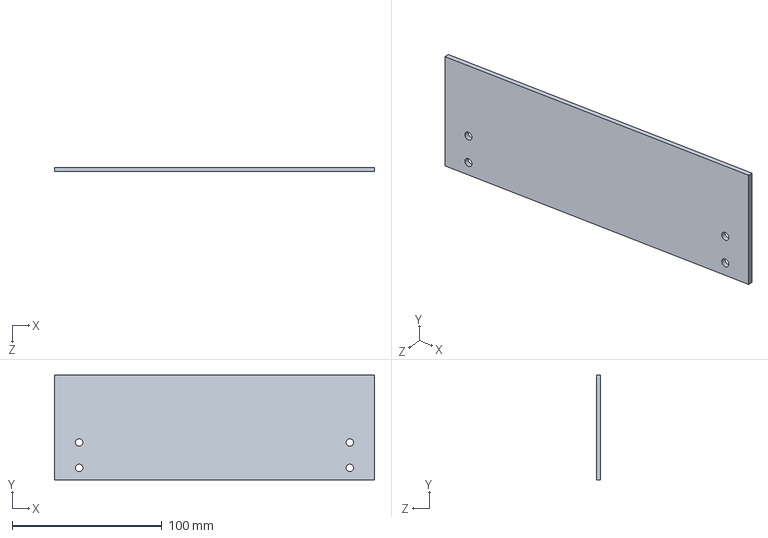
[picture p167: CAD file, 2024-02-24]
MechanicalStructure/小车结构/背板.SLDPRT
214.0 x 70.0 x 3.00 mm
