Blake-John/SchoolRobotMatch/MechanicalStructure/小车结构/cth/传送带3.SLDPRT

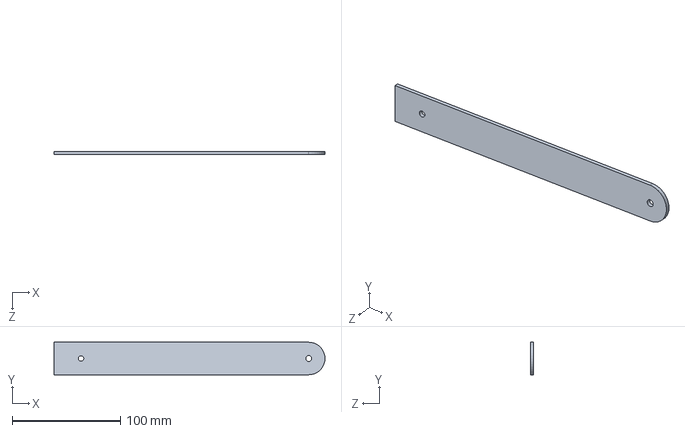
[picture p168: CAD file, 2024-04-27]
MechanicalStructure/小车结构/cth/传送带3.SLDPRT
250.0 x 30.0 x 3.00 mm
