Blake-John/SchoolRobotMatch/MechanicalStructure/小车结构/Mearm/M3×10内六角螺钉.SLDPRT

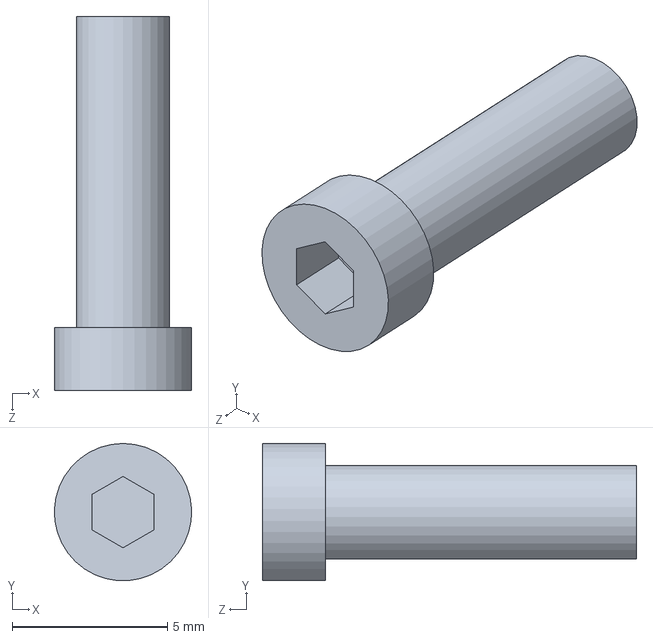
[picture p169: CAD file, 2024-04-27]
MechanicalStructure/小车结构/Mearm/M3×10内六角螺钉.SLDPRT
4.41 x 4.41 x 12.0 mm
