Blake-John/SchoolRobotMatch/MechanicalStructure/小车结构/舵盘.SLDPRT

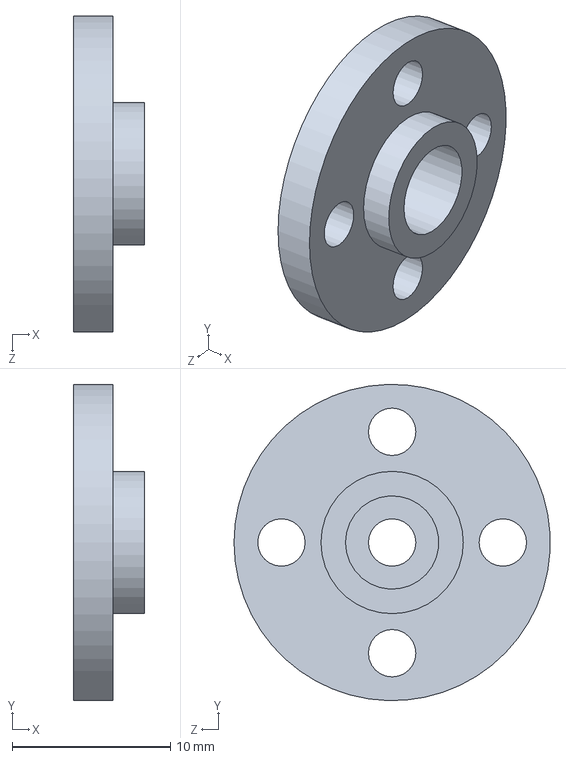
[picture p170: CAD file, 2024-02-24]
MechanicalStructure/小车结构/舵盘.SLDPRT
4.50 x 20.0 x 20.0 mm
