Blake-John/SchoolRobotMatch/MechanicalStructure/小车结构/cth/齿条.SLDPRT

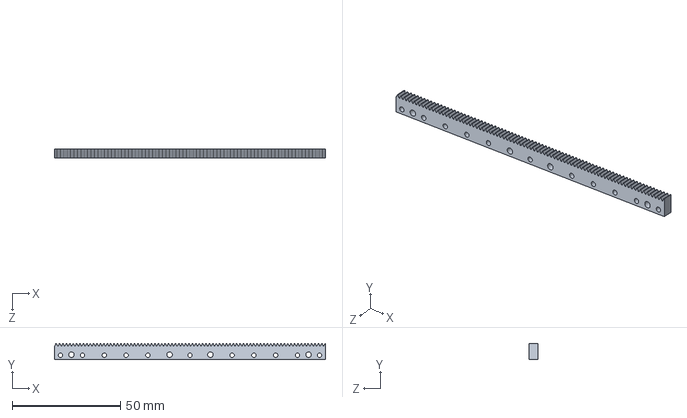
[picture p171: CAD file, 2024-04-27]
MechanicalStructure/小车结构/cth/齿条.SLDPRT
125.0 x 7.50 x 4.00 mm
