Blake-John/SchoolRobotMatch/MechanicalStructure/小车结构/Mearm/左臂根部.SLDPRT

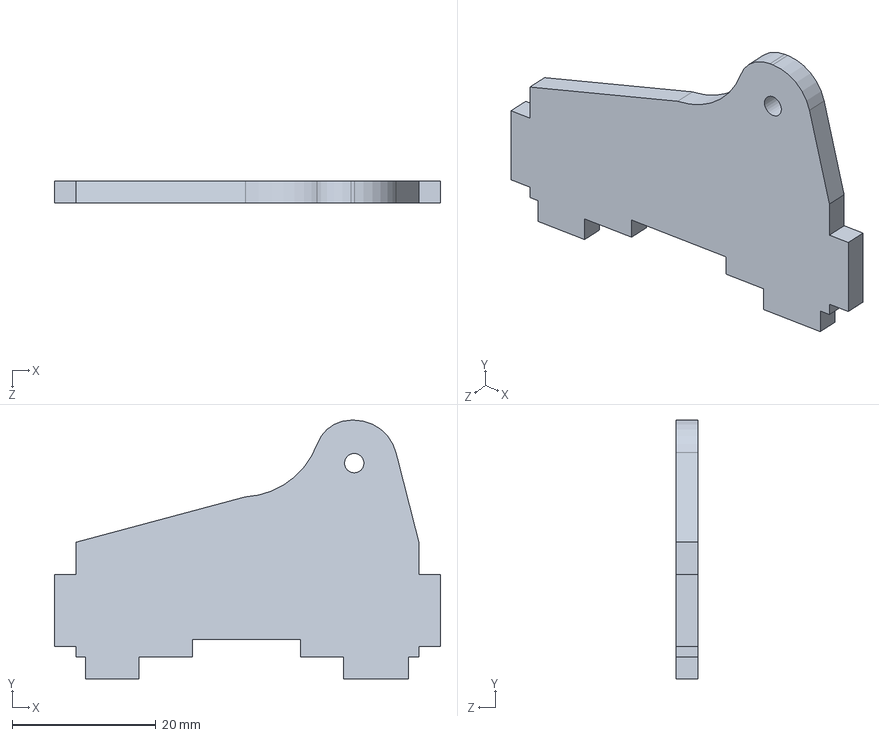
[picture p172: CAD file, 2024-04-27]
MechanicalStructure/小车结构/Mearm/左臂根部.SLDPRT
53.7 x 36.0 x 3.00 mm
