Blake-John/SchoolRobotMatch/MechanicalStructure/小车结构/cth/活动件2.SLDPRT

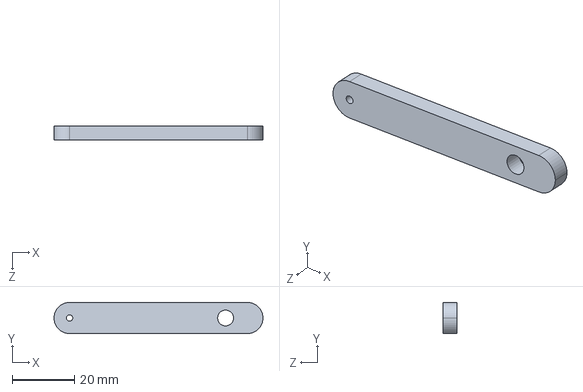
[picture p173: CAD file, 2024-04-27]
MechanicalStructure/小车结构/cth/活动件2.SLDPRT
67.0 x 10.0 x 4.50 mm
