Blake-John/SchoolRobotMatch/MechanicalStructure/小车结构/Mearm/左臂关节.SLDPRT

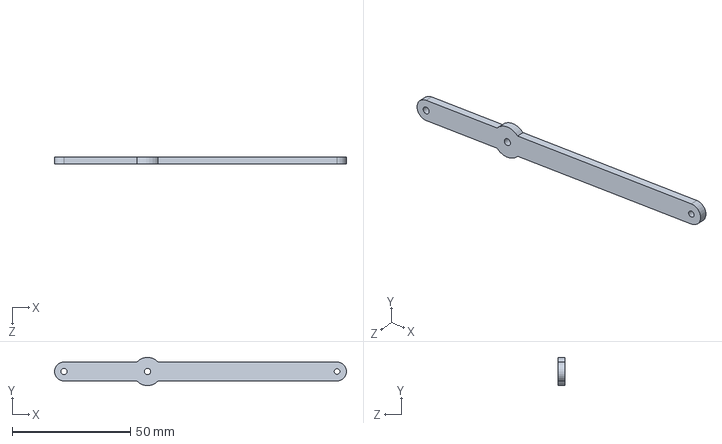
[picture p174: CAD file, 2024-04-27]
MechanicalStructure/小车结构/Mearm/左臂关节.SLDPRT
123.2 x 11.9 x 3.00 mm
