Blake-John/SchoolRobotMatch/MechanicalStructure/小车结构/Mearm/舵机限位器.SLDPRT

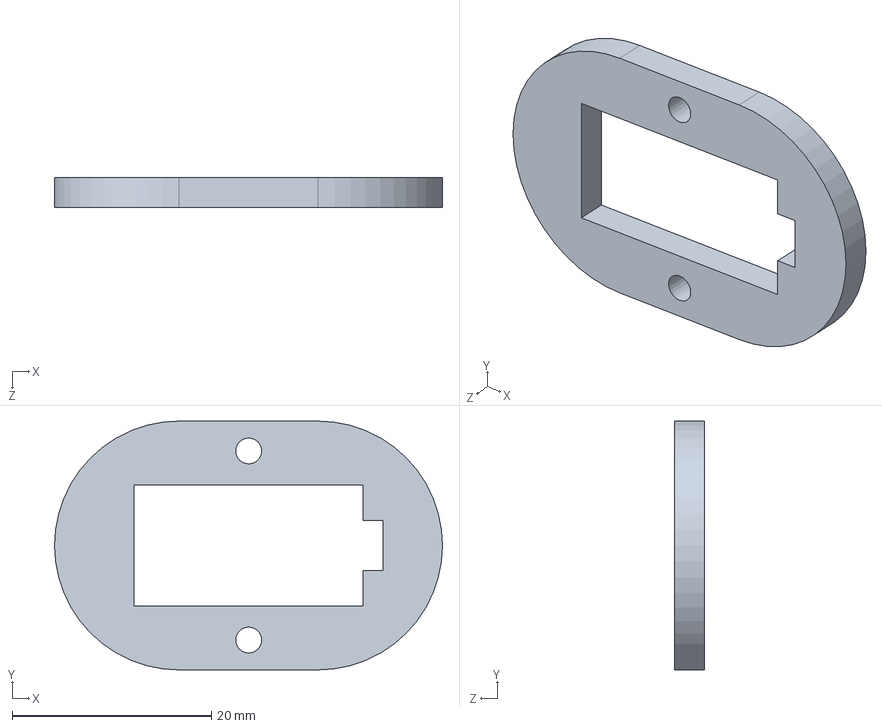
[picture p175: CAD file, 2024-04-27]
MechanicalStructure/小车结构/Mearm/舵机限位器.SLDPRT
39.0 x 25.0 x 3.00 mm
