Blake-John/SchoolRobotMatch/MechanicalStructure/小车结构/Mearm/左夹.SLDPRT

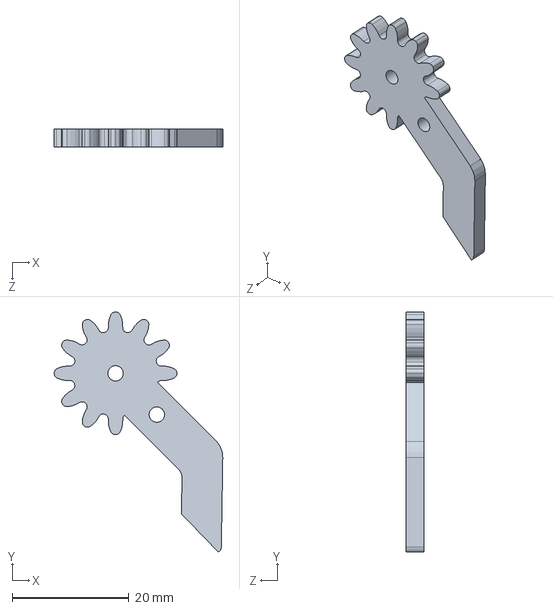
[picture p176: CAD file, 2024-04-27]
MechanicalStructure/小车结构/Mearm/左夹.SLDPRT
28.9 x 41.1 x 3.00 mm
