Blake-John/SchoolRobotMatch/MechanicalStructure/小车结构/Mearm/连杆(异型).SLDPRT

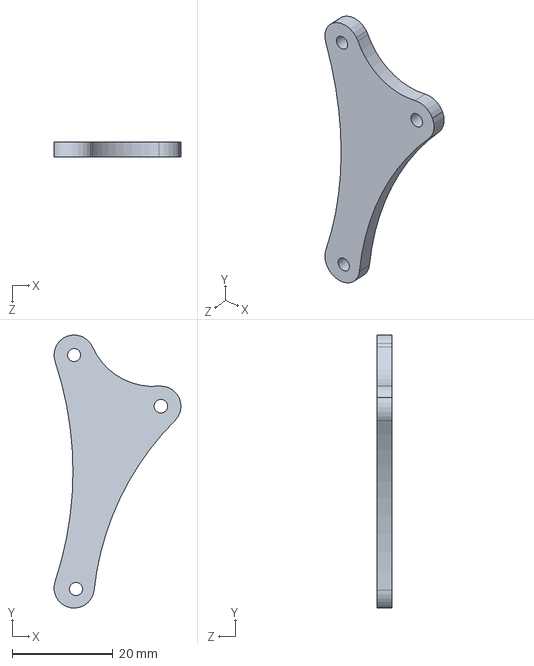
[picture p177: CAD file, 2024-04-27]
MechanicalStructure/小车结构/Mearm/连杆(异型).SLDPRT
25.2 x 54.2 x 3.00 mm
