Blake-John/SchoolRobotMatch/MechanicalStructure/小车结构/Mearm/次级底板.SLDPRT

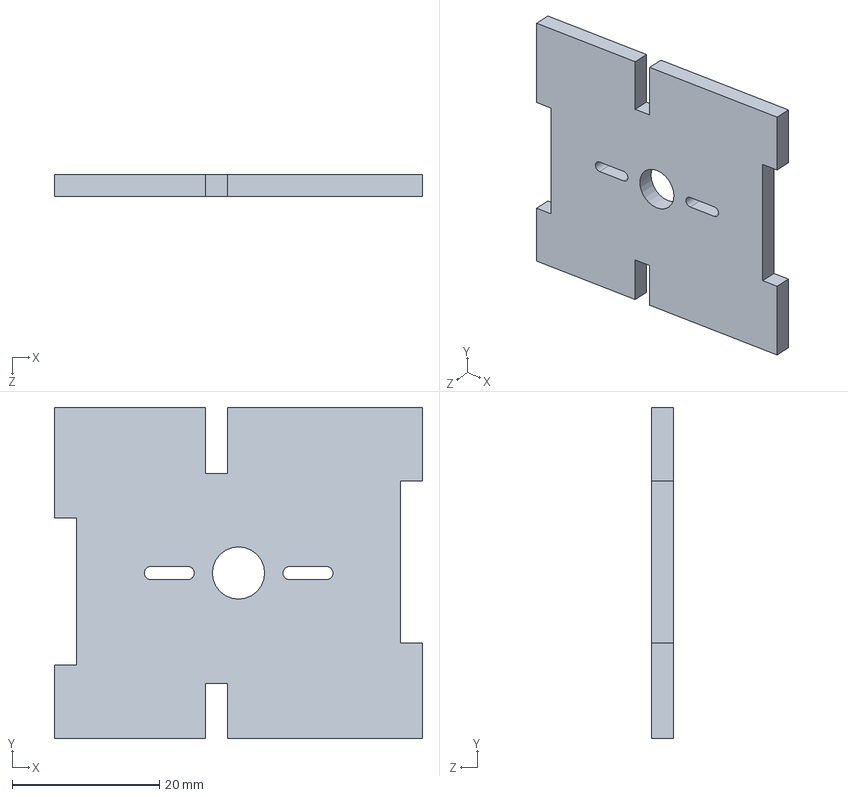
[picture p178: CAD file, 2024-04-27]
MechanicalStructure/小车结构/Mearm/次级底板.SLDPRT
50.0 x 45.0 x 3.00 mm
