Blake-John/SchoolRobotMatch/MechanicalStructure/小车结构/Mearm/舵机舵片-单侧-长.SLDPRT

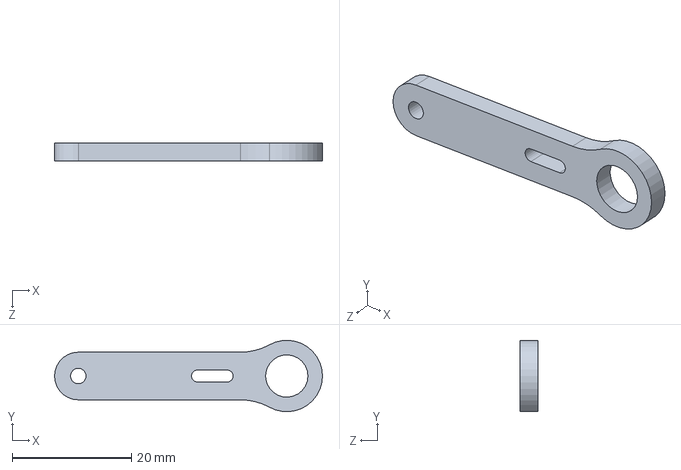
[picture p179: CAD file, 2024-04-27]
MechanicalStructure/小车结构/Mearm/舵机舵片-单侧-长.SLDPRT
45.0 x 12.0 x 3.00 mm
