Blake-John/SchoolRobotMatch/MechanicalStructure/小车结构/Mearm/舵机舵片-双侧等长.SLDPRT

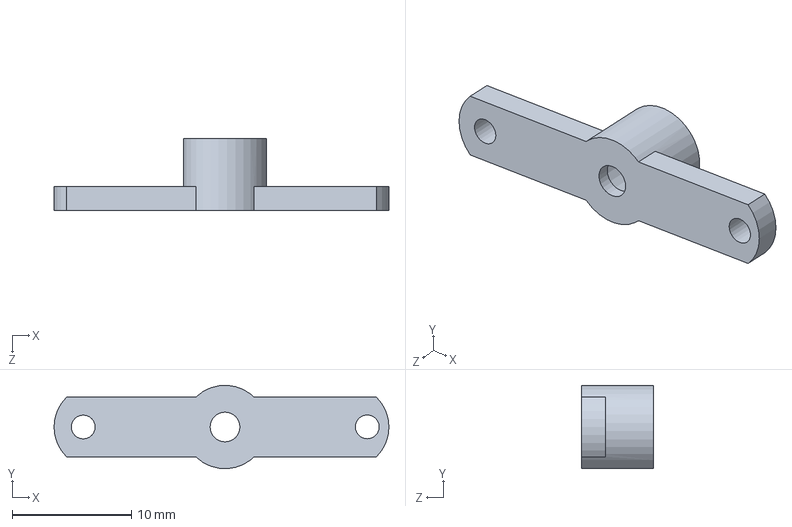
[picture p180: CAD file, 2024-04-27]
MechanicalStructure/小车结构/Mearm/舵机舵片-双侧等长.SLDPRT
28.1 x 6.99 x 6.00 mm
