Blake-John/SchoolRobotMatch/MechanicalStructure/小车结构/Mearm/舵机鞍座(下).SLDPRT

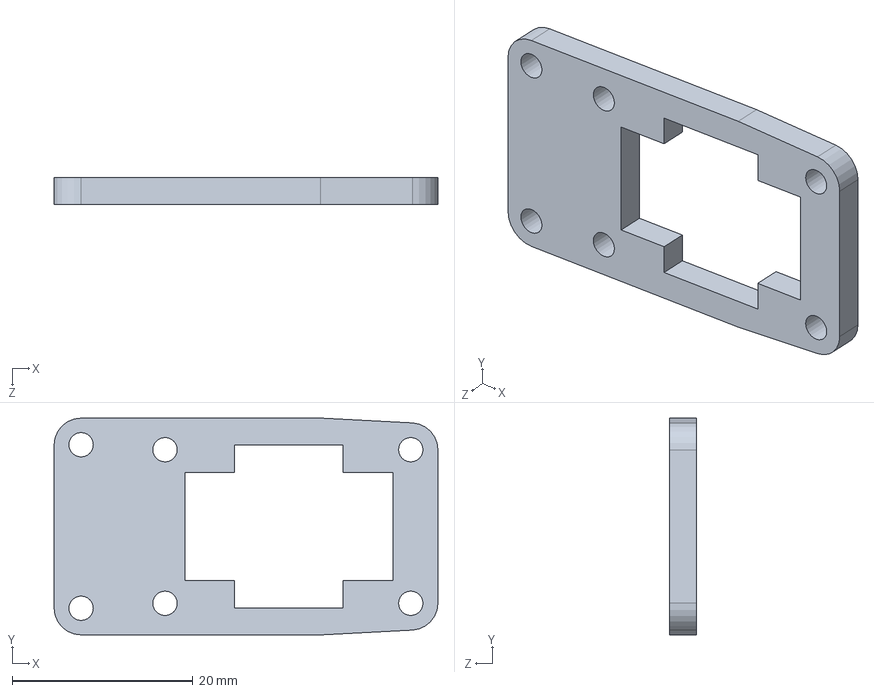
[picture p181: CAD file, 2024-04-27]
MechanicalStructure/小车结构/Mearm/舵机鞍座(下).SLDPRT
42.5 x 24.0 x 3.00 mm
