Blake-John/SchoolRobotMatch/MechanicalStructure/小车结构/Mearm/M3×20内六角螺钉.SLDPRT

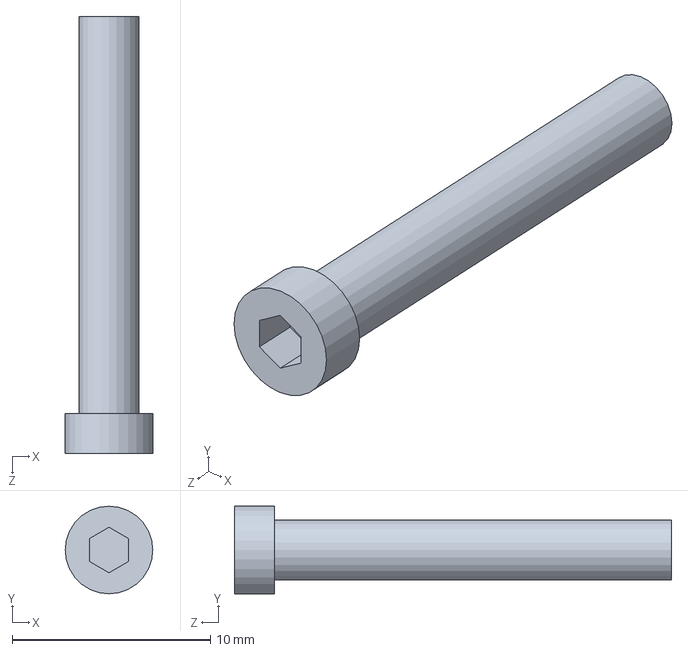
[picture p182: CAD file, 2024-04-27]
MechanicalStructure/小车结构/Mearm/M3×20内六角螺钉.SLDPRT
4.42 x 4.42 x 22.0 mm
