Blake-John/SchoolRobotMatch/MechanicalStructure/小车结构/Mearm/夹爪.SLDPRT

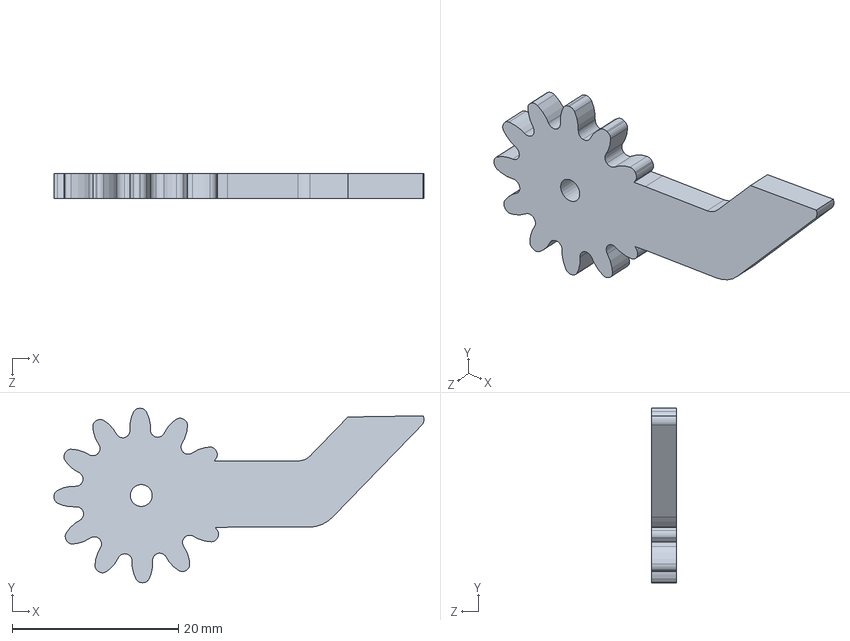
[picture p183: CAD file, 2024-04-27]
MechanicalStructure/小车结构/Mearm/夹爪.SLDPRT
44.5 x 21.0 x 3.00 mm
