Blake-John/SchoolRobotMatch/MechanicalStructure/小车结构/Mearm/底板.SLDPRT

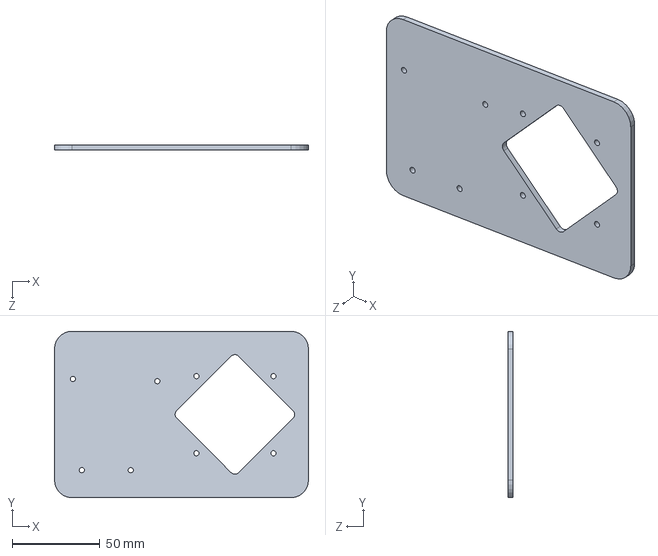
[picture p184: CAD file, 2024-04-27]
MechanicalStructure/小车结构/Mearm/底板.SLDPRT
145.0 x 95.0 x 3.00 mm
