Blake-John/SchoolRobotMatch/MechanicalStructure/小车结构/Mearm/臂间支撑架-基部.SLDPRT

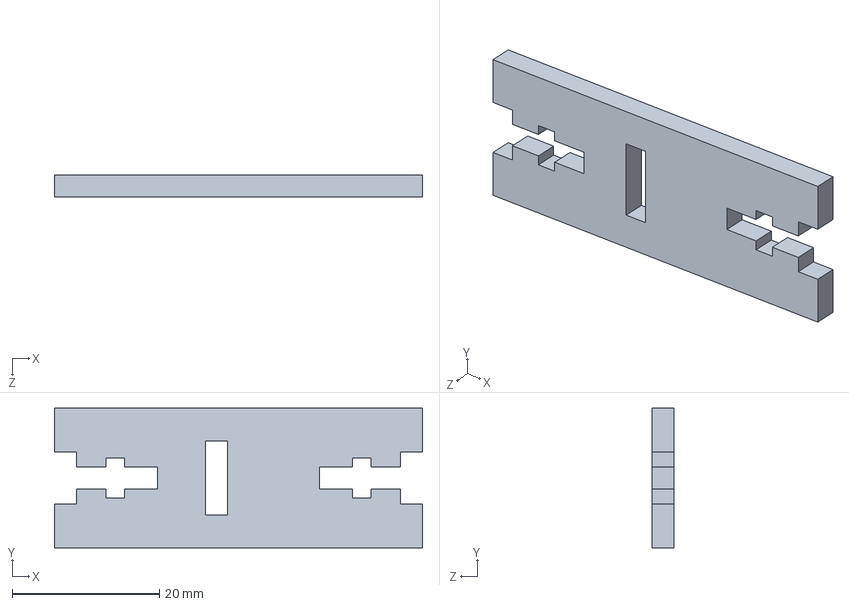
[picture p185: CAD file, 2024-04-27]
MechanicalStructure/小车结构/Mearm/臂间支撑架-基部.SLDPRT
50.0 x 19.0 x 3.00 mm
