Blake-John/SchoolRobotMatch/MechanicalStructure/小车结构/Mearm/左臂连接件.SLDPRT

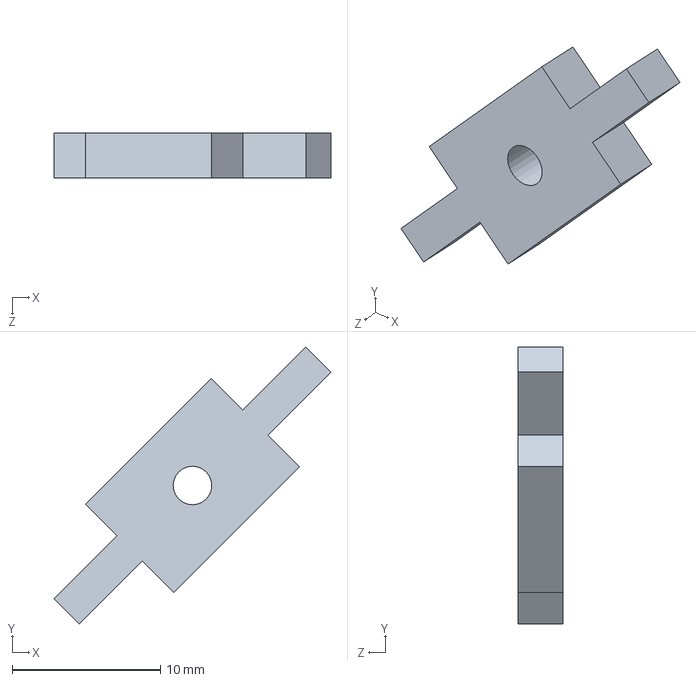
[picture p187: CAD file, 2024-04-27]
MechanicalStructure/小车结构/Mearm/左臂连接件.SLDPRT
18.7 x 18.7 x 3.00 mm
