Blake-John/SchoolRobotMatch/MechanicalStructure/小车结构/Mearm/枢轴夹板.SLDPRT

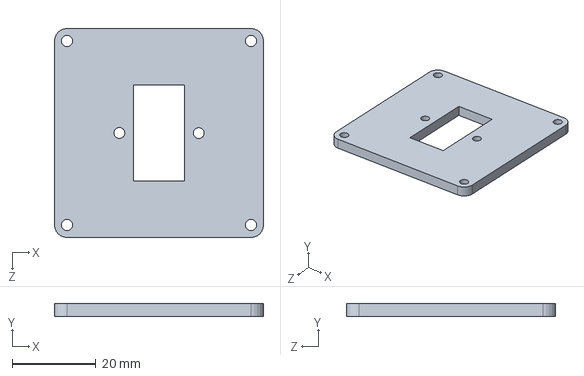
[picture p188: CAD file, 2024-04-27]
MechanicalStructure/小车结构/Mearm/枢轴夹板.SLDPRT
50.0 x 3.00 x 50.0 mm
