Blake-John/SchoolRobotMatch/MechanicalStructure/小车结构/Mearm/连杆.SLDPRT

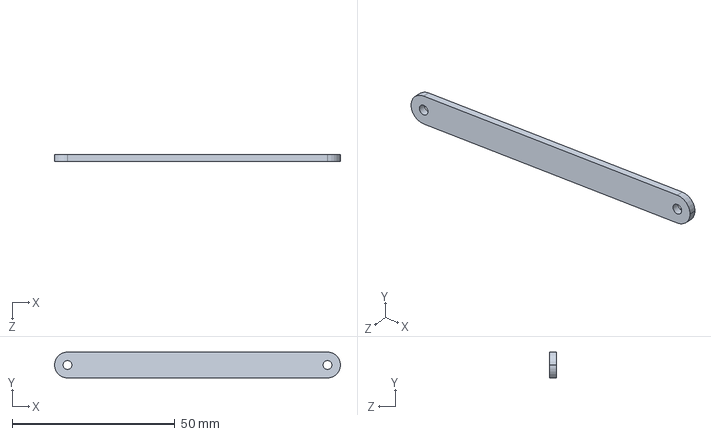
[picture p190: CAD file, 2024-04-27]
MechanicalStructure/小车结构/Mearm/连杆.SLDPRT
88.0 x 8.00 x 2.00 mm
