Blake-John/SchoolRobotMatch/MechanicalStructure/小车结构/Mearm/垫片.SLDPRT

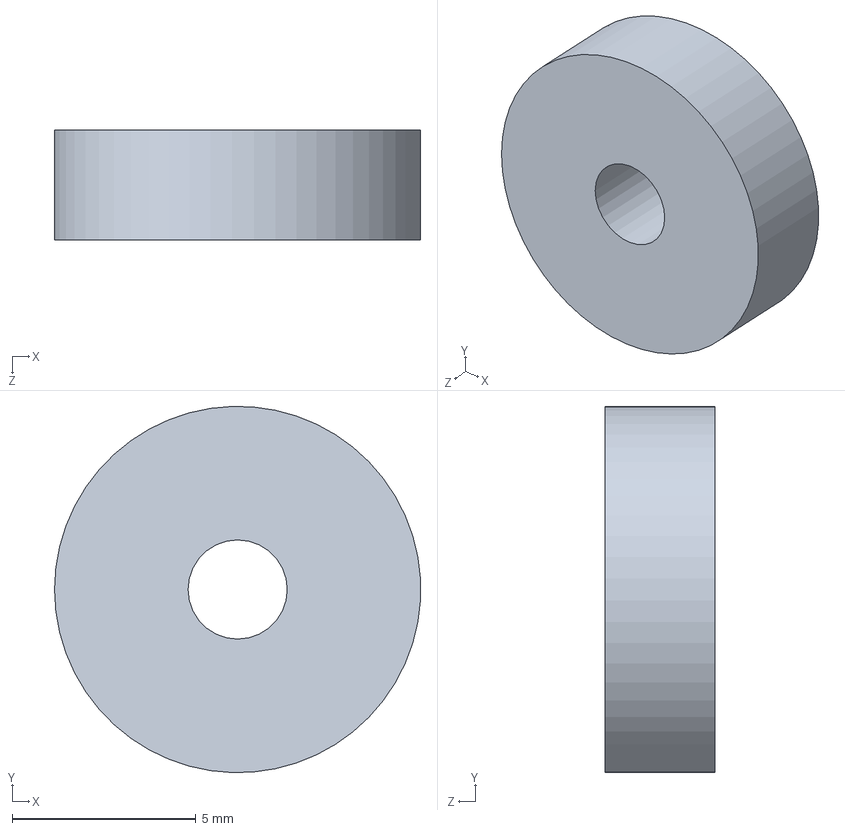
[picture p192: CAD file, 2024-04-27]
MechanicalStructure/小车结构/Mearm/垫片.SLDPRT
9.97 x 9.97 x 3.00 mm
