Blake-John/SchoolRobotMatch/MechanicalStructure/小车结构/Mearm/舵机舵片-单侧.SLDPRT

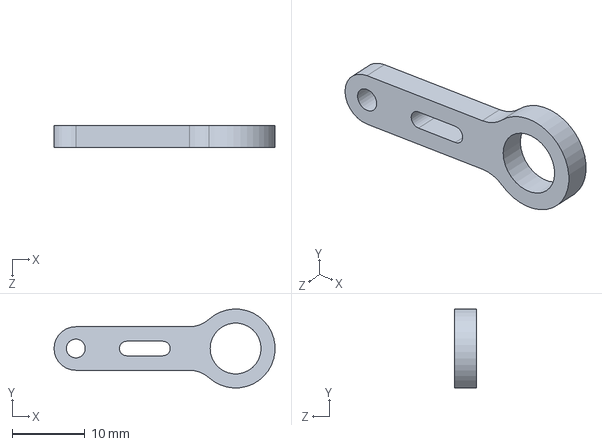
[picture p193: CAD file, 2024-02-24]
MechanicalStructure/小车结构/Mearm/舵机舵片-单侧.SLDPRT
30.4 x 10.9 x 3.00 mm
