Blake-John/SchoolRobotMatch/MechanicalStructure/小车结构/Mearm/螺母.SLDPRT

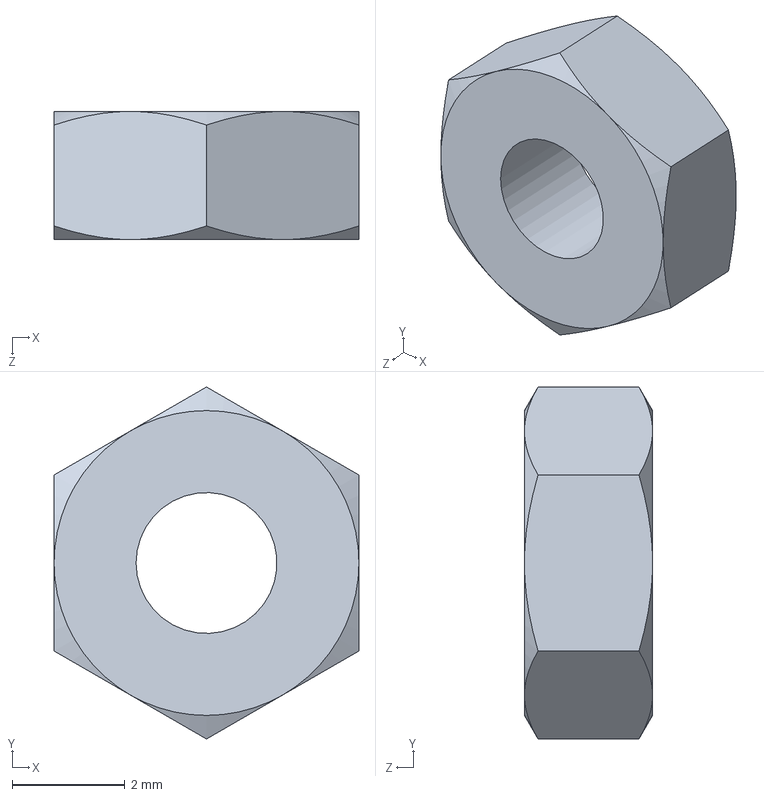
[picture p194: CAD file, 2024-02-24]
MechanicalStructure/小车结构/Mearm/螺母.SLDPRT
5.41 x 6.25 x 2.28 mm
