Blake-John/SchoolRobotMatch/MechanicalStructure/小车结构/cth/铲.SLDASM

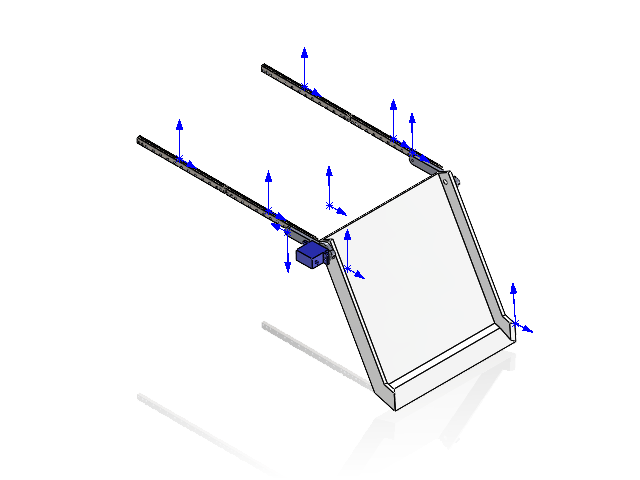
[picture p195: CAD file, 2024-04-27]
MechanicalStructure/小车结构/cth/铲.SLDASM
复件 铲斗^铲
齿条 x 4
舵机-SG90
活动杆
活动件2
