Blake-John/SchoolRobotMatch/ComputerVision/debugging/filtering/test2.png

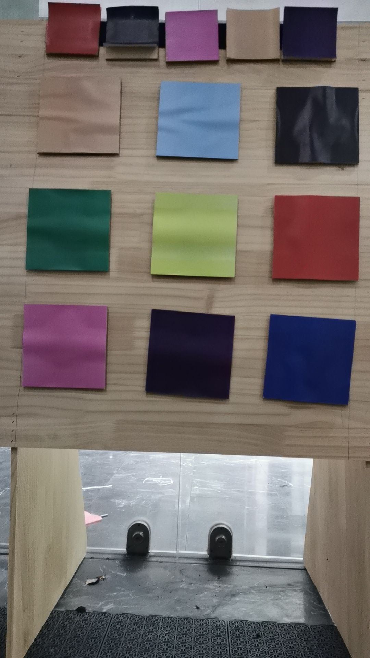
ComputerVision/debugging/filtering/test2.png
