Blake-John/SchoolRobotMatch/ComputerVision/Modules/Calibration/imgs/25.jpg

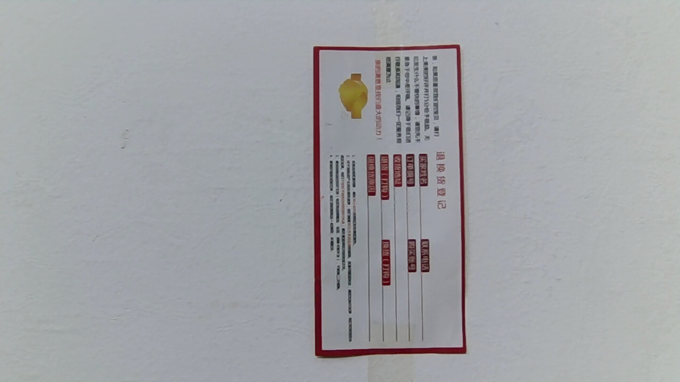
ComputerVision/Modules/Calibration/imgs/25.jpg
