Blake-John/SchoolRobotMatch/ComputerVision/Modules/Calibration/imgs/45.jpg

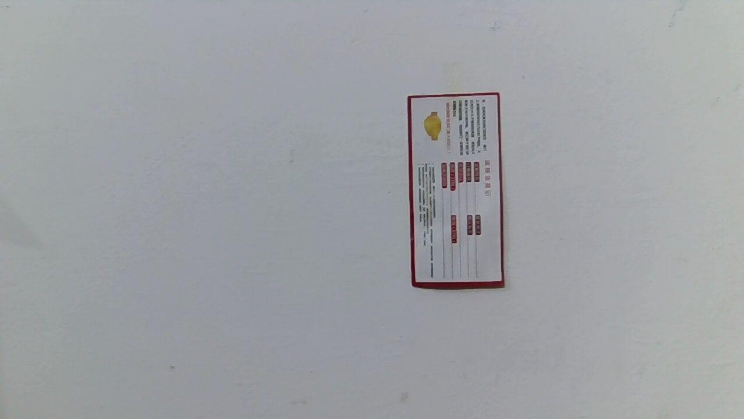
ComputerVision/Modules/Calibration/imgs/45.jpg
