Blake-John/SchoolRobotMatch/ComputerVision/Modules/Calibration/imgs/55.jpg

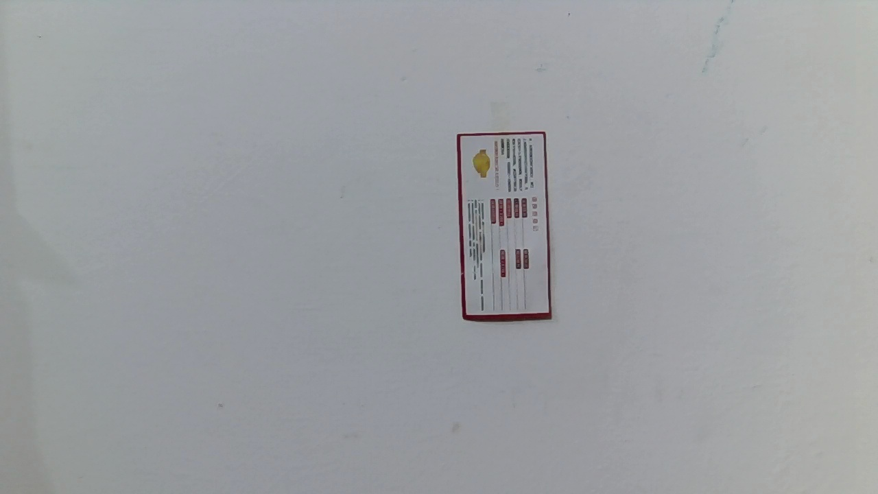
ComputerVision/Modules/Calibration/imgs/55.jpg
