Blake-John/SchoolRobotMatch/ComputerVision/Modules/Calibration/imgs/60.jpg

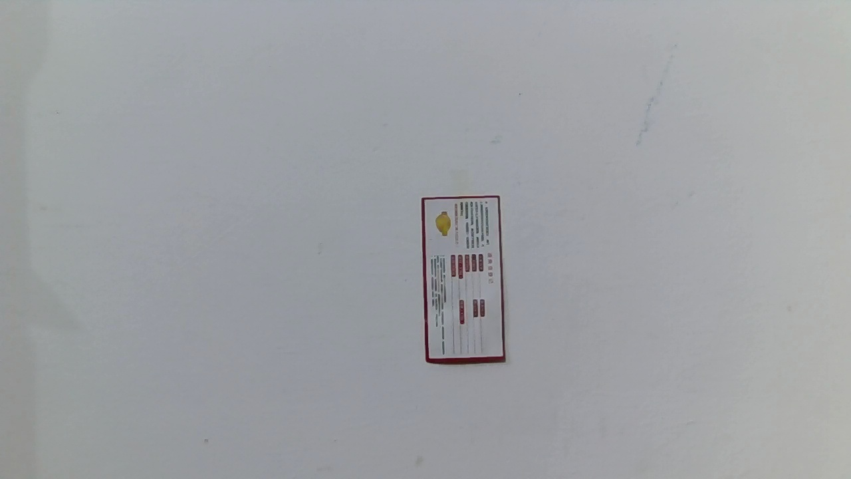
ComputerVision/Modules/Calibration/imgs/60.jpg
