Blake-John/SchoolRobotMatch/ComputerVision/Modules/Calibration/imgs/75.jpg

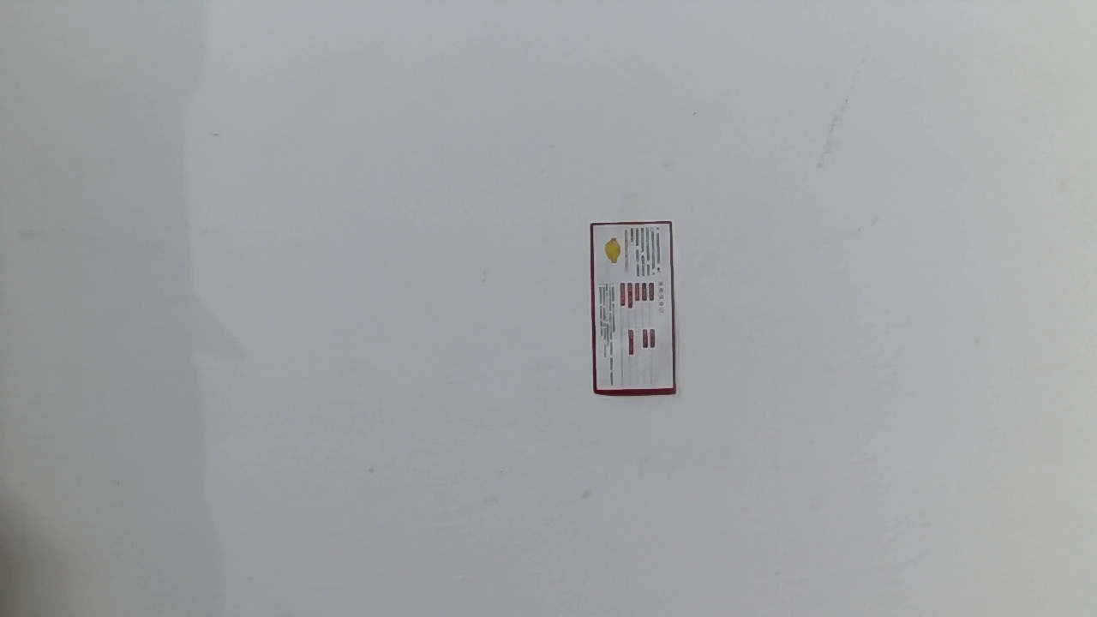
ComputerVision/Modules/Calibration/imgs/75.jpg
