Blake-John/SchoolRobotMatch/ComputerVision/debugging/ColorPicker/imgs/15.jpg

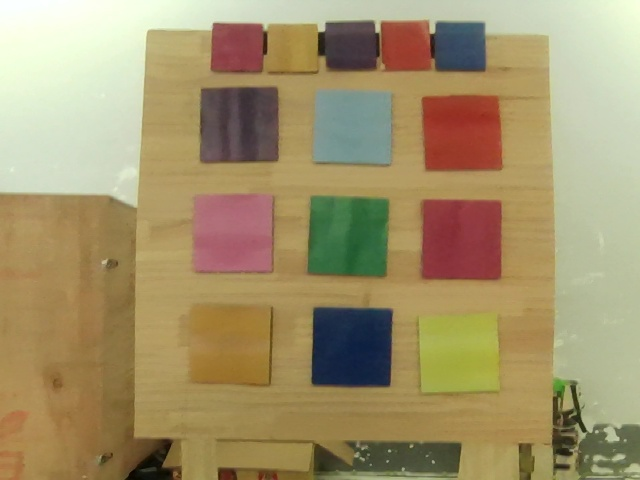
ComputerVision/debugging/ColorPicker/imgs/15.jpg
