Blake-John/SchoolRobotMatch/ComputerVision/debugging/ColorPicker/imgs/34.jpg

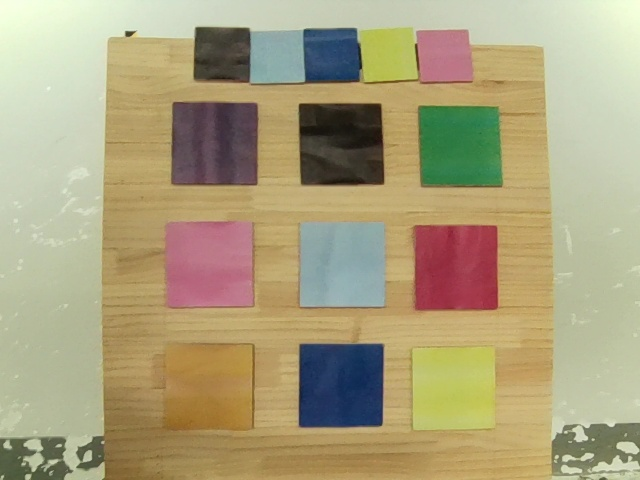
ComputerVision/debugging/ColorPicker/imgs/34.jpg
