Blake-John/SchoolRobotMatch/ComputerVision/debugging/ColorPicker/imgs/35.jpg

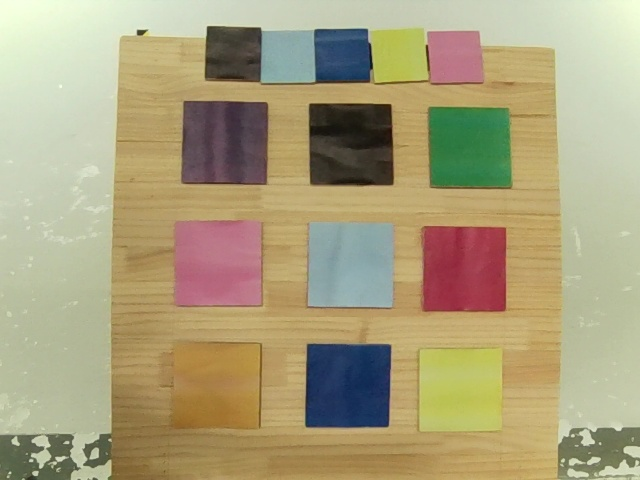
ComputerVision/debugging/ColorPicker/imgs/35.jpg
