Blake-John/SchoolRobotMatch/ComputerVision/debugging/ColorPicker/imgs/37.jpg

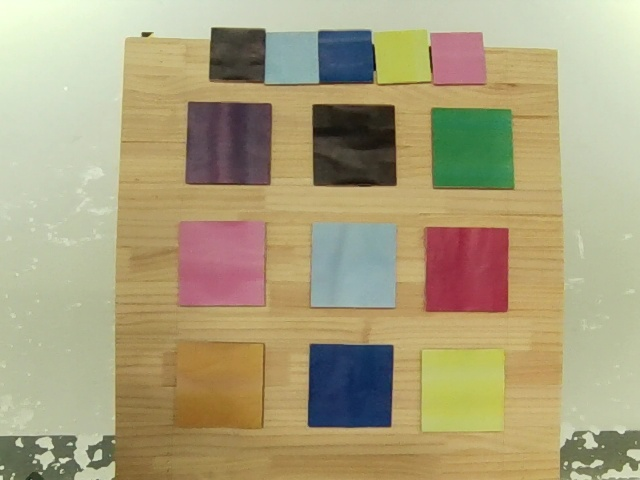
ComputerVision/debugging/ColorPicker/imgs/37.jpg
