Blake-John/SchoolRobotMatch/ComputerVision/debugging/ColorPicker/imgs/434.jpg

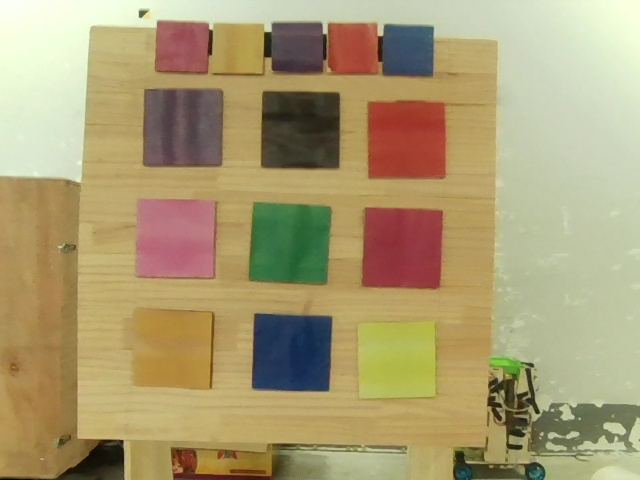
ComputerVision/debugging/ColorPicker/imgs/434.jpg
