Blake-John/SchoolRobotMatch/ComputerVision/debugging/filtering/56.jpg

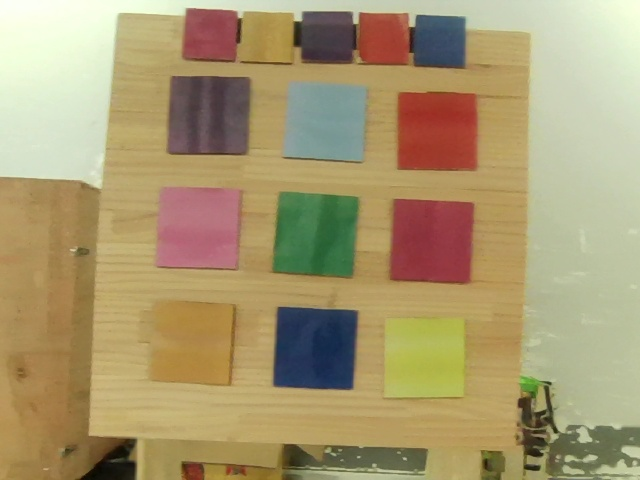
ComputerVision/debugging/filtering/56.jpg
