Blake-John/SchoolRobotMatch/MicroController/MajorControl_Source/DriveControl/Core/Inc/motorcontrol.h

//
// Created by DTS on 2024/3/11.
//
#include "tim.h"
#include "usart.h"

#ifndef DRIVECONTROL_MOTORCONTROL_H
#define DRIVECONTROL_MOTORCONTROL_H

void Motor_Init(void);
#endif //DRIVECONTROL_MOTORCONTROL_H
