Blake-John/SchoolRobotMatch/MicroController/MajorControl_Source/RemoteController/Core/Inc/menucontrol.h

//
// Created by DTS on 2024/3/8.
//

#ifndef REMOTECONTOLLER_MENUCONTROL_H
#define REMOTECONTOLLER_MENUCONTROL_H

void Control_Down();
void Control_Up();
void Control_Init();
void Menu_Sec_Init();
#endif //REMOTECONTOLLER_MENUCONTROL_H
