Blake-John/SchoolRobotMatch/MicroController/MajorControl_Source/RobotMatchZET6/Core/Inc/servocontrol.h

//
// Created by DTS on 2024/3/10.
//

#ifndef ROBOTMATCHZET6_SERVOCONTROL_H
#define ROBOTMATCHZET6_SERVOCONTROL_H
void Shovel_Down();
void Shovel_Up();
void Roller_Up();
void Roller_Down();
void Rack_Out();
void Rack_In();
void Sustainer_Up();
void Sustainer_Down();
#endif //ROBOTMATCHZET6_SERVOCONTROL_H
