Blake-John/SchoolRobotMatch/MicroController/SerialMCU/Hardware/inc/OLED_Font.h

#pragma once

#include "stm32f10x.h"

/*OLED字模库，宽8像素，高16像素*/
static const uint8_t OLED_F8x16[][16] = 
{
	0x00,0x00,0x00,0x00,0x00,0x00,0x00,0x00,
	0x00,0x00,0x00,0x00,0x00,0x00,0x00,0x00,//  0
	
	0x00,0x00,0x00,0xF8,0x00,0x00,0x00,0x00,
	0x00,0x00,0x00,0x33,0x30,0x00,0x00,0x00,//! 1
	
	0x00,0x10,0x0C,0x06,0x10,0x0C,0x06,0x00,
	0x00,0x00,0x00,0x00,0x00,0x00,0x00,0x00,//" 2
	
	0x40,0xC0,0x78,0x40,0xC0,0x78,0x40,0x00,
	0x04,0x3F,0x04,0x04,0x3F,0x04,0x04,0x00,//# 3
	
	0x00,0x70,0x88,0xFC,0x08,0x30,0x00,0x00,
	0x00,0x18,0x20,0xFF,0x21,0x1E,0x00,0x00,//$ 4
	
	0xF0,0x08,0xF0,0x00,0xE0,0x18,0x00,0x00,
	0x00,0x21,0x1C,0x03,0x1E,0x21,0x1E,0x00,//% 5
	
	0x00,0xF0,0x08,0x88,0x70,0x00,0x00,0x00,
	0x1E,0x21,0x23,0x24,0x19,0x27,0x21,0x10,//& 6
	
	0x10,0x16,0x0E,0x00,0x00,0x00,0x00,0x00,
	0x00,0x00,0x00,0x00,0x00,0x00,0x00,0x00,//' 7
	
	0x00,0x00,0x00,0xE0,0x18,0x04,0x02,0x00,
	0x00,0x00,0x00,0x07,0x18,0x20,0x40,0x00,//( 8
	
	0x00,0x02,0x04,0x18,0xE0,0x00,0x00,0x00,
	0x00,0x40,0x20,0x18,0x07,0x00,0x00,0x00,//) 9
	
	0x40,0x40,0x80,0xF0,0x80,0x40,0x40,0x00,
	0x02,0x02,0x01,0x0F,0x01,0x02,0x02,0x00,//* 10
	
	0x00,0x00,0x00,0xF0,0x00,0x00,0x00,0x00,
	0x01,0x01,0x01,0x1F,0x01,0x01,0x01,0x00,//+ 11
	
	0x00,0x00,0x00,0x00,0x00,0x00,0x00,0x00,
	0x80,0xB0,0x70,0x00,0x00,0x00,0x00,0x00,//, 12
	
	0x00,0x00,0x00,0x00,0x00,0x00,0x00,0x00,
	0x00,0x01,0x01,0x01,0x01,0x01,0x01,0x01,//- 13
	
	0x00,0x00,0x00,0x00,0x00,0x00,0x00,0x00,
	0x00,0x30,0x30,0x00,0x00,0x00,0x00,0x00,//. 14
	
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
	
	0x00,0x00,0x00,0x00,0xFF,0x00,0x00,0x00,
	0x00,0x00,0x00,0x00,0xFF,0x00,0x00,0x00,//| 92
	
	0x00,0x02,0x02,0x7C,0x80,0x00,0x00,0x00,
	0x00,0x40,0x40,0x3F,0x00,0x00,0x00,0x00,//} 93
	
	0x00,0x06,0x01,0x01,0x02,0x02,0x04,0x04,
	0x00,0x00,0x00,0x00,0x00,0x00,0x00,0x00,//~ 94
};
